lukketsvane/GK4_TRIXIG/assets/generated/gen_26_05/06_ideation_grids/trixig_260526_u157_square-loop-concept-board.png

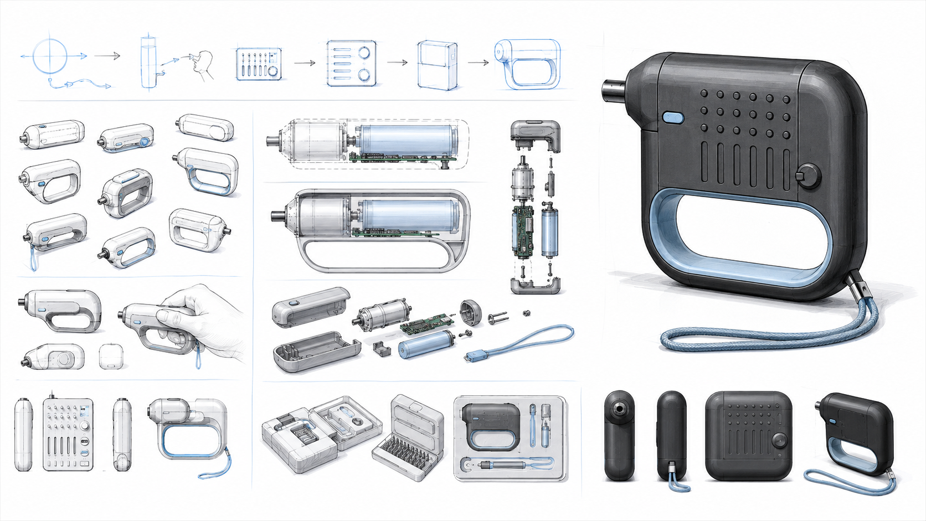
assets/generated/gen_26_05/06_ideation_grids/trixig_260526_u157_square-loop-concept-board.png
