lukketsvane/GK4_TRIXIG/docs/deliverables/08_mai_konseptgjennomgang/3b_analyse_trixig.docx

3B-analyse: TRIXIG 3,6 V

Akse | Kjernesvar
Brukar | Ung-vaksen, 20–40 år, første heim, ingen verktøyerfaring, IKEA-kunde, estetisk sensibel, prisbevisst.
Bruksituasjon | Hjemme på parkett, dårleg arbeidsljos (difor LED i nesen), kortintensiv 20–60 min, månader utan bruk mellom.
Bruksmåte | Pistolgrep, fast sekvens, retningsval er einaste reelle avgjerd, ingen koplingsbegrensing, brukaren må sjølv vurdera når skruen er ferdig.
