lukketsvane/GK4_TRIXIG/docs/project/trixig_konseptsprang.md

# TRIXIG — konseptsprang, ikkje arketypar

**Premiss:** Slutte å spørje "kva form skal ein skrutrekkar ha". Spørje i staden: *"kva er TRIXIG når han ikkje lenger er eit verktøy?"* — er han smykke, bordpynt, leppestift, klatreutstyr, fyllepenn, ikon? Kvar omramming gjev ein heilt annan brukaravtale.

Felles teknisk gulv (uansett konsept):
- 1 stk 18650-celle (ø18 × 65 mm)
- 1 stk gearmotor (ø25 × 60 mm) med utgåande aksel
- PCB (slank), trigger, USB-C-port

---

## KONSEPT 1 — KARABINIEREN
*Skrutrekkaren som lever på ryggsekken og veggkroken.*

Ikkje "verktøy i skuffa" — verktøy som heng saman med nøklane. Ein slank stav i anodisert aluminium med ein ekte klatrekarabin i enden. Når du går på fjellet, monterer ei IKEA-hylle, eller hjelper naboen — han er der. Statusobjekt for den som likar Olight, Leatherman, Lamy. Estetikk: kald metall, grå/svart/oliven, grov knurling, tydelege gjenger.

**Referanseunivers:** *EDC (every-day-carry), klatre, fyllepenn-presisjon*

| # | Referanse | Designar / år | Kva ein hentar |
|---|---|---|---|
| 1.1 | **Lamy 2000 fyllepenn** | Gerd A. Müller (Ulm-skulen), 1966 | Strikt sylinder, makrolon + børsta stål, knurla grep. Den definitive "edle staven". |
| 1.2 | **Olight i3T EOS lommelykt** | Olight | Single-cell EDC-arketype. Lommeklips. Knurling. |
| 1.3 | **Black Diamond HotForge karabin** | Black Diamond | Den tekniske karabinen, ikkje den dekorative. |
| 1.4 | **Leatherman Style PS** | Leatherman | Liten, klips, multifunksjonsspråk utan bling. |
| 1.5 | **Maglite Solitaire** | Anthony Maglica, 1988 (MoMA) | Single-cell ikon med nøkkelring-øye. |
| 1.6 | **Best Made Co. felling axe** | (kuratert) | Ulm møter Vermont. Korleis "verktøy" blir "objekt med sjel". |

---

## KONSEPT 2 — LEPPESTIFTEN (inversjonen)
*Ladaren er hovudobjektet. Skrutrekkaren er berre tuppen som skrur ut.*

Radikalt. Tenk Estée Lauder eller Diptyque parfymeflakong. På bordet ditt står ein vakker tubeform — kanskje keramikk, kanskje børsta messing, kanskje sandblåst glas — som ladar. Når du treng skru, vrir du toppen av: ut kjem den vesle motoren med chuck. Battericella sit i sokkelen og ladar induktivt. Kjøkkenkompatibel, soverom-kompatibel, gåvepakke-kompatibel.

**Referanseunivers:** *parfyme, sminke, ritualobjekt*

| # | Referanse | Designar / år | Kva ein hentar |
|---|---|---|---|
| 2.1 | **Aesop Marrakech parfymeflakong** | Aesop | Materialgravitas. Apotek-arv. |
| 2.2 | **Diptyque keramikklysstake** | Diptyque | Keramikkdock som *skjuler* funksjon. |
| 2.3 | **Tom Ford Black Orchid leppestift** | Tom Ford Beauty | Vekt, magnetlokk, klikk-følelse. |
| 2.4 | **Le Labo Santal 33 i flakong + boks** | Le Labo | Etiketten. Det handverka. |
| 2.5 | **Hermès Twilly perfume case** | Hermès | Skinn + metall = ritual. |
| 2.6 | **MUJI aroma diffuser, sylinder** | Naoto Fukasawa | Den japanske kjøkken-kompatible sylinderen. |

> Bonus: dette er det einaste konseptet som *opphøgjer ladinga til ein del av produktopplevinga* — jamfør Sonicare-glasset, men løfta til kosmetikk-nivå.

---

## KONSEPT 3 — BORDORNAMENTET
*Verktøyet som er for vakkert til å gøyme bort.*

Står på kjøkkenbenken som ei lita statue ved sida av Peugeot pepperkverna og Bialetti Moka. Vertikal totem, kanskje ovoid, kanskje konisk, i støypt aluminium eller olja eik. Bits står som ei lita krans rundt sokkelen — som krydder eller smykke. *Du eig han fordi han er fin.* Funksjonen er bonus.

**Referanseunivers:** *kjøkkenikon, bordtilbehør, italiensk handverk*

| # | Referanse | Designar / år | Kva ein hentar |
|---|---|---|---|
| 3.1 | **Bialetti Moka Express** | Alfonso Bialetti, 1933 | Det italienske kjøkkenikonet — funksjon som monument. |
| 3.2 | **Peugeot Paris u'Select pepperkvern** | Peugeot, 1874 (modell) | Tre + stål kolonne. 150 år utan å trenge fornying. |
| 3.3 | **Alessi 9090 espressokokar** | Richard Sapper, 1979 (Compasso d'Oro) | Stål-skulpturen. |
| 3.4 | **Jasper Morrison Mokka** for Alessi | Jasper Morrison, 2014 | Same arketype, supernormal-redux. |
| 3.5 | **Sori Yanagi støpejernspanne** | Sori Yanagi, 1953 | Japansk handverkstyngde. |
| 3.6 | **Eames House Bird** | Charles & Ray Eames, 1910-tal trefigur, gjort til ikon | Det reine bordobjektet utan funksjon. |
| 3.7 | **HAY Sowden kjelar** | George Sowden, 2017 | Korleis ein bryt opp ein tung form med flate fargar. |

---

## KONSEPT 4 — DET FOLDBARE OBJEKTET
*Ein kompakt blokk som klikkar opp i skruposisjon.*

Lukka: ein liten, slank ingot — passar i pennalet, jakkelomma, IKEA-skuffa. Opna: motorhuset svingar 90° eller 180° ut frå battericella og låsest med eit klikk. To stilbare posisjonar gjev anten *pistol* eller *inline*-bruk. Brukaren forhandlar grepet med produktet. Mekanisk dialog, ingen elektronikk.

**Referanseunivers:** *foldbart handverk, sveitsisk presisjon, modulærdesign*

| # | Referanse | Designar / år | Kva ein hentar |
|---|---|---|---|
| 4.1 | **Victorinox Pioneer Alox** | Victorinox, 1957 | Den ærlege foldemekanismen. Klikket. |
| 4.2 | **Olfa SVR-2 snap-blade kniv** | Olfa, Yoshio Okada, 1956 | Japansk teknisk ikon. Funksjonell glide. |
| 4.3 | **Black+Decker Gyro 4V** | (verktøy, men berre formreferanse) | Justerbart hovud — pivotmekanikken. |
| 4.4 | **BaByliss reise-hårfønar foldbar** | BaByliss | Kvardagsleg foldemekanikk i hushald. |
| 4.5 | **Joseph Joseph Elevate-skje med stative-fold** | Morph Design | Folde-leksis i kvardagskjøkken. |
| 4.6 | **Magis Chair_One stack-mekanisme** | Konstantin Grcic, 2003 | Korleis to volum låser i kvarandre. |
| 4.7 | **Vintage taske-reise-strykjern (1960-tal)** | Diverse | Den dramatiske transformasjonen lukka→open. |

---

## KONSEPT 5 — AMULETTEN
*Skrutrekkaren som heng på snor rundt halsen — eller på nøkkelringen, beltet, ryggsekken.*

Du gøymer han ikkje. Han er smykke. Liten, tung, taktil — i messing, titan eller børsta stål. Snorøye eller karabin innebygd. Hentar arven til mekaniske lommeur, militær-dogtags, og Tile/AirTag. Den eksisterande TRIXIG-snora er allereie eit hint — me dyrkar det.

**Referanseunivers:** *smykke, lommeur, militær-EDC, hi-tech wearables*

| # | Referanse | Designar / år | Kva ein hentar |
|---|---|---|---|
| 5.1 | **Apple AirTag** | Apple ID, 2021 | Liten, runda, premium polert. Snor-kompatibel. |
| 5.2 | **Tile Mate** | Tile, 2012 | Den vesle smarte-tinga som lever på nøkkelring. |
| 5.3 | **Casio F-91W på snor** | Casio, 1989 | Folkets EDC-amulett. |
| 5.4 | **Vintage Patek Philippe lommeur** | Patek Philippe | Premium "objekt-i-vest-lomma". |
| 5.5 | **Nendo dog-tag-baserte produkt** | Oki Sato / Nendo | Japansk minimalisme i wearable. |
| 5.6 | **Bauhaus dogtag-medaljongar** | Diverse Bauhaus-arv | Geometrisk reduksjon på snor. |
| 5.7 | **Carhartt WIP karabin-nøkkelring** | Carhartt | Korleis "industrielt" blir "modesmykke". |

---

## KONSEPT 6 — STEINEN
*Skulpturell pebble som ligg i handflata. Ingen synleg knapp.*

Henta frå sjøsleip stein og japansk wabi-sabi. Heile kroppen er trigger — du klemmer eller pressar mot skruen, motoren startar. Materiale: matt PA12 i jordtonar, eller terazzo-aktig støypt resin. Ingen merker, ingen logo. Ligg på vindaugskarmen som ein souvenir frå ein strand.

**Referanseunivers:** *japansk minimalisme, naturskulptur, Without Thought*

| # | Referanse | Designar / år | Kva ein hentar |
|---|---|---|---|
| 6.1 | **±0 humidifier (rund)** | Naoto Fukasawa, 2003 | Without Thought-arketypen. |
| 6.2 | **Isamu Noguchi Akari-lampe** | Isamu Noguchi, 1951+ | Organisk volum med papirsjel. |
| 6.3 | **Sori Yanagi Butterfly Stool** | Sori Yanagi, 1954 | Korleis to enkle skåler dannar ein heil ting. |
| 6.4 | **MUJI utan-logo-objekter** | MUJI / Fukasawa, Sam Hecht | Reduksjonsfilosofi. |
| 6.5 | **Lemnos Riki Clock** | Riki Watanabe, 1950-tal | Trereduksjon. |
| 6.6 | **Brâncuși "L'Oiseau dans l'espace"** | Constantin Brâncuși, 1923 | Skulpturreferansen — proporsjonar utan funksjon. |
| 6.7 | **Aesop Skin Care-flakongar (matt brun)** | Aesop | Kjelder for taktile matte overflater. |

---

## KONSEPT 7 — BUEN (bow drill-renessansen)
*Tilbake til den eldste boreteknologien menneske kjenner — bogeboret. Reframe-a som elektrisk objekt.*

Ein C-form. Pekefingeren ligg inne i C-en. Den eine enden er motor + chuck, den andre er battericella. Rom for handa i midten. Resultatet ser ut som augenbrynscurlar, fele-bue eller arkaisk handsmykke. Ergonomisk: aksial reaksjonskraft tas opp diagonalt mot underarmen, ikkje vinkelrett som med L-form. Du *omfamnar* verktøyet.

**Referanseunivers:** *arkaiske verktøy, musikkinstrument, kosmetikkverktøy*

| # | Referanse | Designar / år | Kva ein hentar |
|---|---|---|---|
| 7.1 | **Bogebor (arkeologisk)** | Mennesket, ~5000 f.Kr. | Den opphavlege boreformen. Symbolsk vekt. |
| 7.2 | **Shu Uemura augenbrynscurlar** | Shu Uemura | C-form på ergonomisk masterclass. |
| 7.3 | **Pernambuco felebue** | Tradisjon | Spenninga, balansen, det handverka. |
| 7.4 | **Marc Newson Lockheed Lounge** | Marc Newson, 1986 | Kontinuerleg flytande overflate. |
| 7.5 | **Eames LCW-stol** | Charles & Ray Eames, 1946 | Korleis to volum koplast med ein bro. |
| 7.6 | **Fritz Hansen Series 7 ryggstø** | Arne Jacobsen, 1955 | Kontinuerleg kurve som strukturelt prinsipp. |
| 7.7 | **Theragun PRO triangelhandtak** | Therabody | Moderne C/triangel-grep. |

---

## KONSEPT 8 — TVILLINGSYLINDRANE (magnetisk modulær)
*To like sylindrar som klikkar saman magnetisk. Kvar for seg er dei eigne objekt. Saman er dei skrutrekkar.*

Sylinder A: battericella, lader, USB-C, lyser i botn. Sylinder B: motor, chuck, knapp. Du tek dei med deg kvar for seg — A blir powerbank, B blir manuell skrutrekkar. Saman: eit bordlangt objekt med magnet i midten som lader pinge-følelsen til AirPods-etui og MagSafe.

**Referanseunivers:** *magnetisk premium, modulærleik, Apple ID*

| # | Referanse | Designar / år | Kva ein hentar |
|---|---|---|---|
| 8.1 | **Apple MagSafe-ladar** | Apple, 2020 | Magnet-klikket. Det elegante "snap". |
| 8.2 | **B&O Beoplay E8 etui + buds** | Jakob Wagner, 2017 | Skinn + magnet. |
| 8.3 | **Foreo Luna play + dock** | Foreo | Kompakt sylinder + sokkel. |
| 8.4 | **Nendo "Twin Drink" jingle-konsept** | Nendo / Oki Sato | To former som forhandlar. |
| 8.5 | **Hermès silkkrok-ringar** | Hermès | Ritualet å samle/skille. |
| 8.6 | **Olympus Pen-F kamera** | Olympus, 2016 | Premium tvillingelement (kropp + linse). |

---

## KONSEPT 9 — SLIK-SOM-MÅLEBANDET (Stanley FatMax-energi)
*Eit kompakt rektangulært ingot — som eit målebånd, ein USB-C lommepowerbank, eller ein vintage sigarettetui — der bittet popper ut frå ein kortside.*

Tenk Stanley FatMax målebånd møter Apple-design. Eller LaCie Rugged hard disk. Du klikkar ein knapp på toppen, motorhuset glir ut frå ein side. Battericella ligg flat under, motoren ligg horisontalt. Form blir noko aldri sett før i verktøykategorien — meir lik ein gadget enn ein drill.

**Referanseunivers:** *gadget, vintage tool, premium consumer electronics*

| # | Referanse | Designar / år | Kva ein hentar |
|---|---|---|---|
| 9.1 | **Stanley FatMax målebånd** | Stanley, 1990-tal | Industriell rektangulær arketype. |
| 9.2 | **LaCie Rugged Mini SSD** | LaCie / Neil Poulton, 2009 | Premium ingot med gummi. |
| 9.3 | **Vintage Dunhill sigarettetui** | Dunhill, 1920-tal | Smal rektangulær luksus. |
| 9.4 | **Olfa cutters i lommeformat** | Olfa | Skyte-mekanisme. |
| 9.5 | **Zippo lighter** | George Blaisdell, 1933 | Klikket. Det ergonomiske rektangelet. |
| 9.6 | **Braun ET-66 kalkulator** | Dieter Rams, 1987 | Den minimalistiske rektangulære disiplinen. |

---

## KORT SAMANDRAG — kva du tek inn i Figma

```
KONSEPT          MENTAL OMRAMMING                  KJERNE-REFERANSE
1 KARABINIER     verktøy → EDC-utstyr              Lamy 2000 + Black Diamond
2 LEPPESTIFT     verktøy → kosmetikk-ritual        Aesop + Tom Ford
3 BORDORNAMENT   verktøy → kjøkkenmonument         Bialetti + Peugeot
4 FOLDBAR        verktøy → sveitsisk transformer    Victorinox + Olfa
5 AMULETT        verktøy → smykke / wearable       AirTag + Casio F-91W
6 STEIN          verktøy → wabi-sabi-objekt        Fukasawa + Brâncuși
7 BUE            verktøy → arkaisk omfavning       Bogebor + felebue
8 TVILLING       verktøy → magnetisk modul         MagSafe + B&O E8
9 INGOT          verktøy → premium gadget          Stanley + LaCie
```

---

## Anbefaling for første runde i Figma

Velg **3 konsept** å utvikle vidare — eg foreslår spennvidde:
- **Konsept 2 (LEPPESTIFT)** — heilt utfordrande mental omramming
- **Konsept 4 (FOLDBAR)** — teknisk-mekanisk ambisjon
- **Konsept 1 (KARABINIER)** eller **5 (AMULETT)** — relasjon til den eksisterande snora

Då har du éit konsept som er romantisk, eitt som er mekanisk, eitt som er kvardagsleg-EDC. Tre forskjellige forteljingar å teste mot brukargruppa.

Når du har plassert referansane: sei frå, så hjelper eg deg med pakkings-skissar og ergonomi-resonnement for kvart konsept.

[Open konseptdokumentet](computer://C:\Users\Shadow\Documents\GitHub\GK4_TRIXIG\TRIXIG_konseptsprang.md)
