lukketsvane/GK4_TRIXIG/docs/project/note.md

La oss starte med å rydde i koden. Gå deretter inn i skisser-mappa og gi alle filene bedre navn etter en tydelig konvensjon, for eksempel skisse_01, skisse_02 osv.

Etter det skal du gå nøye gjennom hvert eneste bilde, vurdere og sammenligne dem, helt til vi står igjen med de 3–10 desidert beste. Disse kan vi så arbeide videre med.
