lukketsvane/GK4_TRIXIG/docs/brand/brandmark_trixigplus.md

# Brand-mark for TRIXIG+

*Designforslag for ordmerke til Trixig+, basert på prinsippet om at typografi kan ha innebygd produkt-semantikk. Knytt til Formføringsplansje_11mai.md (verdiord: truverdig).*

Forfattar: [Studentnamn]
Dato: 27. april 2026

---

## Premiss

Eit ordmerke for eit verktøy bør ikkje vera ein generisk wordmark plassert oppå produktet. Han bør innehalda noko av det produktet *gjer*. Den dekonstruerte IKEA-logoen som er referert som inspirasjon (sjå `referanse/`) gjer akkurat det: K-en blir ein retningspil, E-en får ein skrue-spor-slits, A-en blir ein flatpakk-trekant. Tre einkle gestar, kvar med innebygd semantikk.

Brand-marken for TRIXIG+ tek same prinsipp og oversett han til prosjektets eigen kontekst.

## Forslag

```
   ┌──────────────────────────────────────┐
   │                                      │
   │   T R I X I G +                      │
   │   ─       ─    ↑                     │
   │   |       |    fjørkontakt-          │
   │   |       |    indikator             │
   │   |       |                          │
   │   slits   slits                      │
   │   (T-bit) (Pozi)                     │
   │                                      │
   └──────────────────────────────────────┘
```

Tre tekstlege grep, ein fysisk gest:

**1. T-en har Torx-stjerne i horizontal slik.** Ein lett asymmetrisk seksstjerne-form innfelt i vertikal-stammen. Les seg som T på avstand, som Torx-bit-snitt på nært hald. Refererer direkte til dei seks Torx T10-skruvene som er sjølve identiteten til Trixig+ ('reparerbar').

**2. G-en har eit Pozidriv-tverr i opninga.** Den karakteristiske Pozidriv-stjerna (kryss + diagonal) er innfelt der G-en sluttar inn mot midten. Sub-tilt nok til å lesast som G på avstand; tydeleg på nært hald.

**3. Plus-symbolet er ein status-indikator.** "+" etter TRIXIG har dei fire armane med liten rund prikk i kvar — som dei fire status-LED-prikkane på skrutrekkaren sin bakvy. Plusset er både ord-element og funksjonsmotiv.

## Typografi-grunnlag

Skrifttype: ein modifisert Verdana Bold (IKEAs eigen referanse-grotesk) eller Akzidenz Grotesk Bold som svensk-historisk parallell. Om Verdana brukast, skal ho strammast horizontal med 5 % for ikkje å bli IKEA-original-identifisk.

Kerning: jamn, ikkje optisk. TRIXIG+ skal lesast som éin block, ikkje som spaced lettering.

Vekt: 700 (Bold). Ikkje Black — det blir for industrielt. Ikkje Regular — det forsvinn på lite skala.

Storleik på produkt: minimum 8 mm høgd for å vera lesbar etter debossing i ABS.

## Fargesystem

To variant:

**Variant A — full IKEA-logikk:** IKEA-blå (Pantone 280 C, omtrent #003F94) som dominant flate, IKEA-gul (Pantone 116 C, omtrent #FFD600) som typografi-farge. Kun til marknadsføring og digitalt bruk.

**Variant B — produkt-debossing:** Berre debossa direkte i ABS, ingen paint fill. Reint material, ingen farge. Dette er den primære varianten på sjølve verktøyet — i tråd med "truverdig"-verdiordet (material som det det er).

Variant B vinn for produktet sjølv. Variant A finst kun i digital og trykt kommunikasjon.

## Plassering på produktet

På Trixig+ sin venstre side, debossa direkte i ABS, plassert på den glatte flata mellom partingline og stroppfeste-løkka. Storleik: 12 mm høgd. Synleg, men ikkje dominerande — han kommuniserer brand utan å skrika.

På batteripakken (om reservebatteri produserast separat): same merke debossa, men 8 mm høgd, plassert sentrert.

## Gjenkjenning på avstand

Test: prøv merket på 30 cm, 1 m, 3 m. Kva les seg?

- 30 cm: TRIXIG+, alle detaljar synlege (Torx-T, Pozi-G, prikkar i +)
- 1 m: TRIXIG+, glatt typografi, prikkar i + framleis synlege
- 3 m: TRIXIG, plus-symbolet glir saman til éin prikk

Den glidande oppløysinga er meininga. På avstand er merket ein kjend brand. På nært hald er han ein tale om produktet sin reparérbarheit. Brukaren oppdagar koplinga først når han faktisk har verktøyet i handa.

## Forhold til IKEA-master-merket

TRIXIG+ er sub-brand under IKEA. Brand-merket må difor co-eksistera med IKEA-logoen. To plasseringar:

**Lock-up (vertikal):** IKEA-logo over, TRIXIG+ under, separert av ein 2 mm tynn horisontal regel. Brukast på pakning og trykt materiale.

**Sub-merking (horisontal):** TRIXIG+ åleine, IKEA-logo i ein hjørne av pakninga separat. Brukast på sjølve produktet (ingen IKEA-logo direkte på verktøyet, kun TRIXIG+).

## Kva det ikkje er

Eit forsøk på å erstatta IKEA-merket. Den dekonstruerte IKEA-logoen i `referanse/` er inspirasjon for *prinsippet* (typografi med innebygd produkt-semantikk), ikkje for *biletet*. Brand-marken for TRIXIG+ skal ikkje sjå ut som ein modifisert IKEA-logo — det er forvirring og potensiell varemerke-konflikt.

## Vidare arbeid

Tre konkrete neste steg om brand-marken vert valt for vidareutvikling:

1. **Skissa T-en og G-en frihand.** Sjå om Torx-stjerna i T-stammen og Pozi-tverret i G-opninga faktisk fungerer typografisk, eller om dei vert for støyande.
2. **Test på reell ABS-modell.** Debossing-djupna avgjer leselegheit — skiltvanleg er 0,3–0,5 mm under overflate. Test på blåskum-modell først.
3. **Konsulter Anna Martine Nilsen** (kursveileder for brandmarkører) i veke 19 for kritisk gjennomgang før formføringsplansje-leveransen 11. mai.

---

*v1.0 — 27. april 2026. Inspirert av referansebilete i `referanse/` (dekonstruert IKEA-logo). Forslaget er konseptuelt og krev typografisk utvikling før produksjon.*
