lukketsvane/GK4_TRIXIG/docs/project/formfringsplansje_11mai.md

# Formføringsplansje — Trixig+

*GK4 V26 Modul 2. Innlevering Moodle innan måndag 11. mai 2026 kl. 09:00. Gjennomgang i gruppeseanse onsdag 13. mai med Nina Bjørnstad.*

Forfattar: [Studentnamn]
Dato: 11. mai 2026

---

## Tre verdiord

**Synleg. Stille. Truverdig.**

Verdiorda er valde for å samtidig (i) artikulera Trixig+ sin formdriver — radikal reparérbarheit gjort eksplisitt — og (ii) halda seg innanfor IKEA-DNAet, slik at produktet ikkje fell utanfor TRIXIG-serien sitt eksisterande visuelle vokabular. Dei tre orda dannar eit triangel: kvar av dei korrigerer ein moglig overdriving av dei to andre.

---

## Synleg

Synleg tyder at det funksjonelle prinsippet — at verktøyet er reparerbart — skal vera lesbart utan tekst. Dei seks Torx T10-skruvene står på utsida av kapslinga, ikkje under merkelapp. Status-LED-stripa er innfelt men ikkje gøymd. ISO-merkinga er innstøypt direkte i polymeren der ho synast under demontering. Ingenting er skjult under lim, klistreikon eller "design"-deksel.

Dette er ein invitasjon til å demontera, ikkje ein varsel om å la det vera. Synleg er den motgangen til "skapt mangel"-mekanismen — du kan ikkje skjula det du har bygd, og du kan ikkje by­byggja det du har vist fram.

**Referanseobjekt:** Festool ETS-rondellsliper (synleg modulær skruegjennomgang i grepet), Vola FS1 vasskran (mekanikken er synleg, ikkje skjult under design­chrom), Olivetti Lettera 22 (alle skruver kjente, alle deler nemlege).

**Visuelt vokabular:** flate, ærlege flater. Ingen falske partingslines. Ingen påklistra "feature"-dekk. Skruehovuda er fysisk reelle objekt på overflata. Synleg betyr ikkje teknisk nakent — det betyr at det funksjonelle vert oppløst som visuelt motiv.

---

## Stille

Stille tyder at produktet ikkje skrik. Det er ei reaksjon mot den dominerande retninga i forbrukar­elektroverktøy, der visuell aggresjon (skarpe vinklar, fluorescent grøn på Ryobi, signal-raud på Milwaukee, fettkokt mat-grafikk på DeWalt) er kommersielt korrelert med opplevd performanse. Trixig+ fullfører ikkje den tradisjonen.

Stille er òg eit IKEA-ord. TRIXIG-serien har allereie ein lågmælt tone — myk pistolform, dempa svart-grå-fargesetjing, ein einsleg orange aksent. Trixig+ tek dette tonefallet eit hakk lenger inn: oransje vert reservert til eit einaste relieff (pil-relieffet på den konvekse retningsbrytarsida) og éin enkelt lyspunkt (den aktive status-LEDen). Resten av produktet er monokromatisk svart-grå.

Stille er motgangen til opplevd-pris-inflasjon. Det er ein deklarasjon om at verktøyet ikkje treng å overtyda om kvaliteten sin gjennom signal — kvaliteten er den utskiftbare cella, dei opnande skallene, den asymmetriske brytaren. Forma sjølv held seg ut av vegen for funksjonen.

**Referanseobjekt:** Braun T1000 transistor­radio (Dieter Rams, lågmælt formspråk), Muji CD-spelar av Naoto Fukasawa (fråvær av visuell støy), Olivetti Valentine i den ikkje-røde versjonen.

**Visuelt vokabular:** myke radiar (R3 til R8), inga skarpe industri­vinklar, ein einsleg signaturfarge brukt med disiplin, typografi i einsleg vekt og storleik, ingen "extreme grip"-mønster i overstøp.

---

## Truverdig

Truverdig tyder at materialet ser ut som det det er. ABS-en er matt, ikkje gloss; han er svart, ikkje "soft-touch"-imitasjon av gummi. Stålet i bitsfestet er børsta, ikkje krom. Magneten er synleg som eit metallisk grått ringen; han er ikkje innebygd bak ei plastskilje. Aluminiumet i innvendige strukturelement (om det blir brukt) er anodisert i naturleg metallisk grå.

Dette er motgangen til "premium feel"-strategien som dominerer forbrukar­elektronikk: glansa overflater, krom-aksent, soft-touch-rubber, mat-svart-pulverlakk over termisk-mediokkar plast. Trixig+ avstår fordi avstand mellom material og uttrykk er sjølve kjelda til mistillit. Eit produkt som lyg om materialet sitt vil lyga om levetida si.

Truverdig er òg den tonefallet som produsent-bedrifta IKEA strever for å levera i sin breiare kommunikasjon, men ikkje alltid lukkast med. Trixig+ trekkjer dette ein millimeter lenger.

**Referanseobjekt:** Braun ET 88 kalkulator (knappar er knappar, plast er plast), Vitsoe 606 hyllesystem (aluminium i si rette form), Festool batteripakke (synleg mekanikk, ærleg material).

**Visuelt vokabular:** matt finish som standard, glans berre på funksjonelle overflater (børsta stål der friksjon krevjast), ingen fargelegging av material som ikkje treng det (ABS er svartpigmentert i støyping, ikkje sprøytemåla), pregnante tekstur skilnader mellom material­fraksjonar.

---

## Tilpassing til IKEA-brand og TRIXIG-serien

Trixig+ må kjennast som TRIXIG. Det betyr disiplin på tre dimensjonar:

**Form-DNA.** Den softe pistolforma med 110° grepvinkel er behaldt utan endring. Hovudradiar (R5 i grepets kontur, R8 i nesen) er behaldt. Den karakteristiske TRIXIG-stroppfeste-løkka i bakkant er behaldt. Endringane er konsentrert om dei *flatene* der dei opererer, ikkje om silhuetten.

**Farge-DNA.** Svart matt ABS pluss éin oransje aksent. Det er IKEAs eksisterande TRIXIG-palett. Forskjellen er at oransje vert *meir* disiplinert i Trixig+ — i originalen finst det nokre oransje detaljar fleire stader, i Trixig+ er han reservert til retningsbrytarens pil-relieff og éin status-LED. Mindre oransje, men oransje meir betydningsbærande.

**Detalj-DNA.** Skrifttype er IKEAs eigen Verdana-derivative for produkt­merking. Logo-plassering på underdelen av grepet, ved siden av stroppfestet, debossa utan paint fill. Modellbetegning "TRIXIG+" debossa, ikkje malt. Inga nye fargar, ingen nye fontar, ingen nye geometriske element.

**Brand-mark som ber semantikk.** Sjå `Brandmark_TrixigPlus.md` for forslag der TRIXIG+-ordmerket har Torx-stjerne innfelt i T-stammen, Pozidriv-kryss i G-opninga, og fire prikkar i plus-symbolet (refererer til status-LED-stripa). Inspirert av referansebilete i `referanse/` (dekonstruert IKEA-logo) der typografi har innebygd produkt-semantikk. Forslaget skal under verdiordet *truverdig* — typografi som *gjer* det produktet er, ikkje berre nemner det.

Dette er konservativ tilpassing, og det er meininga. Trixig+ er ikkje eit nytt produkt; han er ein revisjon. Brand-arbeidet er å la han kjennast som ein revisjon, ikkje som ein avgreining.

---

## Hovudform → elementform → detaljering → material­eigenskapar

**Hovudform.** Behaldt frå original TRIXIG: myk pistol, ~170 mm total lengd, ~110° grepvinkel, ~350 g vekt med 18650-celle. Silhuett er identifisk frå ein meter avstand.

**Elementform.** Tre nye hovudelement vert sette inn i hovudforma: (i) den asymmetriske retningsbrytaren erstattar den symmetriske vippepinnen, plassert i same posisjon på øvre bakvy; (ii) status-LED-stripa kjem inn som ein ny horisontal ribbe på øvre bakvy under retningsbrytaren, ein ribbe som ikkje fanst i originalen; (iii) seks synlege Torx T10-skruver vert lagt langs partingslinja på sidekapslinga, tre per side, jamt fordelt frå nesen til grepets bakkant.

**Detaljering.** Pil-relieffet på retningsbrytaren har ein klar S-kurve mellom konveks og konkav side. Status-LED-stripa har fire 2 mm-runde vindauge i ABS-en, kvar med ein klar polykarbonat-innsats. Torx-skruvene har lett konkurrent senking slik at hovudet ligg ein halv millimeter under overflate, ikkje proud. ISO-merkinga er innstøypt på innsida av begge skall, lesbar berre etter demontering.

**Materialeigenskapar.** ABS PA-757 (eller ekvivalent) i 30 % rPCR-andel, matt mineral-finish (no glossing). POM grå (POM-C natural med svart pigment) for trekkar — same materiale som original. Stål A2 for skruver. Brushed steel 304 for bitsfeste-collaren. Neodym N42-magnet for bitshold (synleg).

---

## Ein setning som ber heile plansja

> *Trixig+ skal sjå ut som ein TRIXIG som ikkje har noko å skjula — same forma, same fargen, men med skruver, brytar og lys lagt ope nok til at brukaren forstår han kan opnast og fiksast.*

---

## Innleveringspakke 11. mai kl. 09:00

| Fil | Innhald |
|---|---|
| `Formføringsplansje_Trixig+.pdf` | Denne fila eksportert til ein A3 plansje med visuelle referansar |
| `Verdiord_referanseobjekt.jpg` | Tre visuelle referanseobjekt per verdiord (9 totalt), kompilert i éin plansje |
| `Formspråk_strekteikning.pdf` | Sideview av Trixig+ med dei tre nye elementa markerte |

**Konvertering:** Opne markdown i Word, formater som A3-plansje (sett opp som tabular layout med tre kolonner — éin per verdiord), eksportert til PDF.

**Visuelle referansar:** finn høgoppløyselege bilete av referanseobjekta (Festool ETS, Vola FS1, Olivetti Lettera 22, Braun T1000, Muji-CD-spelar, Olivetti Valentine, Braun ET 88, Vitsoe 606, Festool batteripakke) frå produsentenes pressebilete eller MoMA-kollokjonsdatabasen, lim inn med kjelde­henvising.

---

*v1.0 — generert 27. april 2026. Innlevering 11. mai 2026.*
