lukketsvane/GK4_TRIXIG/docs/reports/drill_ord_for_ord.docx

ESSAY

Drill, ord for ord

Eit forsøk på å lese éin IKEA-skjerm som om han er det han er

Det står to skrutrekkjarar på IKEA si norske nettside. Den eine kostar 179 kroner og heiter Drill. Den andre kostar 599 kroner og heiter Skrutrekker/drill.

Den billige er ingen drill. Ho har inga chuck for vanlege borebits, knapt moment, og er funksjonelt identisk med Bosch IXO frå 2003: ein liten elektrisk skrutrekkar med litiumcelle[^1]. Den dyre fungerer som ein ordinær hushaldsdrill. Den enkle einheita får det meir lovande namnet. Den meir kapable einheita får begge.

Dette er ikkje språkleg slurv. Det er forretningsmodellen kondensert til to bokstavar.

Lærepengen på 179 kroner

Den klassiske kritikken av forbrukarsamfunnet, formulert skarpast av John Kenneth Galbraith i The Affluent Society (1958)[^2], går slik: industrialisert produksjon må produsere sin eigen etterspurnad, fordi reelle behov er metta. Galbraith kalla dette den avhengige effekten. Produsenten fabrikkerer behovet han sjølv skal dekkje.

TRIXIG 3.6V er ein lærebokpresis implementasjon. Verktøyet er prisa lågt nok til impulskjøp og funksjonelt avgrensa nok til å garantere returbesøk. Det første produktet er ikkje konstruert for å lukkast med oppgåva namnet lovar. Det er konstruert for å definere oppgåva slik at neste produkt får meining.

Pris-stige (ladder pricing): Produktstruktur der kvart steg avslører avgrensinga ved det førre.

Differansen frå 179 til 599 kroner er ikkje ein produksjonsdifferanse. Det er prisen på erkjenninga om at det første kjøpet var ei bløff.

Den verkelege synda er sekstini år gammal

Spørsmålet er ikkje kva er TRIXIG. Det interessante er kvifor marknaden TRIXIG ekspanderer inn i, finst i det heile teke.

I 1956 fjerna IKEA-designaren Gillis Lundgren beina på Lövet-bordet for å få det inn i bilen. Britannica oppsummerer konsekvensen utan omsvøp: flatpakken kutta frakte- og lønnskostnader dramatisk[^3]. Andre ord, andre bokstav: lønnskostnader.

Flatpakken er ikkje primært ein logistikkinnovasjon. Han er ei lønnseksternalisering av ein storleik verda aldri hadde sett. Hundrevis av millionar nye monteringstimar i året, utført av folk utan handverkskompetanse, utan ordentleg verktøy, og utan kompensasjon. Rebranda som «sjølvmontering», «medskaping», «opplevinga ved å byggje sin eigen heim».

Eksternalisert arbeid: Når lønna fabrikkarbeid blir flytt over på ulønna forbrukarkraft, omdøypt til «valfridom».

Den reinaste forma for det Galbraith kalla den avhengige effekten.

Det var inn i denne marknaden Bosch lanserte IXO i 2003: ein liten litium-skrutrekkar designa for ein konsumentklasse som flatpakken sjølv hadde skapt. IXO er no i sjuande generasjon, med over tjue millionar einingar selde globalt. TRIXIG er IKEA si innfasing av denne arketypen, men plassert tilbake i økosystemet som genererte etterspurnaden.

Bosch og DeWalt og Makita sel verktøy til problem nokon andre skapte. IKEA er det einaste selskapet som har lukka heile sirkelen.

Sealed-by-design

Begge TRIXIG-modellane har forsegla litiumceller. Brukaren kan ikkje byte batteri. Når cella døyr etter tre til fem års bruk, må heile verktøyet kasserast.

EU sin batteriforordning 2023/1542 trer i kraft 18. februar 2027 og krev at batteri i portable produkt skal kunne fjernast og bytast med vanleg, kommersielt tilgjengeleg verktøy[^4]. Reguleringa identifiserer eksplisitt forsegla design som planlagd avhending. IKEA sender altså ut produkt som blir lovstridige innan to år.

Dette er ikkje teknisk konservatisme eller uvitenheit. Det er valet om å hauste medan vindauget framleis er ope. Levetida til verktøyet er kalibrert mot levetida til ein typisk IKEA-bokhylle. Ny bustad, nye møblar, ny montering, ny drill.

Den kompletteringsangsten ingen ber deg om å føle

IKEA si verkelege geni er ikkje produkta. Det er at heile kjeda av frustrasjon ligg innanfor éin selskapsstruktur:

1. Selskapet skapar problemet: flatpakken krev montering med skru.
2. Selskapet tilbyr eit pinleg utilstrekkeleg gratisverktøy: sekskantnøkkelen.
3. Selskapet sel det første betalte verktøyet som ikkje fungerer: 179 kroner.
4. Selskapet sel erstatninga du innser at du treng: 599 kroner.
5. Selskapet forseglar batteria slik at sløyfa repeterer seg.

Dette er ikkje produksjonseffektivitet. Det er konsumpsjons-ingeniørkunst: den disiplinerte konstruksjonen av forbrukarsubjektet sjølv, frå monteringsanvisning til avhending, til neste innflytting.

Og her ligg den breiare diagnosen. TRIXIG er ikkje ein anomali i kapitalismen. Han er kapitalismen i si reinaste artikulerte form, der eit selskap har klart det Marx skreiv om i tredje bind av Kapitalen[^5]: å kontrollere ikkje berre produksjonsmidlane, men reproduksjonen av behovet sjølv. Det selskapet sel, er ikkje først og fremst eit verktøy. Det er din eigen frustrasjon, returnert til deg, prisa i to nivå.

Tankeeksperimentet

Sett at IKEA fjerna 12V-modellen i morgon. Ville salet av 3.6V gå opp eller ned?

Hadde verktøyet vore ei sjølvstendig løysing på eit reelt problem, ville salet auke, sidan det no var einaste alternativ. Det ville sannsynlegvis falle. Fordi 3.6V ikkje er ei løysing. Han er eit steg. Utan stigen ovanfor, mistar steget si tyngdekraft.

Det er den enklaste empiriske testen av tesen: når du fjernar den dyre versjonen, mistar den billige meining. Når du fjernar IKEA-flatpakken, mistar begge meining. Verktøya finst fordi problemet finst, og problemet finst fordi selskapet ein gong i 1956 oppdaga at eksternalisert arbeid kunne seljast tilbake som forbrukargode.

Det vi eigentleg betalar for

Når du betaler 179 kroner for TRIXIG, betalar du ikkje for eit verktøy. Du betalar for retten til å oppdage at du treng eit ekte eit. Når du betalar 599 kroner for det neste, betaler du for retten til å gløyme at det første nokon gong skjedde.

Sekskantnøkkelen som lever i botnen av kvar IKEA-skuff i landet, er ikkje eit gratis tilbehør. Han er den materielle påminninga om kva du eigentleg har samtykt til. At nokon i 1956 oppdaga at handa di kunne settast i arbeid utan løn, og at nokon sidan har vore travelt opptekne med å selje deg verktøy som lindrar smerten den jobben påfører.

Drill, ord for ord, er den lyden eit selskap lagar når det har klart å selje deg ditt eige slit tilbake.

KJELDER

Britannica Money. Oppslag «Ingvar Kamprad». Britannica.com, sist oppdatert 2024.

Galbraith, John Kenneth. The Affluent Society. Boston: Houghton Mifflin, 1958.

Marx, Karl. Das Kapital, bind III. Hamburg: Meissner, 1894.

Europaparlamentet og Rådet. Forordning (EU) 2023/1542 om batteri og brukte batteri. Brussel, 12. juli 2023.

Right to Repair Europe. «Making Batteries Removable and Replaceable: a closer look at the new EU Guidelines.» repair.eu, februar 2025.

Bosch Home & Garden. Tekniske spesifikasjonar IXO 7. bosch-home-and-garden.com, 2024.

IKEA Norge. Produktsider TRIXIG 3.6 V og TRIXIG 12 V. ikea.com/no, henta april 2026.

[^1] Bosch IXO blei lansert i 2003 og er no i sjuande generasjon (IXO 7), med over tjue millionar einingar selde globalt. Spesifikasjonar: 3,6 V Li-ion, opp til 5,5 Nm moment.
[^2] Galbraith, John Kenneth: The Affluent Society (1958). Kapittel 11, «The Dependence Effect»: argumentet om at moderne produksjon skapar dei behova ho mettar.
[^3] Britannica Money, oppslag «Ingvar Kamprad»: «Kamprad introduced to IKEA's inventory flat-boxed furniture that was designed to be assembled at home. […] The new items decreased shipping and labour costs dramatically.» Britannica.com, oppdatert 2024.
[^4] EU-forordning 2023/1542 om batteri og brukte batteri, artikkel 11. Krev frå 18. februar 2027 at portable batteri skal kunne fjernast og bytast med kommersielt tilgjengeleg verktøy. Sjå òg Right to Repair Europe, februar 2025.
[^5] Marx, Karl: Das Kapital, bind III (1894), særleg avsnitt om reproduksjonen av kapitalforholdet og produksjonen av forbrukaren som økonomisk subjekt.

Drill, ord for ord
