lukketsvane/GK4_TRIXIG/assets/finished_graphics/figurar/figur_01.png

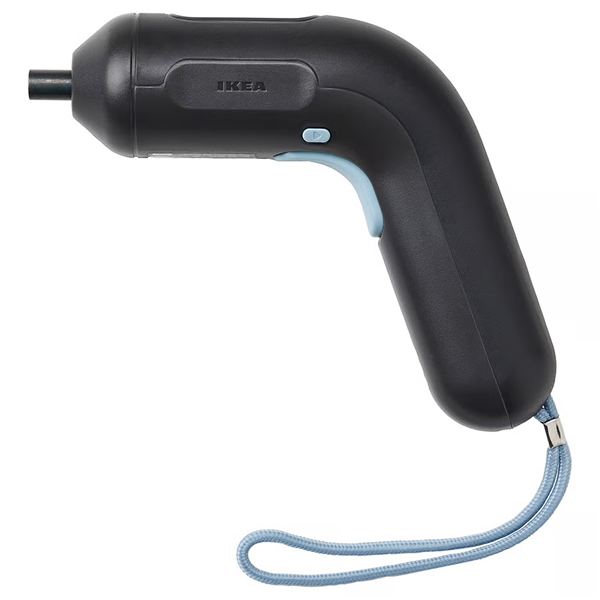
assets/finished_graphics/figurar/figur_01.png
