lukketsvane/GK4_TRIXIG/assets/finished_graphics/figurar/figur_03.png

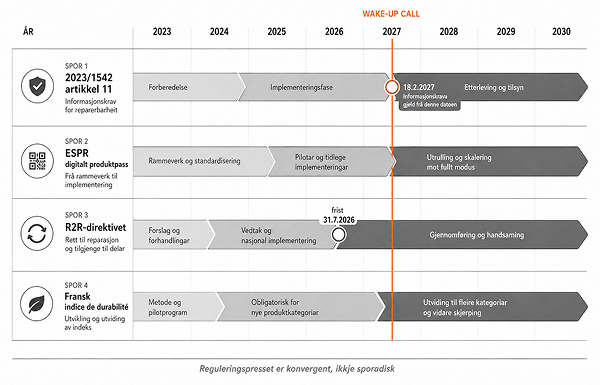
assets/finished_graphics/figurar/figur_03.png
