lukketsvane/GK4_TRIXIG/assets/finished_graphics/figurar/figur_05.png

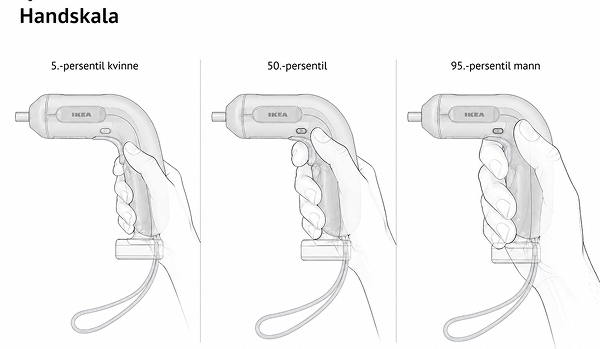
assets/finished_graphics/figurar/figur_05.png
