lukketsvane/GK4_TRIXIG/assets/finished_graphics/figurar/figur_09.png

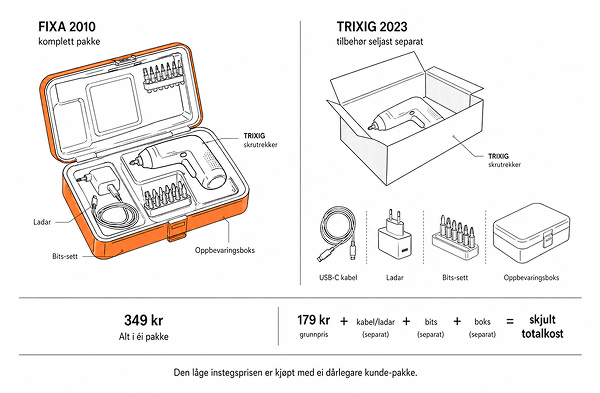
assets/finished_graphics/figurar/figur_09.png
