lukketsvane/GK4_TRIXIG/assets/finished_graphics/figurar/figur_12.png

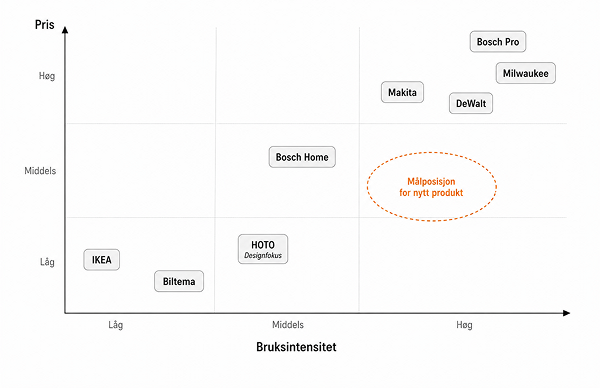
assets/finished_graphics/figurar/figur_12.png
