lukketsvane/GK4_TRIXIG/assets/finished_graphics/figurar/figur_13.png

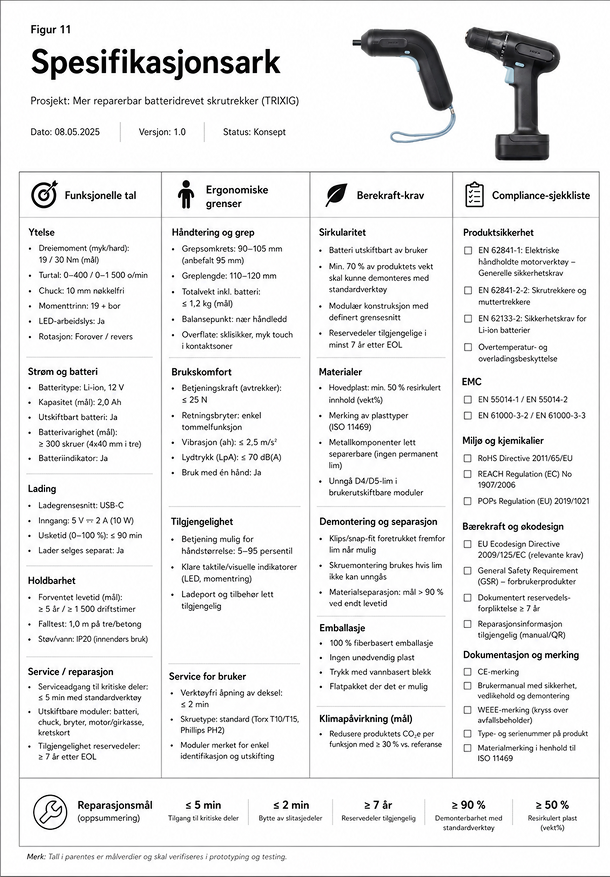
assets/finished_graphics/figurar/figur_13.png
