lukketsvane/GK4_TRIXIG/assets/finished_graphics/grafikk_02.png

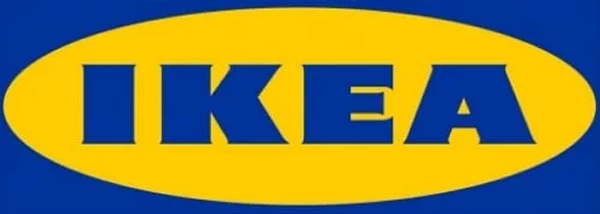
assets/finished_graphics/grafikk_02.png
