lukketsvane/GK4_TRIXIG/assets/finished_graphics/produksjonsliste_bilete_modell/modell_02.png

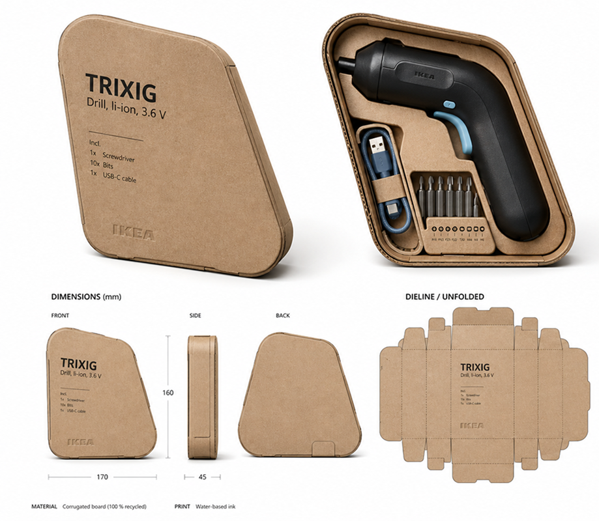
assets/finished_graphics/produksjonsliste_bilete_modell/modell_02.png
