lukketsvane/GK4_TRIXIG/assets/finished_graphics/produksjonsliste_bilete_modell/modell_05.png

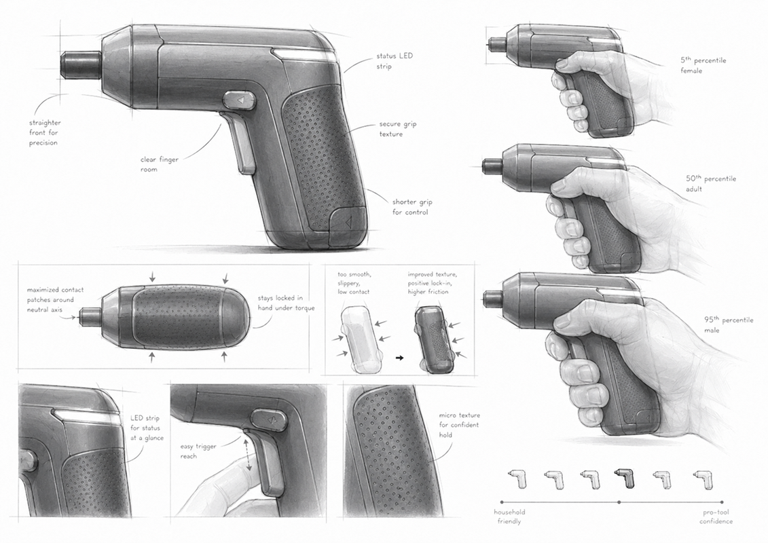
assets/finished_graphics/produksjonsliste_bilete_modell/modell_05.png
