lukketsvane/GK4_TRIXIG/assets/finished_graphics/produksjonsliste_bilete_modell/modell_12.png

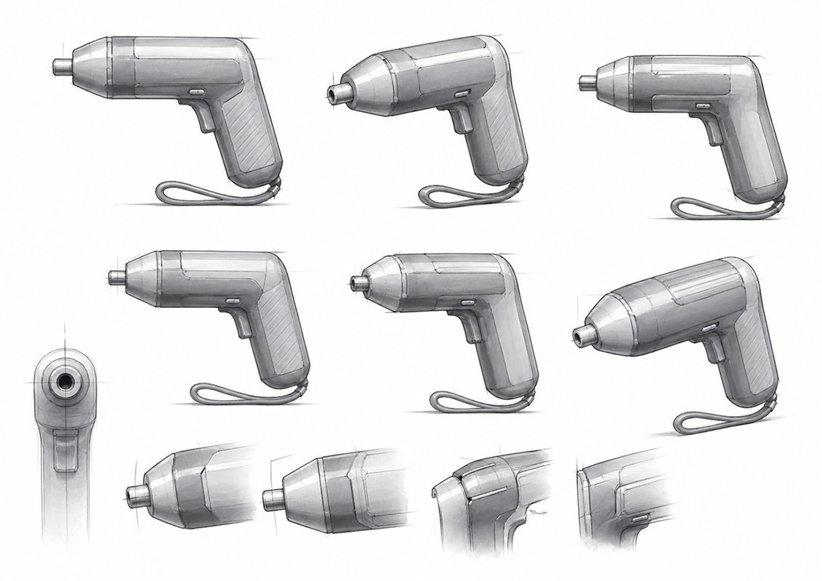
assets/finished_graphics/produksjonsliste_bilete_modell/modell_12.png
