lukketsvane/GK4_TRIXIG/assets/finished_graphics/skisser/frame_3.png

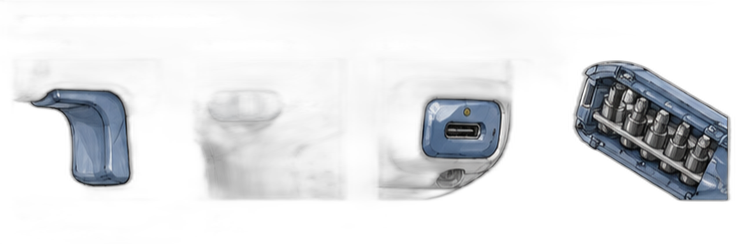
assets/finished_graphics/skisser/frame_3.png
