lukketsvane/GK4_TRIXIG/assets/finished_graphics/skisser/image_2.png

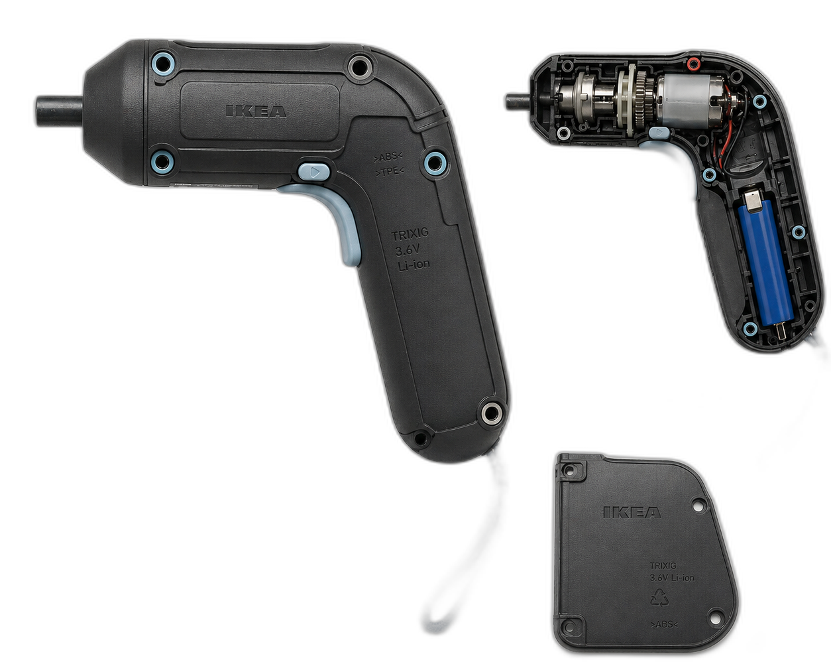
assets/finished_graphics/skisser/image_2.png
