lukketsvane/GK4_TRIXIG/assets/finished_graphics/skisser/image_3.png

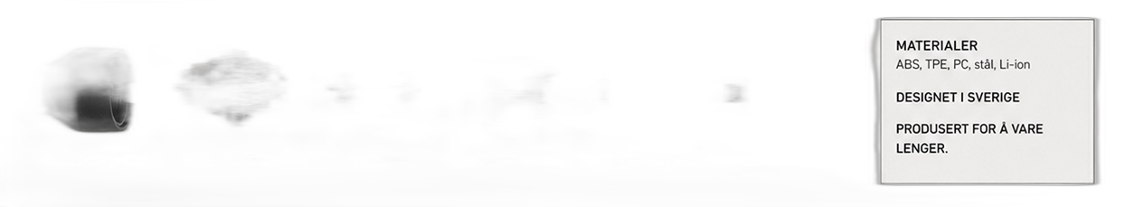
assets/finished_graphics/skisser/image_3.png
