lukketsvane/GK4_TRIXIG/assets/finished_graphics/skisser/utvalgt_04_skisse_094_serviceport_innmat_1.png

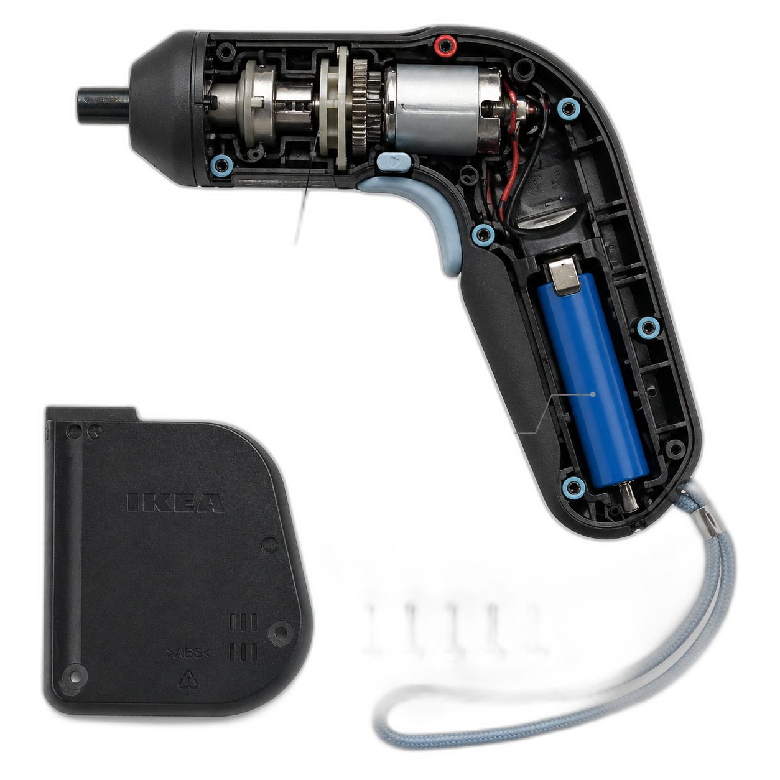
assets/finished_graphics/skisser/utvalgt_04_skisse_094_serviceport_innmat_1.png
