lukketsvane/GK4_TRIXIG/assets/finished_graphics/skisser/utvalgt_05_skisse_096_eksplodert_teardown_1.png

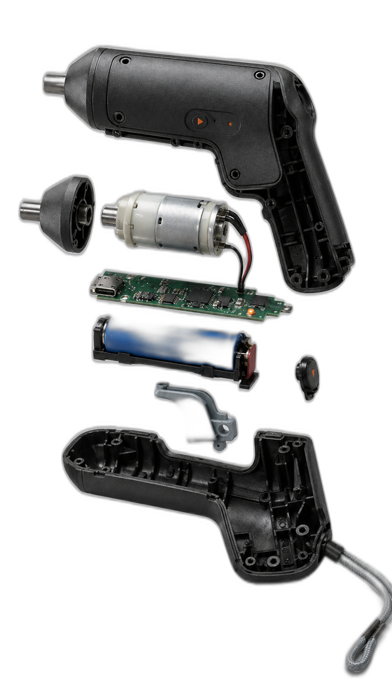
assets/finished_graphics/skisser/utvalgt_05_skisse_096_eksplodert_teardown_1.png
