lukketsvane/GK4_TRIXIG/assets/finished_graphics/teardown/trixig_demontert.jpeg

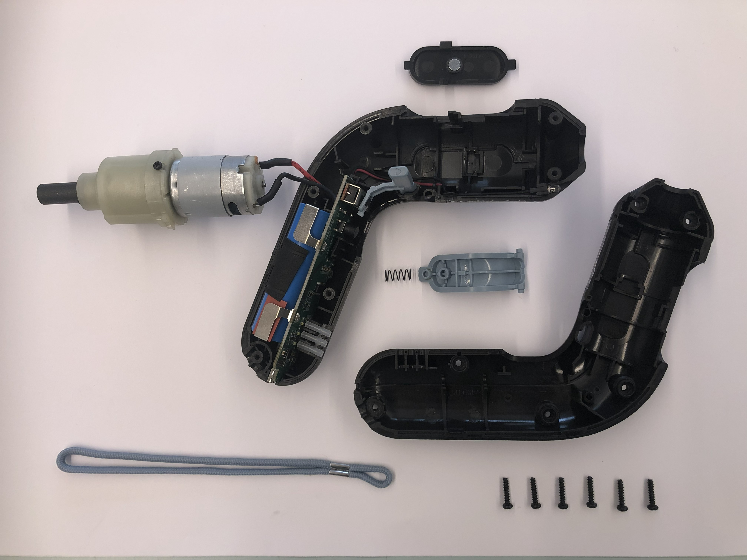
assets/finished_graphics/teardown/trixig_demontert.jpeg
