lukketsvane/GK4_TRIXIG/assets/finished_graphics/teardown/trixig_demontert_perspektiv.jpeg

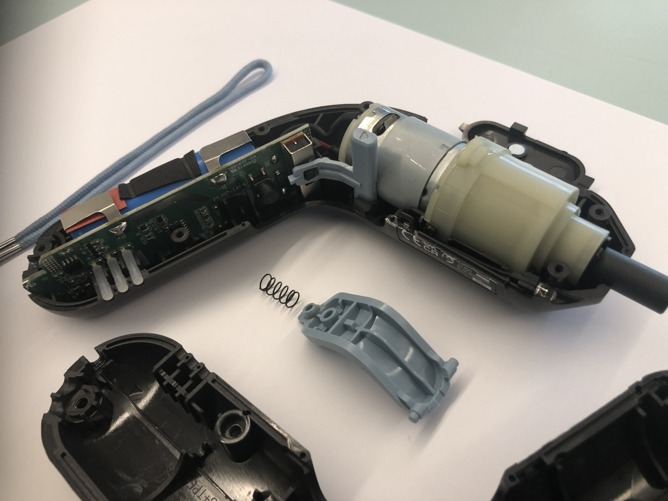
assets/finished_graphics/teardown/trixig_demontert_perspektiv.jpeg
