lukketsvane/GK4_TRIXIG/assets/generated/gen_26_05/01_reference_renders/trixig_260526_u005_black-top-button.png

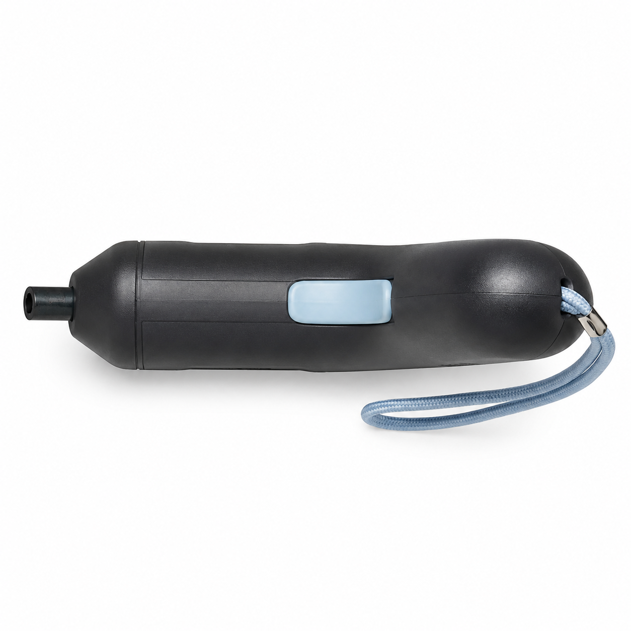
assets/generated/gen_26_05/01_reference_renders/trixig_260526_u005_black-top-button.png
