lukketsvane/GK4_TRIXIG/assets/generated/gen_26_05/01_reference_renders/trixig_260526_u013_black-front-control.png

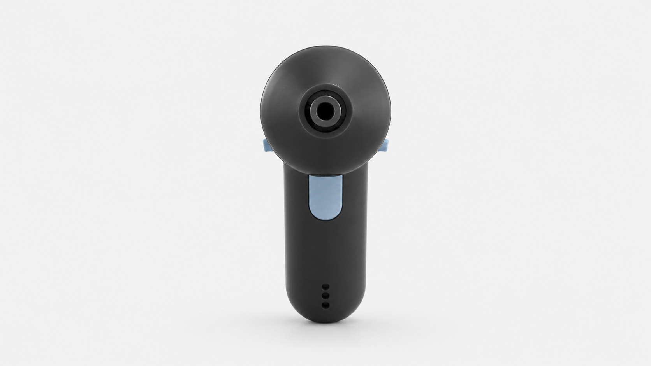
assets/generated/gen_26_05/01_reference_renders/trixig_260526_u013_black-front-control.png
