lukketsvane/GK4_TRIXIG/assets/generated/gen_26_05/02_mechanics_cutaways/trixig_260526_u008_black-cutaway-side.png

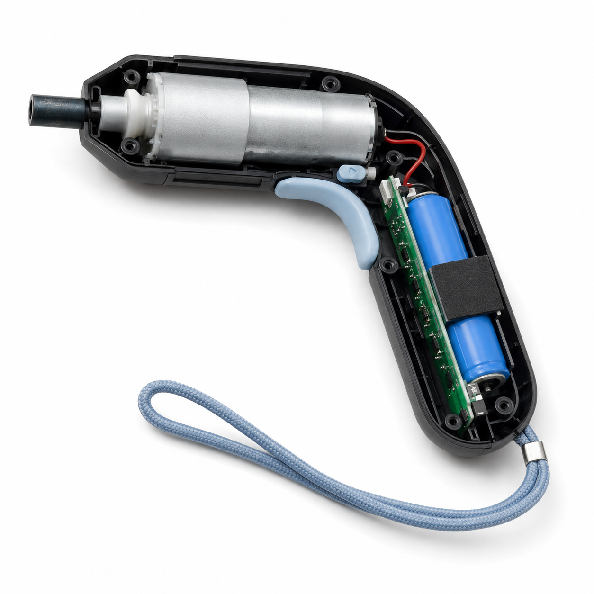
assets/generated/gen_26_05/02_mechanics_cutaways/trixig_260526_u008_black-cutaway-side.png
