lukketsvane/GK4_TRIXIG/assets/generated/gen_26_05/02_mechanics_cutaways/trixig_260526_u016_black-cutaway-battery.png

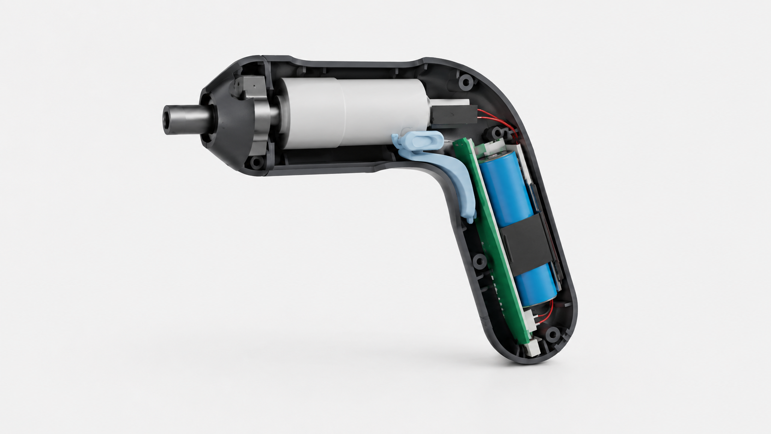
assets/generated/gen_26_05/02_mechanics_cutaways/trixig_260526_u016_black-cutaway-battery.png
