lukketsvane/GK4_TRIXIG/assets/generated/gen_26_05/02_mechanics_cutaways/trixig_260526_u018_motor-battery-module.png

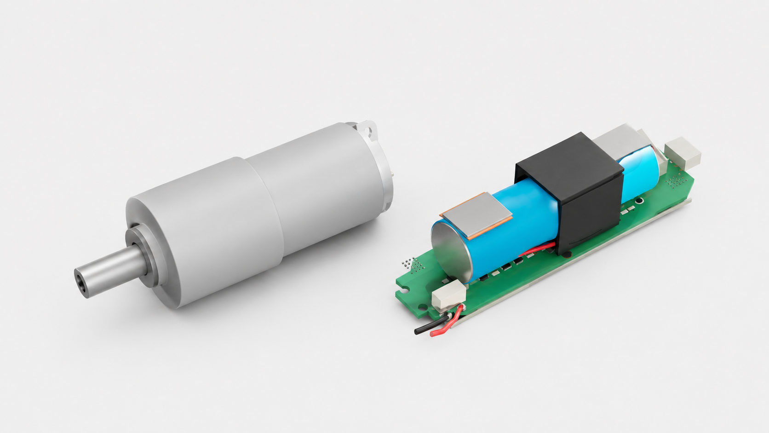
assets/generated/gen_26_05/02_mechanics_cutaways/trixig_260526_u018_motor-battery-module.png
