lukketsvane/GK4_TRIXIG/assets/generated/gen_26_05/02_mechanics_cutaways/trixig_260526_u023_white-side-pack-a.png

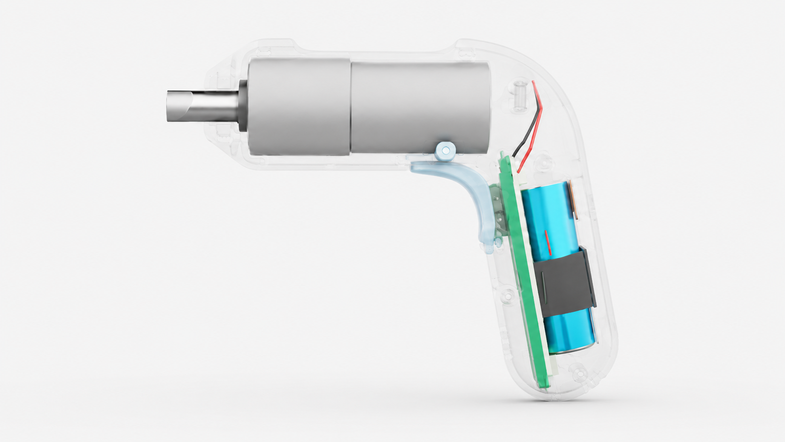
assets/generated/gen_26_05/02_mechanics_cutaways/trixig_260526_u023_white-side-pack-a.png
