lukketsvane/GK4_TRIXIG/assets/generated/gen_26_05/02_mechanics_cutaways/trixig_260526_u029_white-side-flat.png

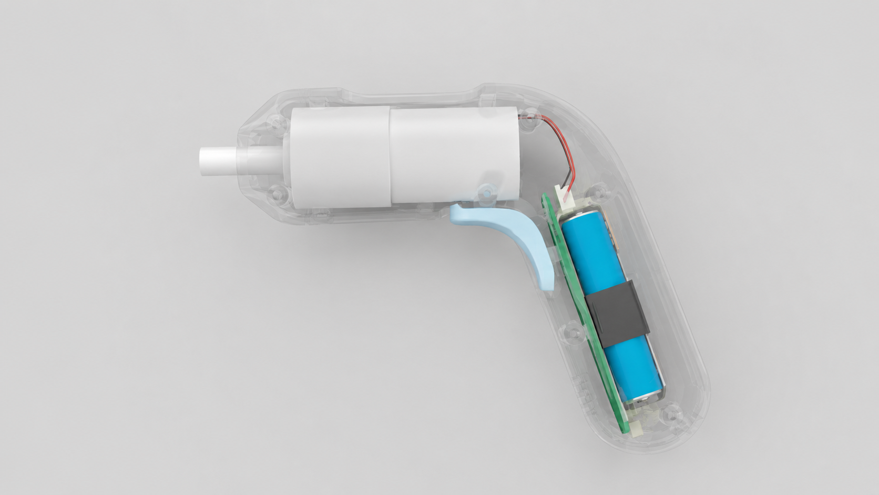
assets/generated/gen_26_05/02_mechanics_cutaways/trixig_260526_u029_white-side-flat.png
