lukketsvane/GK4_TRIXIG/assets/generated/gen_26_05/03_process_boards/trixig_260526_u043_tjalve-form-grid.png

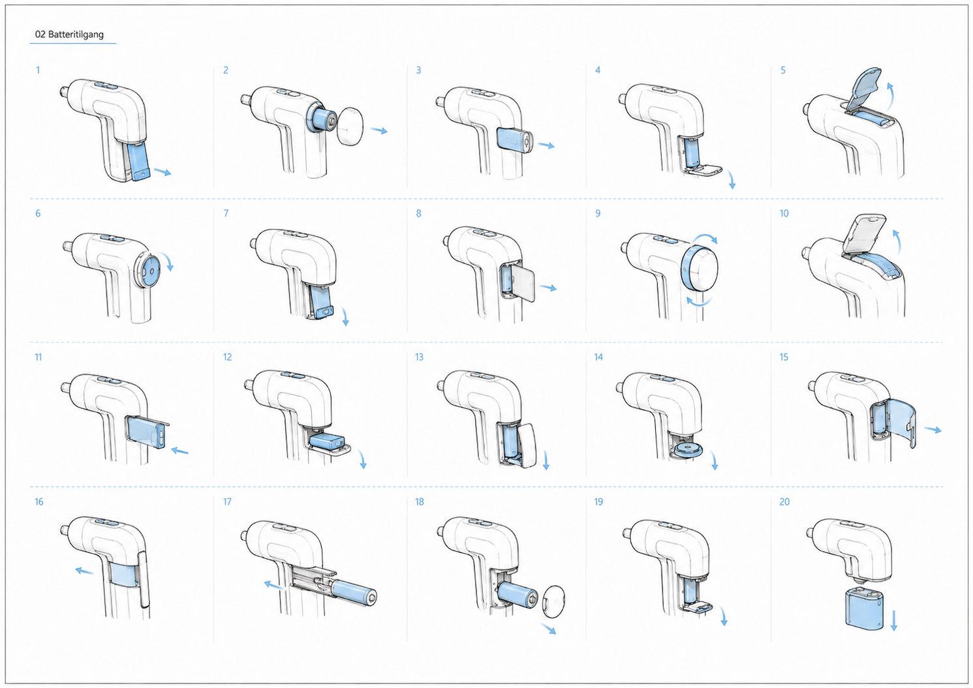
assets/generated/gen_26_05/03_process_boards/trixig_260526_u043_tjalve-form-grid.png
