lukketsvane/GK4_TRIXIG/assets/generated/gen_26_05/03_process_boards/trixig_260526_u063_search-criteria-panels.png

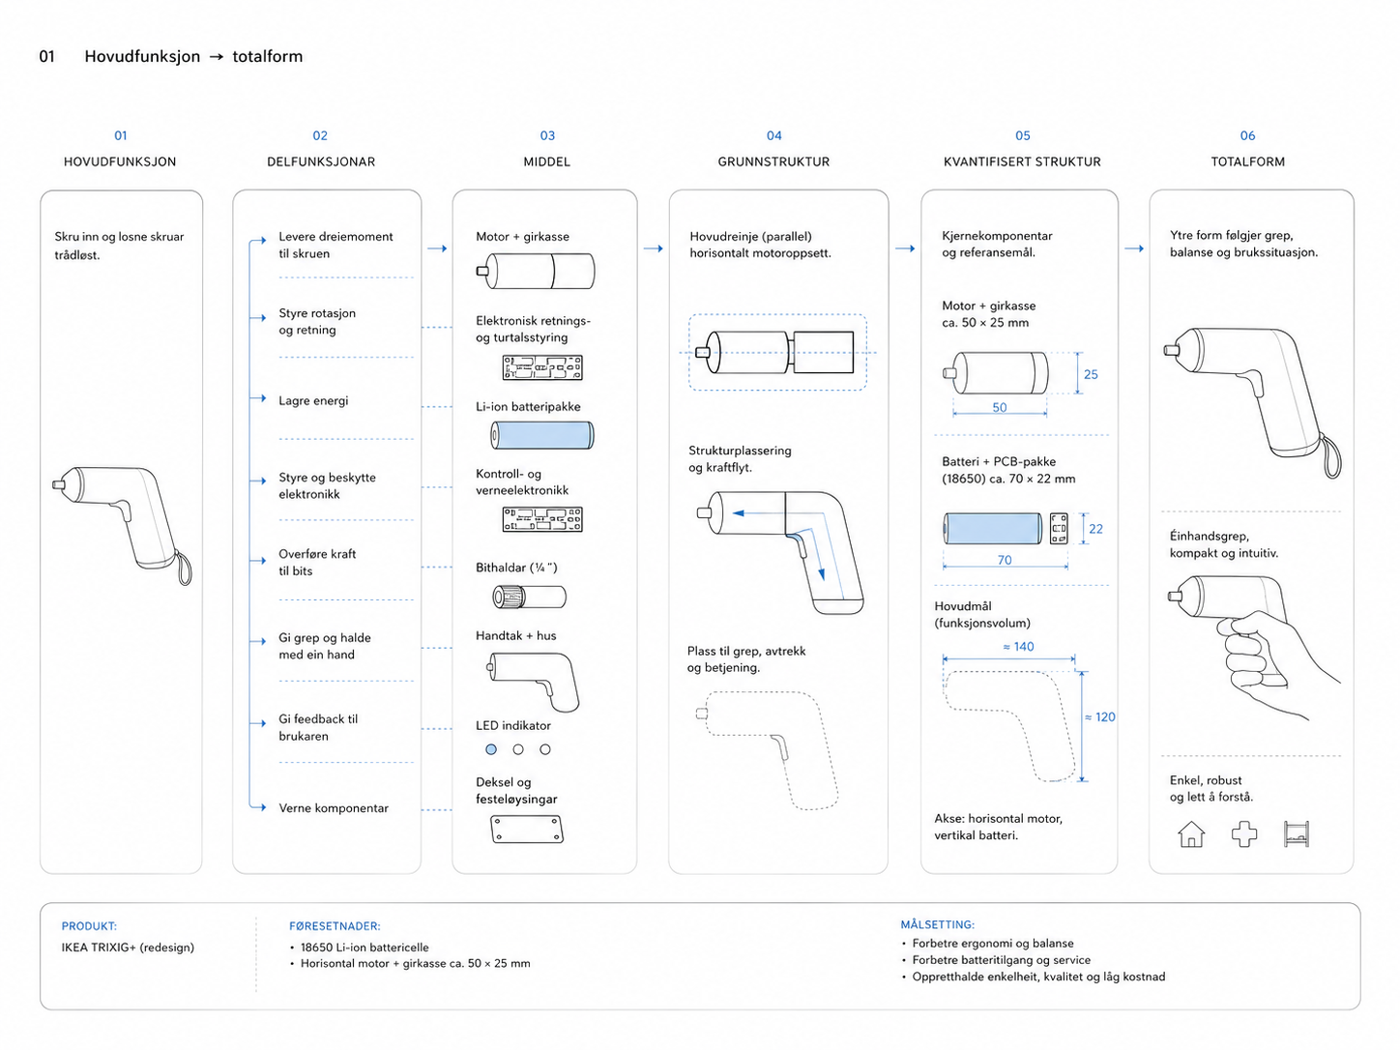
assets/generated/gen_26_05/03_process_boards/trixig_260526_u063_search-criteria-panels.png
