lukketsvane/GK4_TRIXIG/assets/generated/gen_26_05/03_process_boards/trixig_260526_u076_tre-hovudelement-detail.png

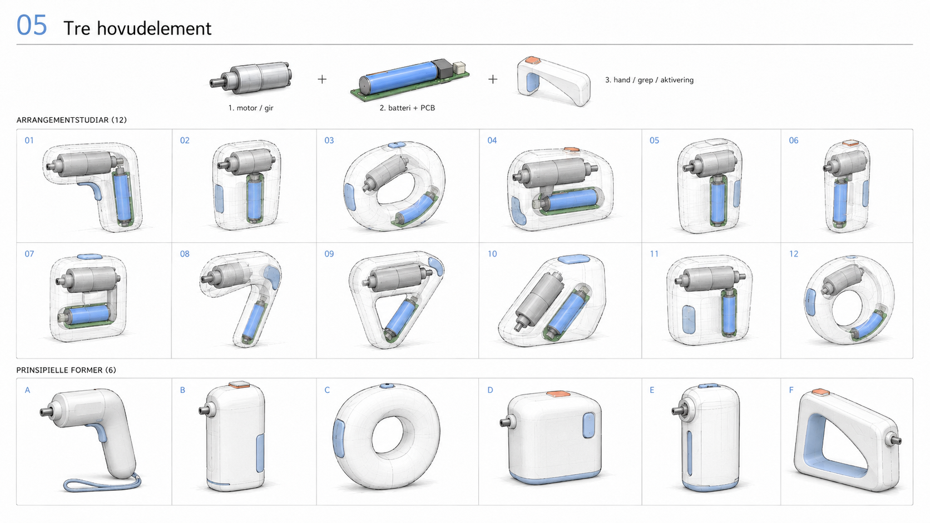
assets/generated/gen_26_05/03_process_boards/trixig_260526_u076_tre-hovudelement-detail.png
