lukketsvane/GK4_TRIXIG/assets/generated/gen_26_05/04_decision_boards/trixig_260526_u060_tre-hovudelement.png

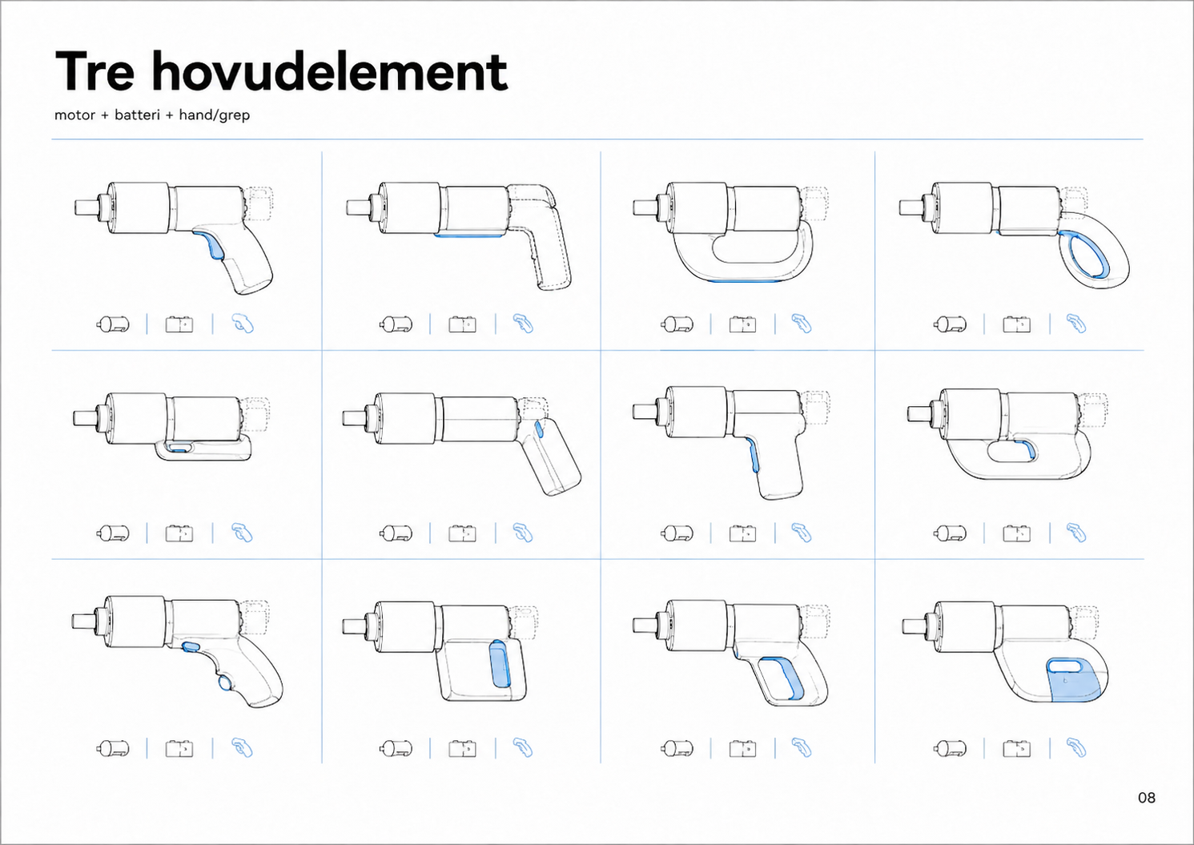
assets/generated/gen_26_05/04_decision_boards/trixig_260526_u060_tre-hovudelement.png
