lukketsvane/GK4_TRIXIG/assets/generated/gen_26_05/04_decision_boards/trixig_260526_u088_section-comparison.png

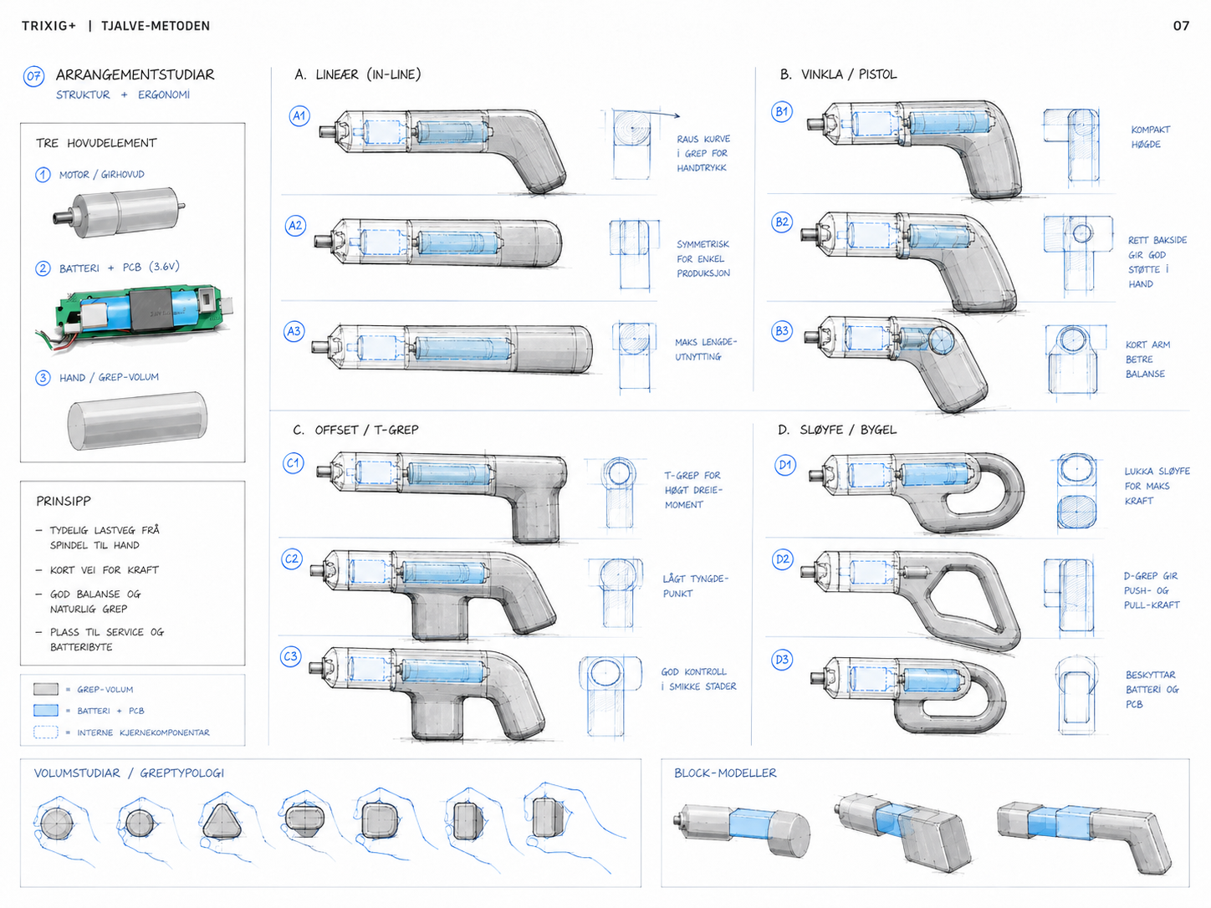
assets/generated/gen_26_05/04_decision_boards/trixig_260526_u088_section-comparison.png
