lukketsvane/GK4_TRIXIG/assets/generated/gen_26_05/04_decision_boards/trixig_260526_u095_grunnstruktur-options.png

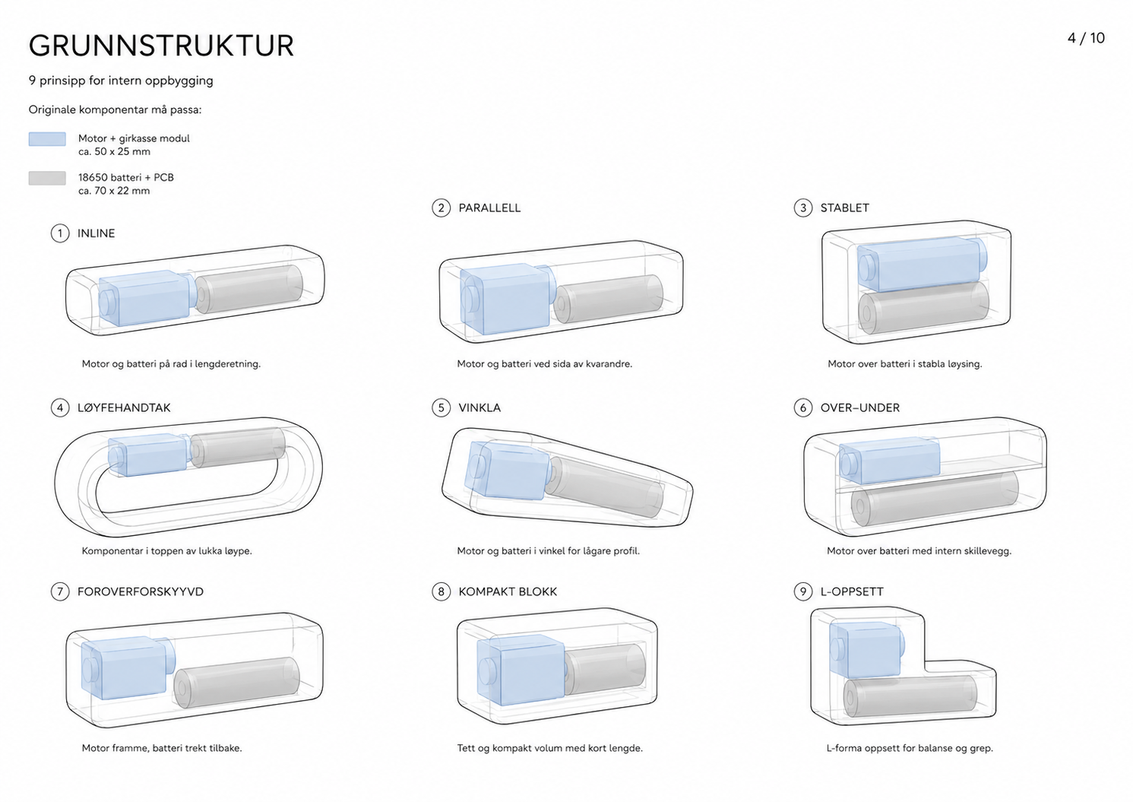
assets/generated/gen_26_05/04_decision_boards/trixig_260526_u095_grunnstruktur-options.png
