lukketsvane/GK4_TRIXIG/assets/generated/gen_26_05/05_concept_presentations/trixig_260526_u102_concept-01-slim-hook.png

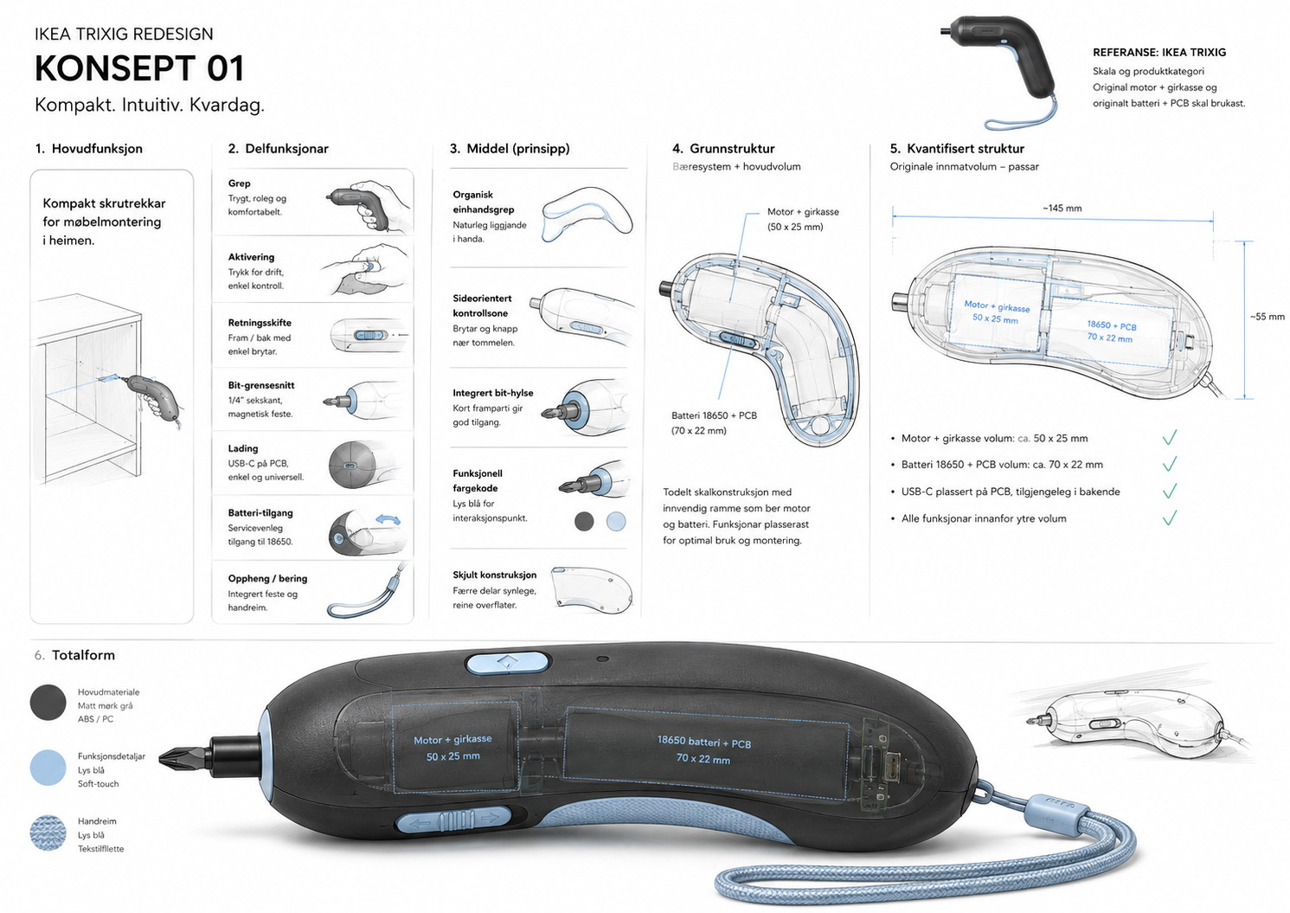
assets/generated/gen_26_05/05_concept_presentations/trixig_260526_u102_concept-01-slim-hook.png
