lukketsvane/GK4_TRIXIG/assets/generated/gen_26_05/05_concept_presentations/trixig_260526_u103_concept-02-soft-pistol.png

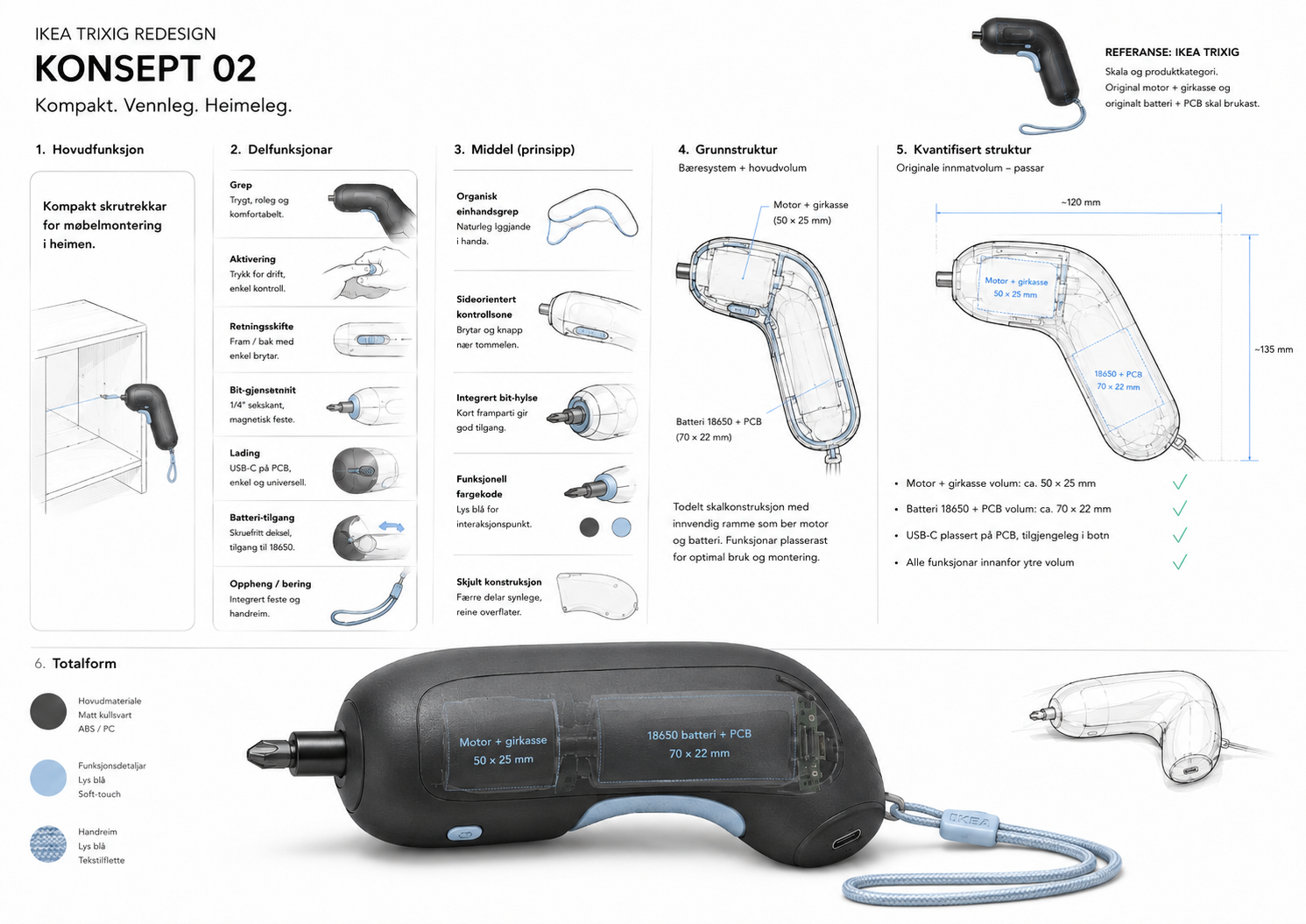
assets/generated/gen_26_05/05_concept_presentations/trixig_260526_u103_concept-02-soft-pistol.png
