lukketsvane/GK4_TRIXIG/assets/generated/gen_26_05/05_concept_presentations/trixig_260526_u104_concept-03-capsule-bar.png

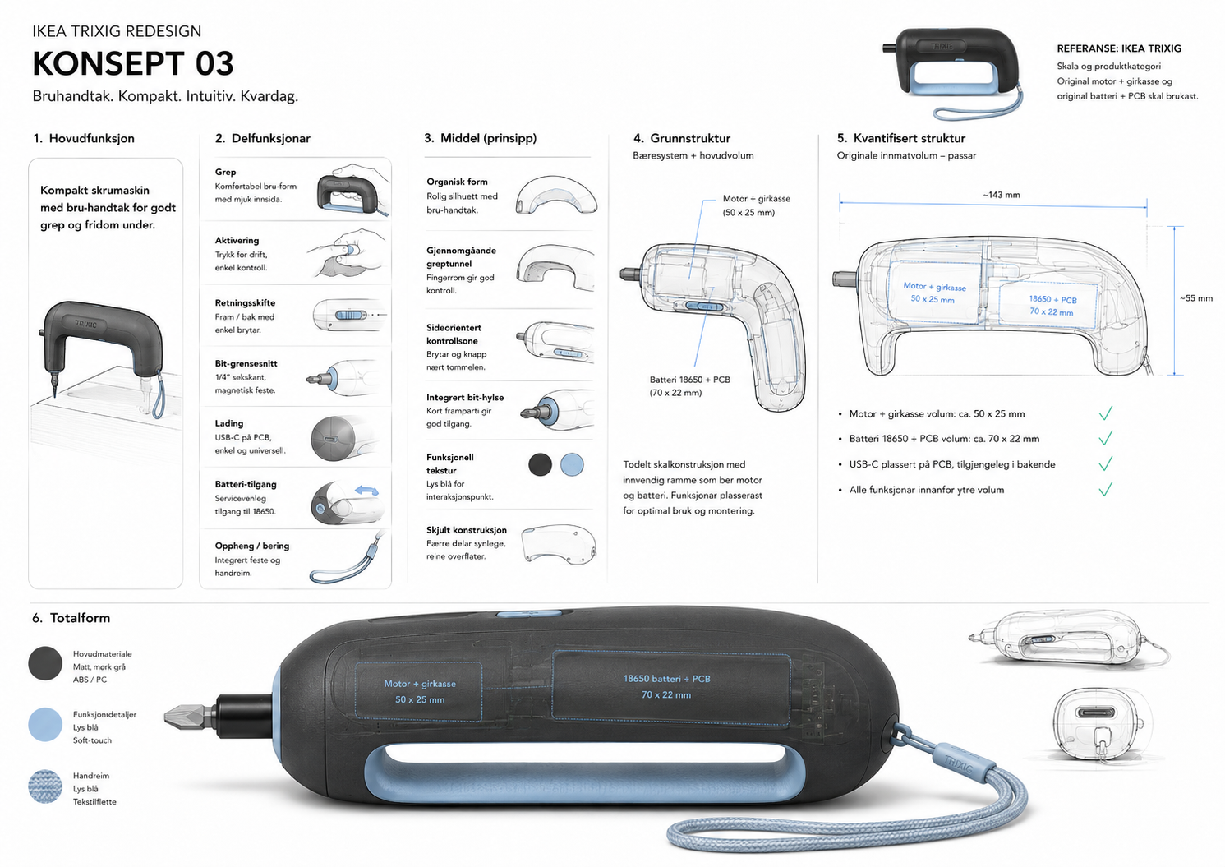
assets/generated/gen_26_05/05_concept_presentations/trixig_260526_u104_concept-03-capsule-bar.png
