lukketsvane/GK4_TRIXIG/assets/generated/gen_26_05/05_concept_presentations/trixig_260526_u106_concept-05-arc-grip.png

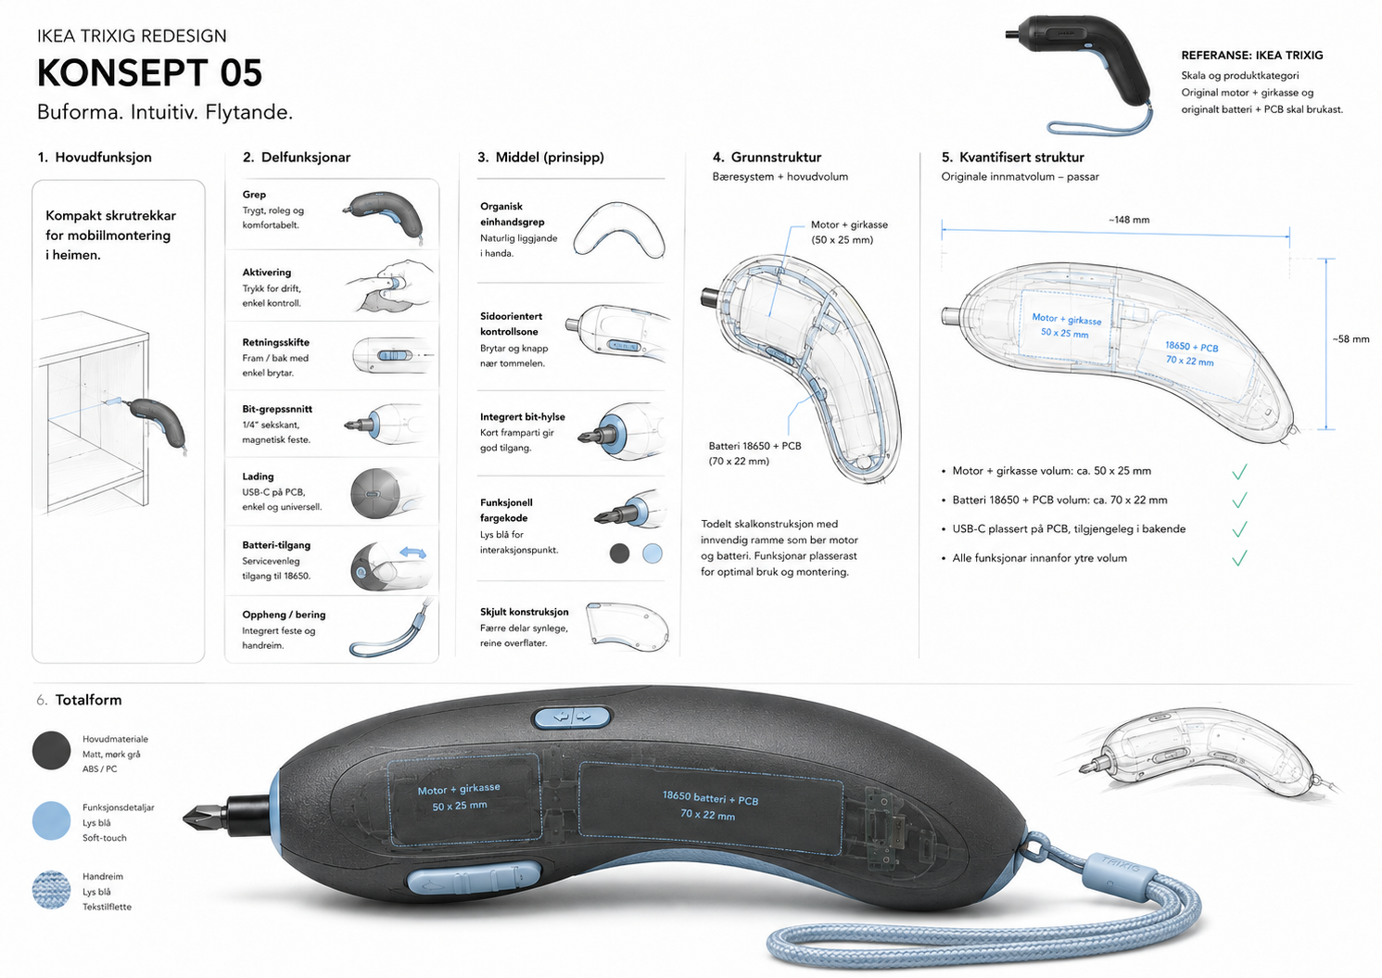
assets/generated/gen_26_05/05_concept_presentations/trixig_260526_u106_concept-05-arc-grip.png
