lukketsvane/GK4_TRIXIG/assets/generated/gen_26_05/05_concept_presentations/trixig_260526_u107_concept-06-ring-tail.png

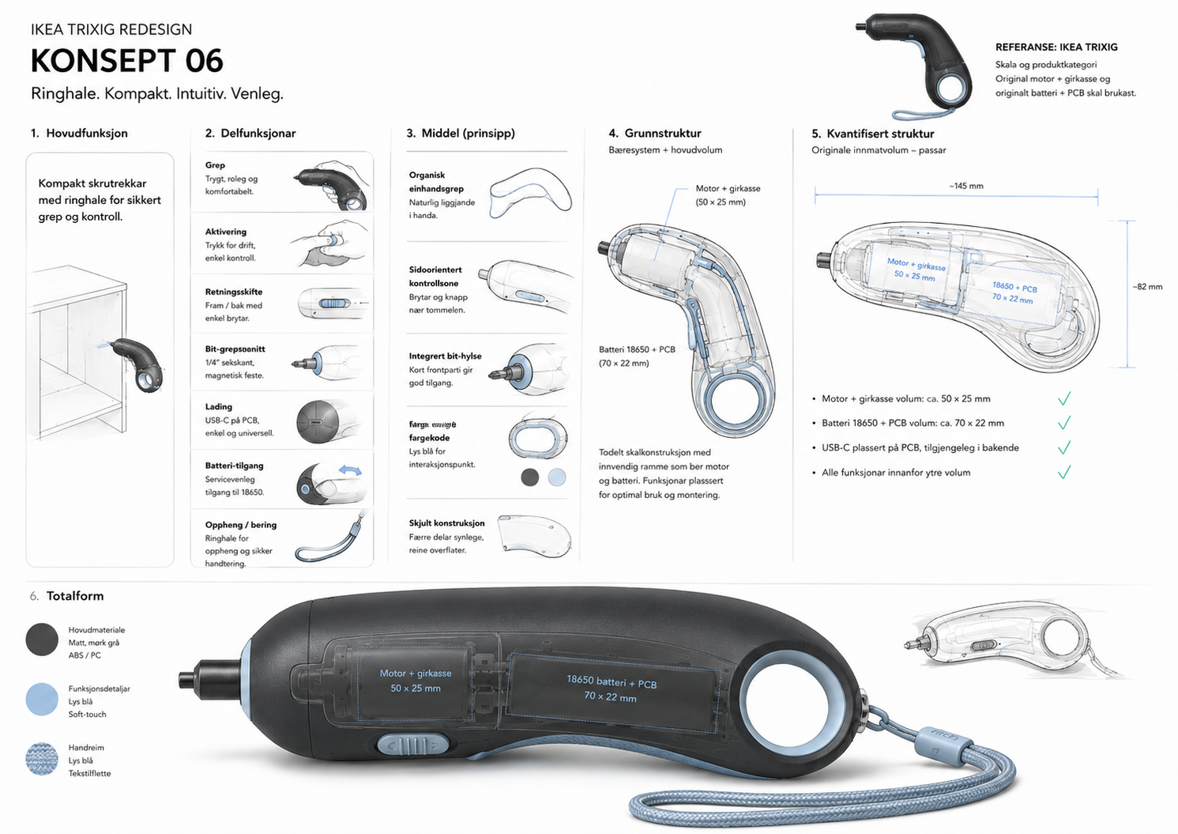
assets/generated/gen_26_05/05_concept_presentations/trixig_260526_u107_concept-06-ring-tail.png
