lukketsvane/GK4_TRIXIG/assets/generated/gen_26_05/05_concept_presentations/trixig_260526_u108_concept-07-flat-rail.png

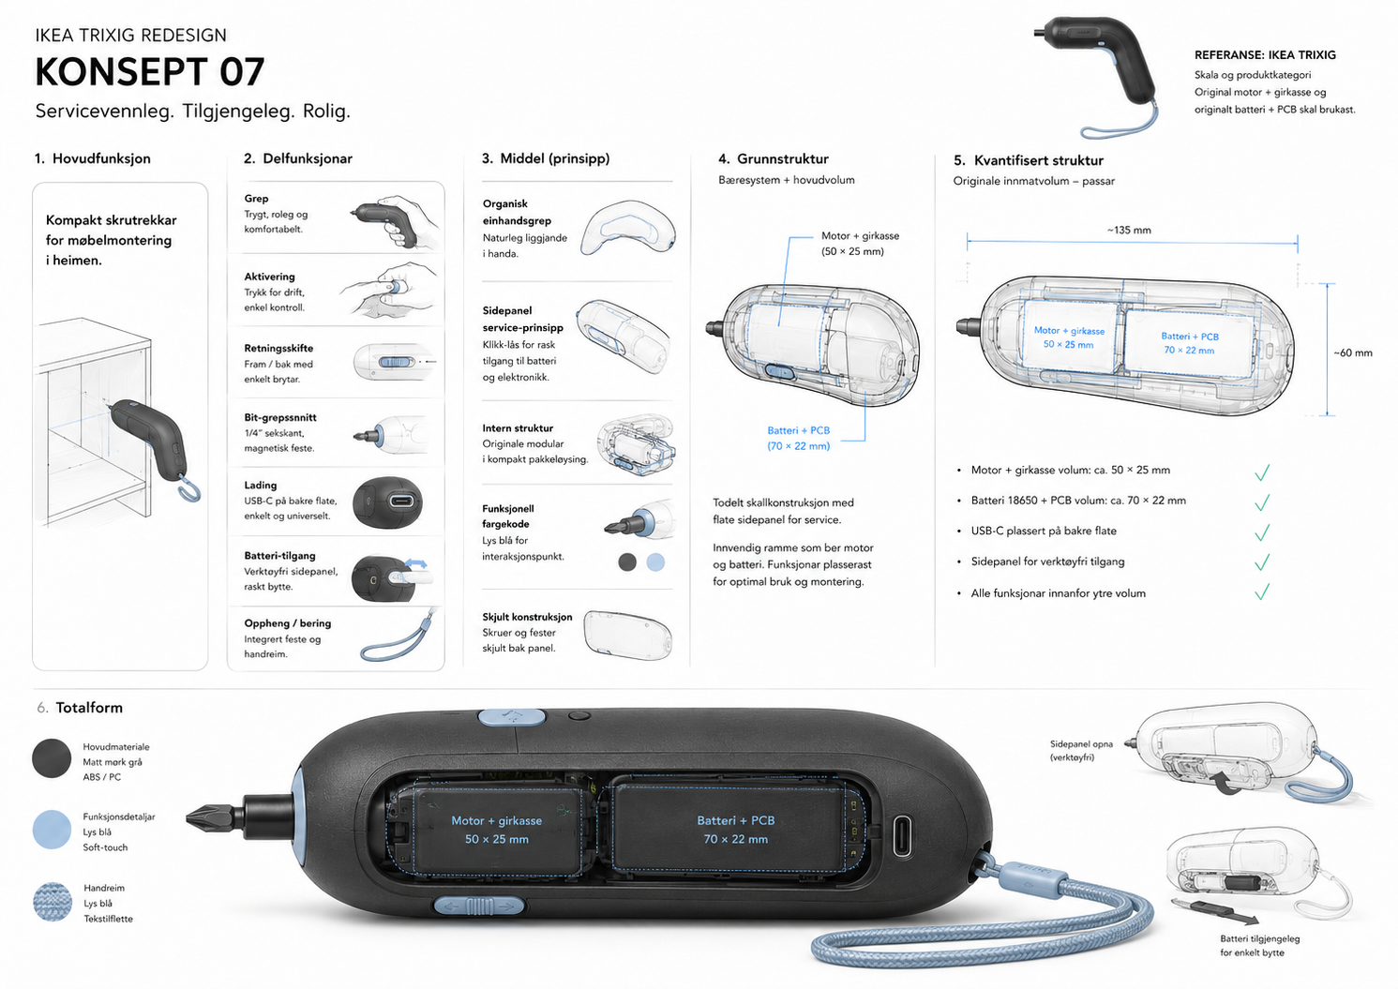
assets/generated/gen_26_05/05_concept_presentations/trixig_260526_u108_concept-07-flat-rail.png
