lukketsvane/GK4_TRIXIG/assets/generated/gen_26_05/05_concept_presentations/trixig_260526_u109_concept-08-loop-handle.png

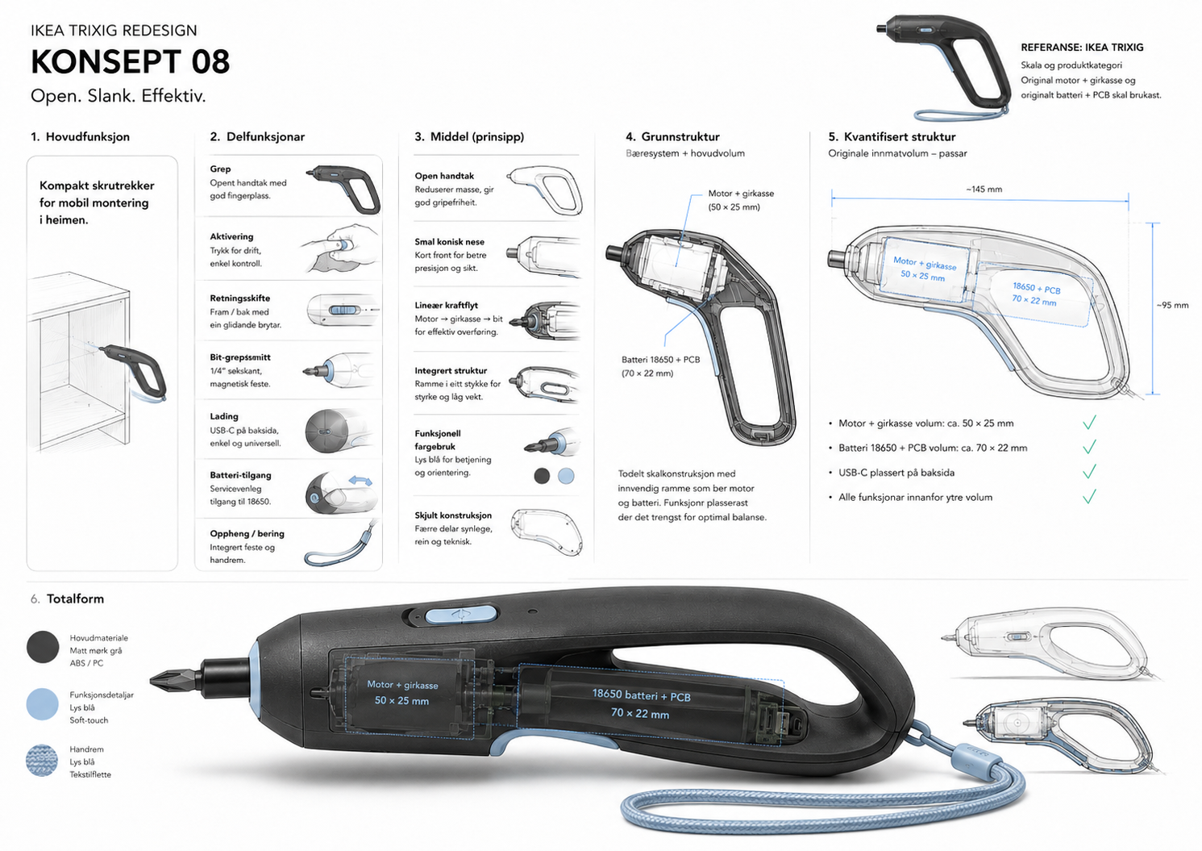
assets/generated/gen_26_05/05_concept_presentations/trixig_260526_u109_concept-08-loop-handle.png
