lukketsvane/GK4_TRIXIG/assets/generated/gen_26_05/05_concept_presentations/trixig_260526_u110_concept-09-soft-arc.png

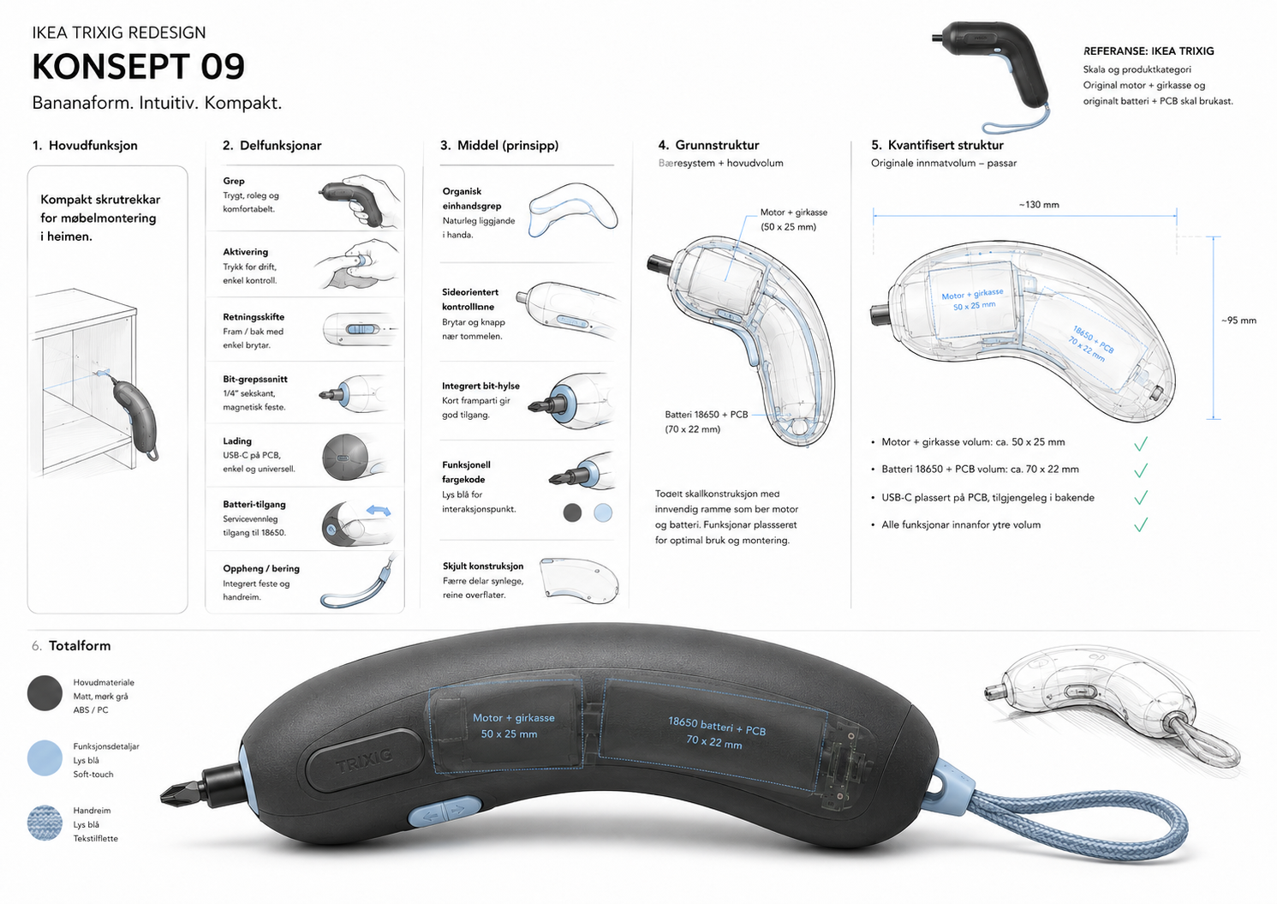
assets/generated/gen_26_05/05_concept_presentations/trixig_260526_u110_concept-09-soft-arc.png
