lukketsvane/GK4_TRIXIG/assets/generated/gen_26_05/05_concept_presentations/trixig_260526_u111_concept-10-compact-oval.png

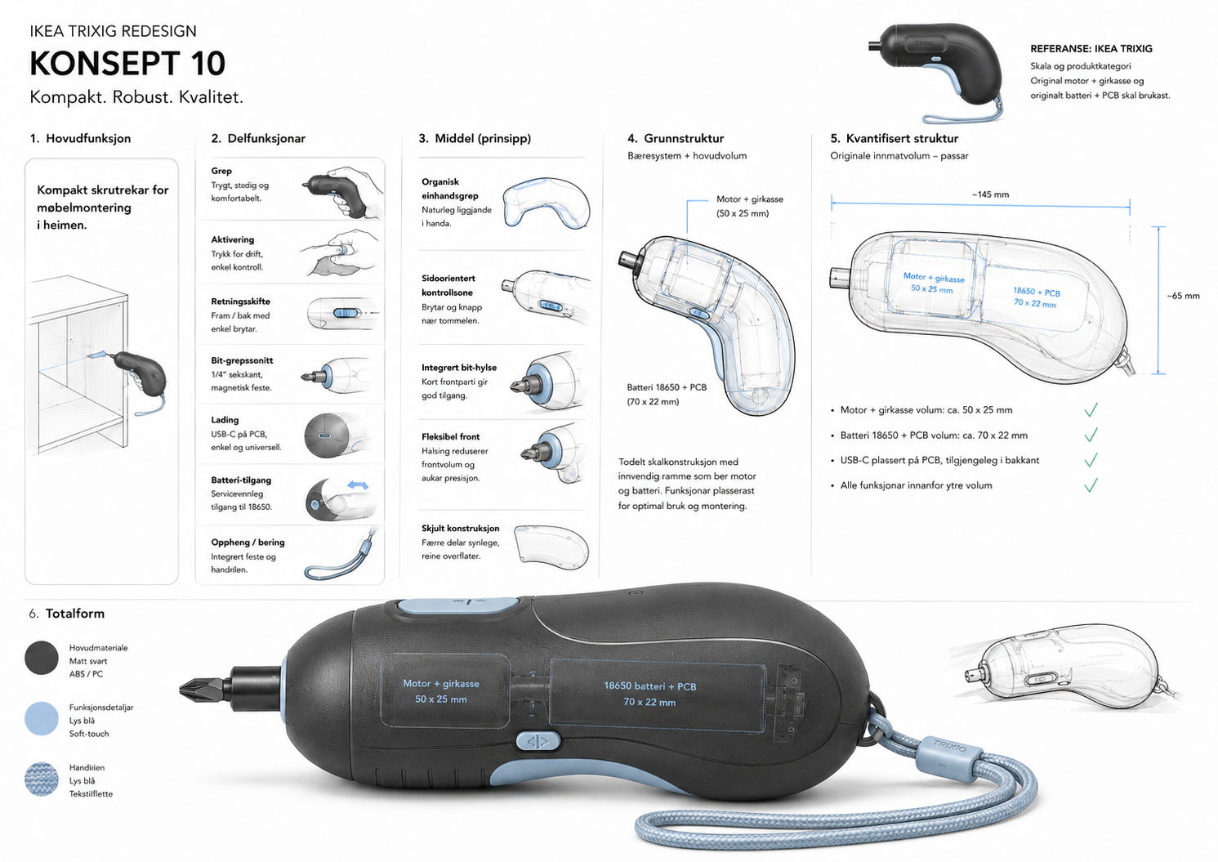
assets/generated/gen_26_05/05_concept_presentations/trixig_260526_u111_concept-10-compact-oval.png
