lukketsvane/GK4_TRIXIG/assets/generated/gen_26_05/05_concept_presentations/trixig_260526_u238_loop-body-pair-board.png

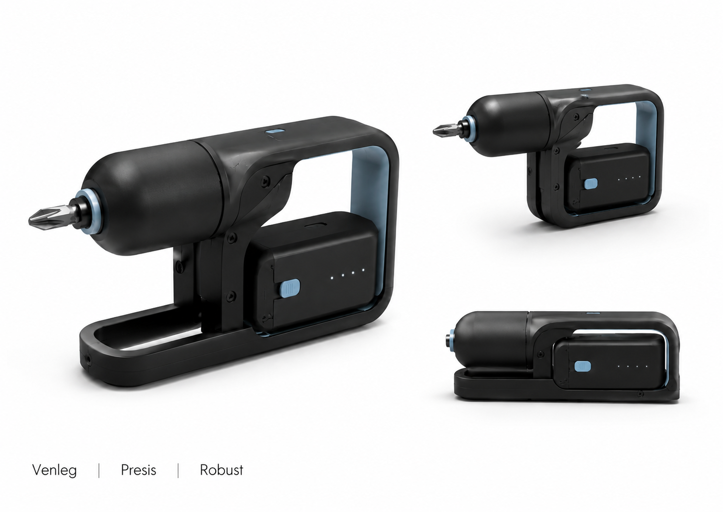
assets/generated/gen_26_05/05_concept_presentations/trixig_260526_u238_loop-body-pair-board.png
