lukketsvane/GK4_TRIXIG/assets/generated/gen_26_05/06_ideation_grids/trixig_260526_u115_pistol-capsule-grid.png

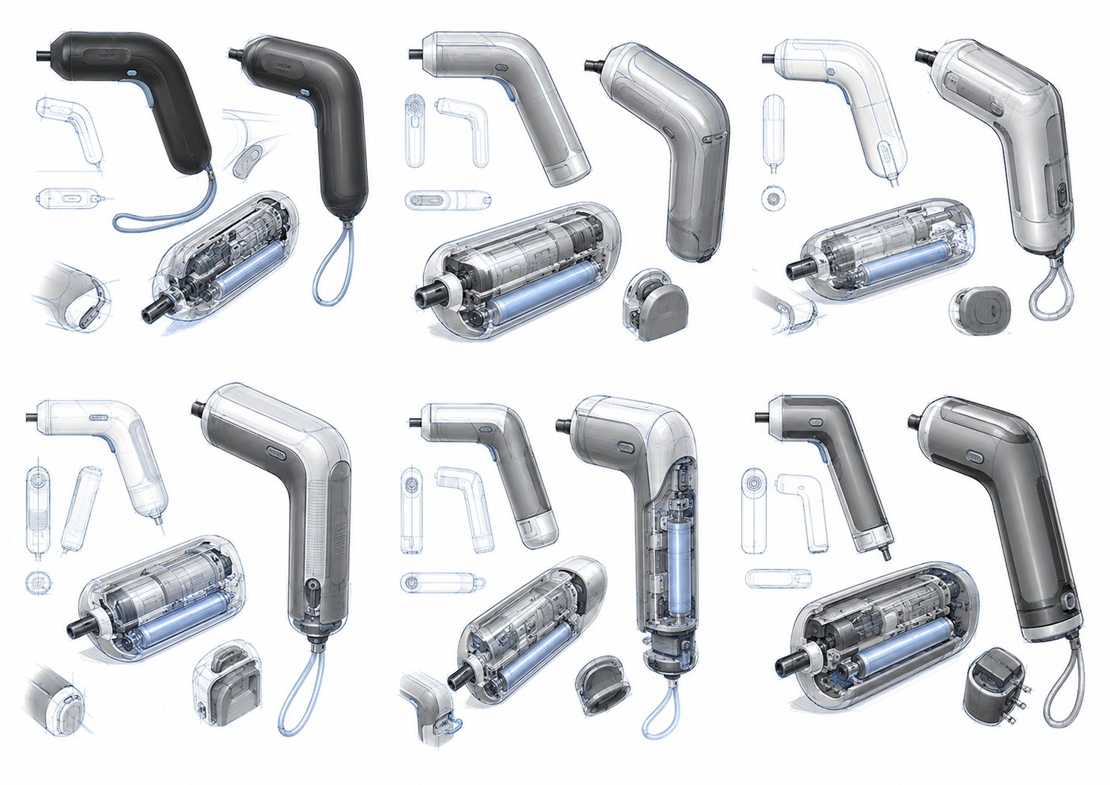
assets/generated/gen_26_05/06_ideation_grids/trixig_260526_u115_pistol-capsule-grid.png
