lukketsvane/GK4_TRIXIG/assets/generated/gen_26_05/06_ideation_grids/trixig_260526_u117_inline-exploded-overview.png

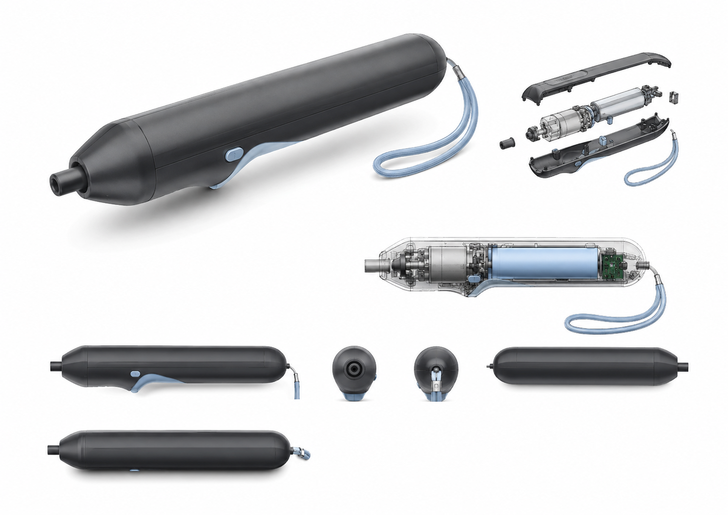
assets/generated/gen_26_05/06_ideation_grids/trixig_260526_u117_inline-exploded-overview.png
