lukketsvane/GK4_TRIXIG/assets/generated/gen_26_05/06_ideation_grids/trixig_260526_u152_faceted-capsule-set.png

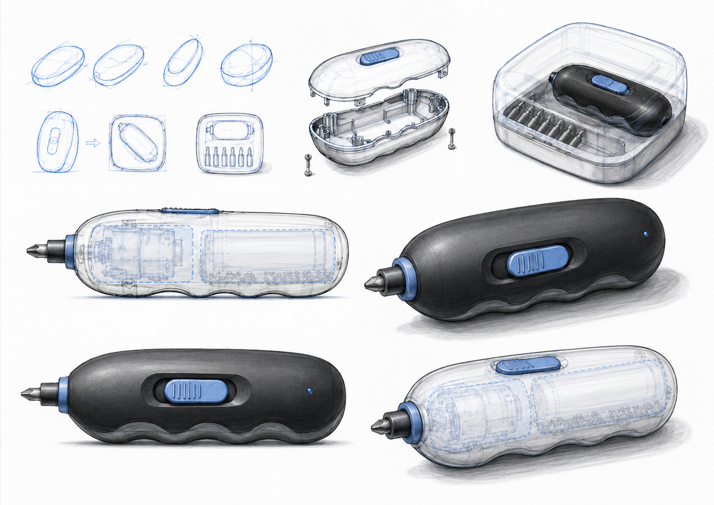
assets/generated/gen_26_05/06_ideation_grids/trixig_260526_u152_faceted-capsule-set.png
