lukketsvane/GK4_TRIXIG/assets/generated/gen_26_05/06_ideation_grids/trixig_260526_u159_capsule-ideation-board.png

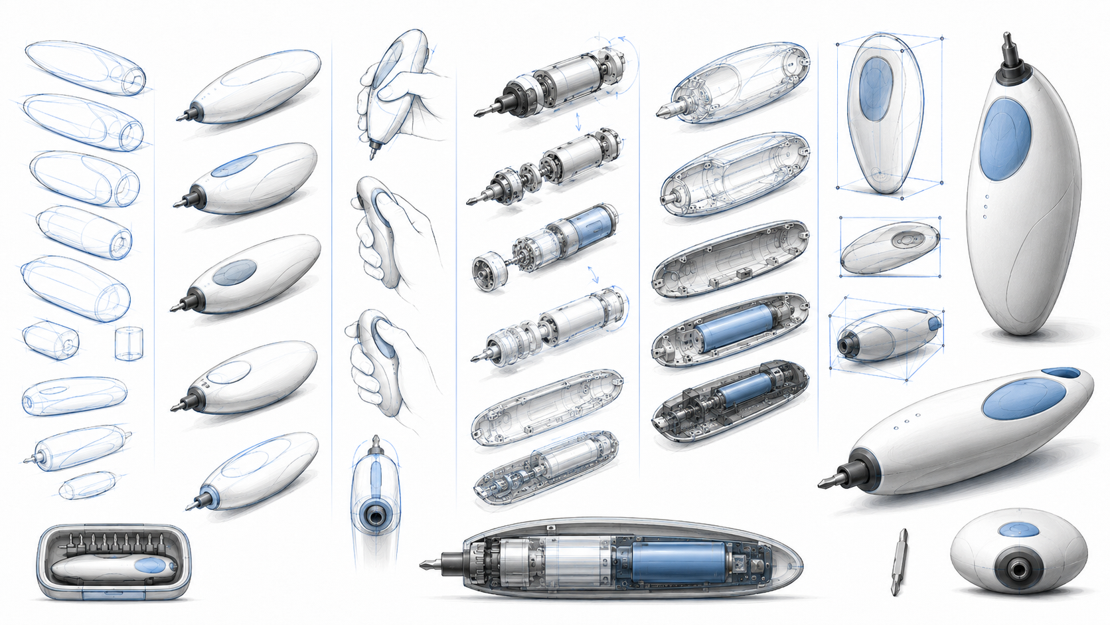
assets/generated/gen_26_05/06_ideation_grids/trixig_260526_u159_capsule-ideation-board.png
