lukketsvane/GK4_TRIXIG/assets/generated/gen_26_05/07_variant_renders_light/trixig_260526_u177_folding-hinge-two-render.png

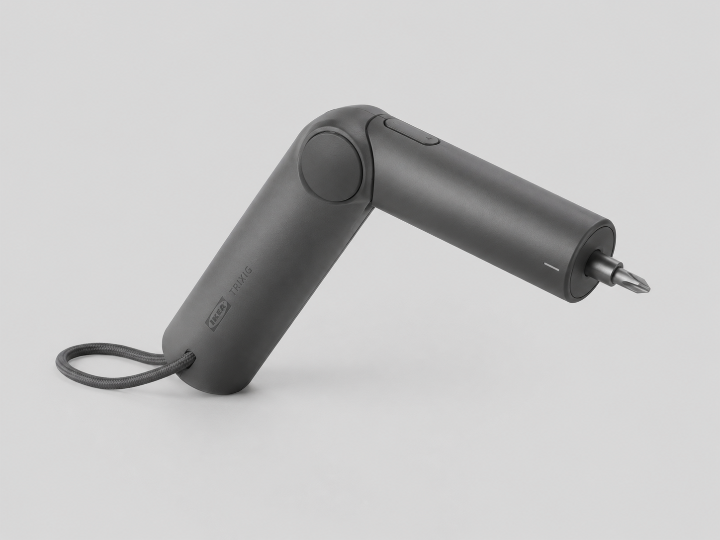
assets/generated/gen_26_05/07_variant_renders_light/trixig_260526_u177_folding-hinge-two-render.png
