lukketsvane/GK4_TRIXIG/assets/generated/gen_26_05/07_variant_renders_light/trixig_260526_u180_vertical-loop-grip.png

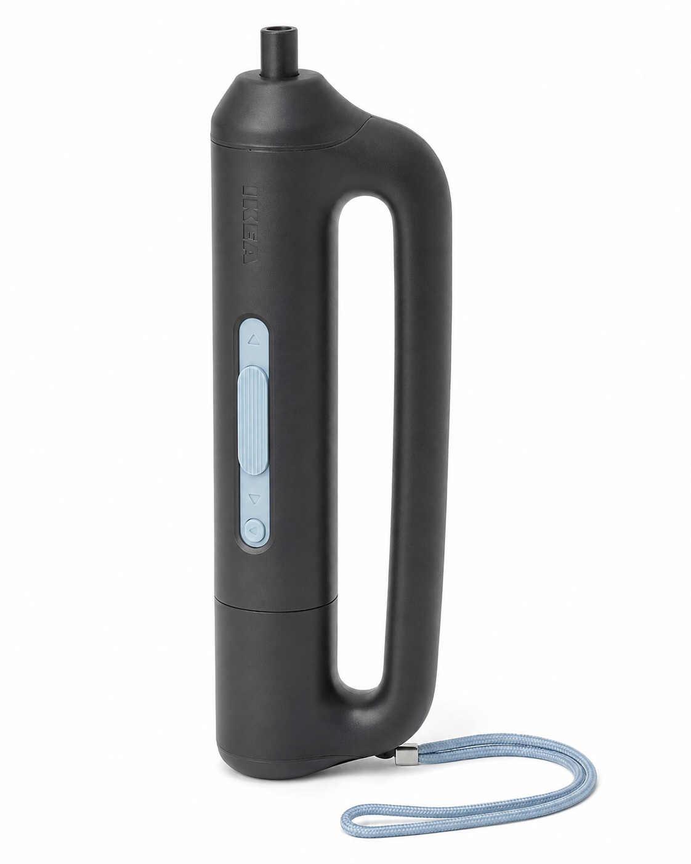
assets/generated/gen_26_05/07_variant_renders_light/trixig_260526_u180_vertical-loop-grip.png
