lukketsvane/GK4_TRIXIG/assets/generated/gen_26_05/07_variant_renders_light/trixig_260526_u205_angled-inline-hinge.png

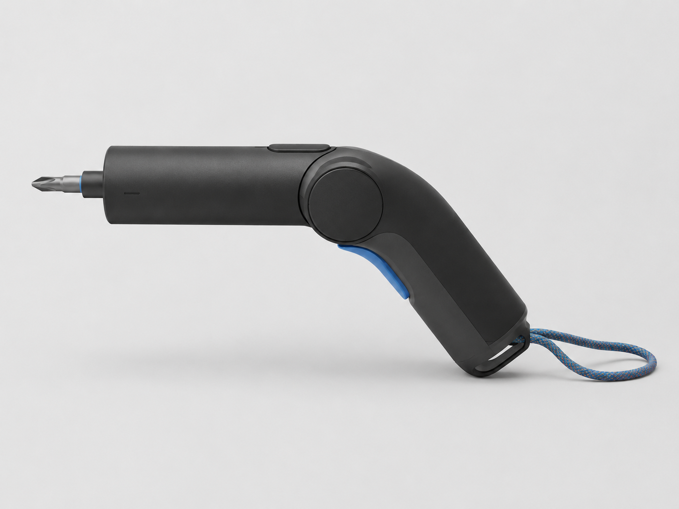
assets/generated/gen_26_05/07_variant_renders_light/trixig_260526_u205_angled-inline-hinge.png
