lukketsvane/GK4_TRIXIG/assets/generated/gen_26_05/07_variant_renders_light/trixig_260526_u211_blue-battery-stick.png

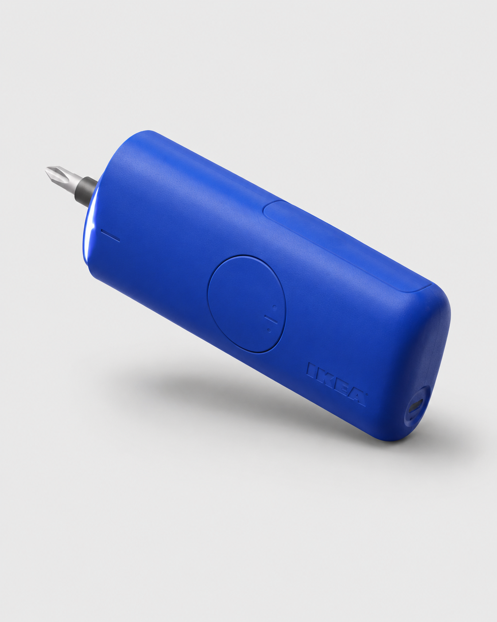
assets/generated/gen_26_05/07_variant_renders_light/trixig_260526_u211_blue-battery-stick.png
