lukketsvane/GK4_TRIXIG/assets/generated/gen_26_05/07_variant_renders_light/trixig_260526_u213_folded-baton-side.png

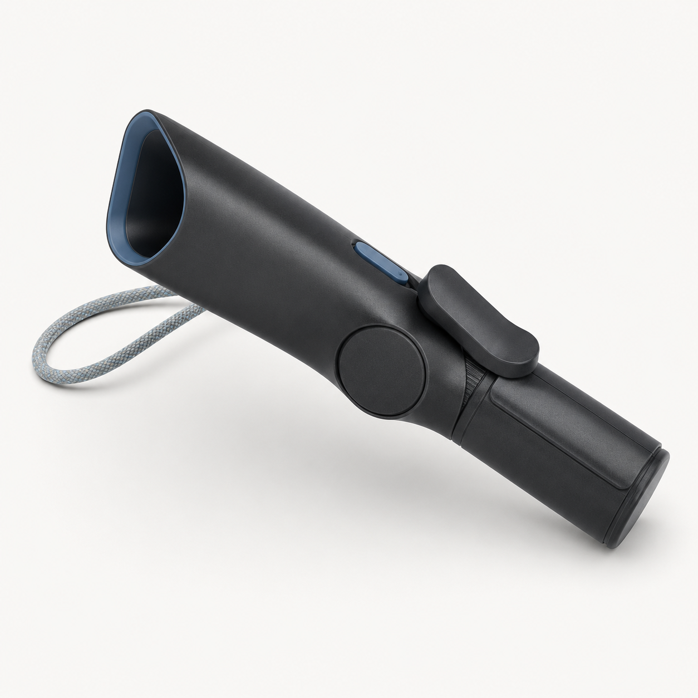
assets/generated/gen_26_05/07_variant_renders_light/trixig_260526_u213_folded-baton-side.png
