lukketsvane/GK4_TRIXIG/assets/generated/gen_26_05/08_variant_renders_dark/trixig_260526_u220_dark-boxy-side.png

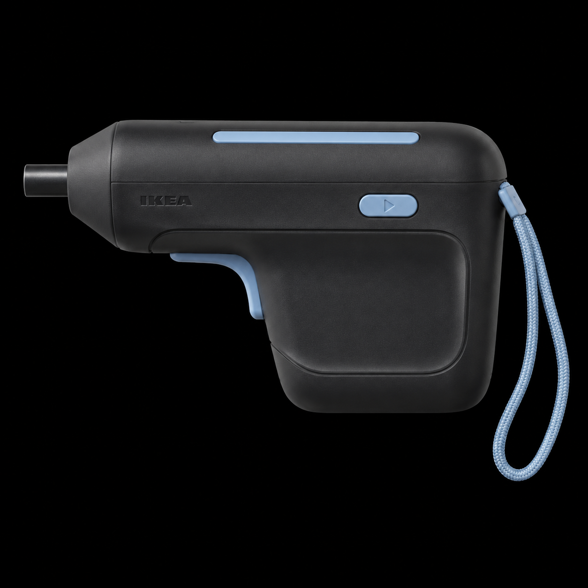
assets/generated/gen_26_05/08_variant_renders_dark/trixig_260526_u220_dark-boxy-side.png
