lukketsvane/GK4_TRIXIG/assets/generated/gen_26_05/08_variant_renders_dark/trixig_260526_u221_dark-boxy-pistol-a.png

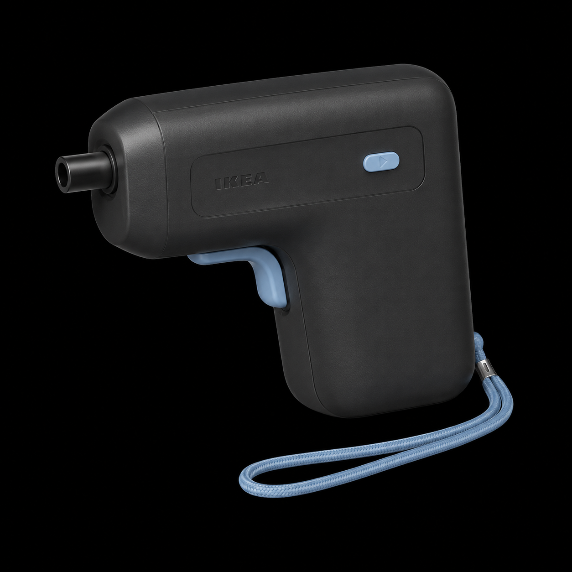
assets/generated/gen_26_05/08_variant_renders_dark/trixig_260526_u221_dark-boxy-pistol-a.png
