lukketsvane/GK4_TRIXIG/assets/generated/gen_26_05/08_variant_renders_dark/trixig_260526_u224_dark-tall-body.png

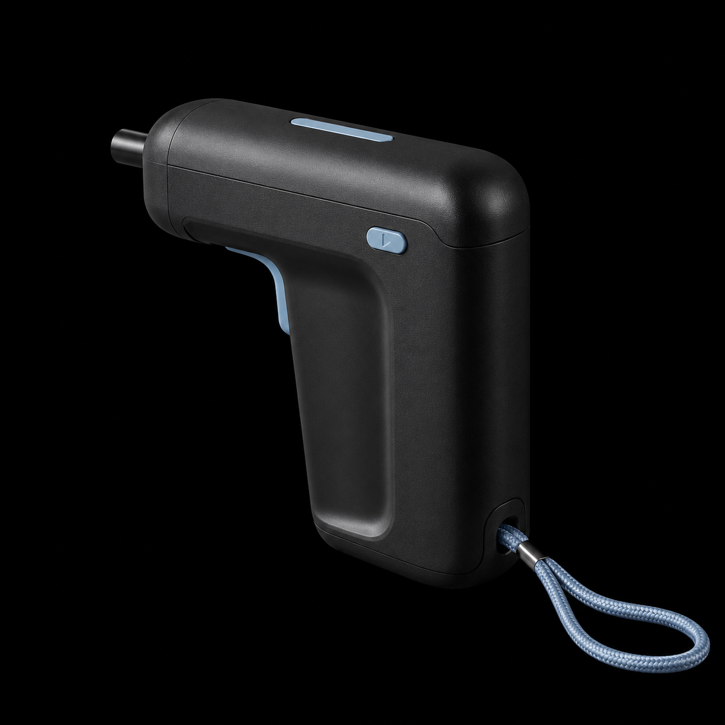
assets/generated/gen_26_05/08_variant_renders_dark/trixig_260526_u224_dark-tall-body.png
