lukketsvane/GK4_TRIXIG/assets/generated/gen_26_05/08_variant_renders_dark/trixig_260526_u227_dark-rectangular-grip.png

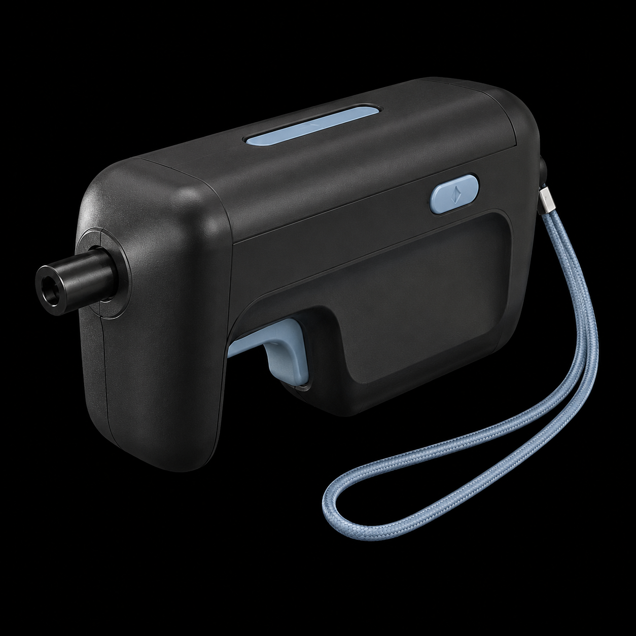
assets/generated/gen_26_05/08_variant_renders_dark/trixig_260526_u227_dark-rectangular-grip.png
