lukketsvane/GK4_TRIXIG/assets/generated/gen_26_05/08_variant_renders_dark/trixig_260526_u228_dark-polished-trapezoid.png

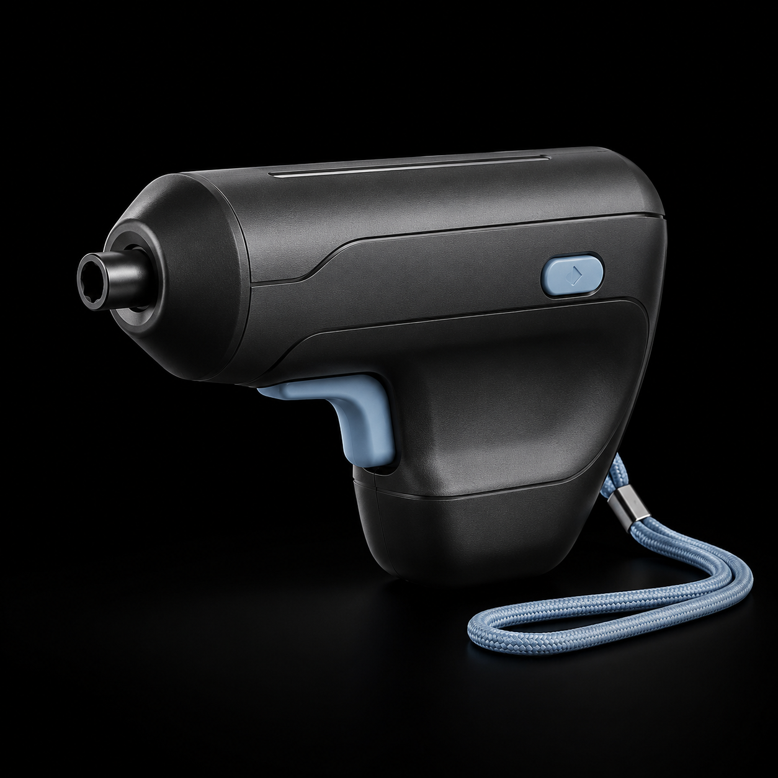
assets/generated/gen_26_05/08_variant_renders_dark/trixig_260526_u228_dark-polished-trapezoid.png
