lukketsvane/GK4_TRIXIG/assets/generated/skisser/sketches/trixig_280426_sketch_023.png

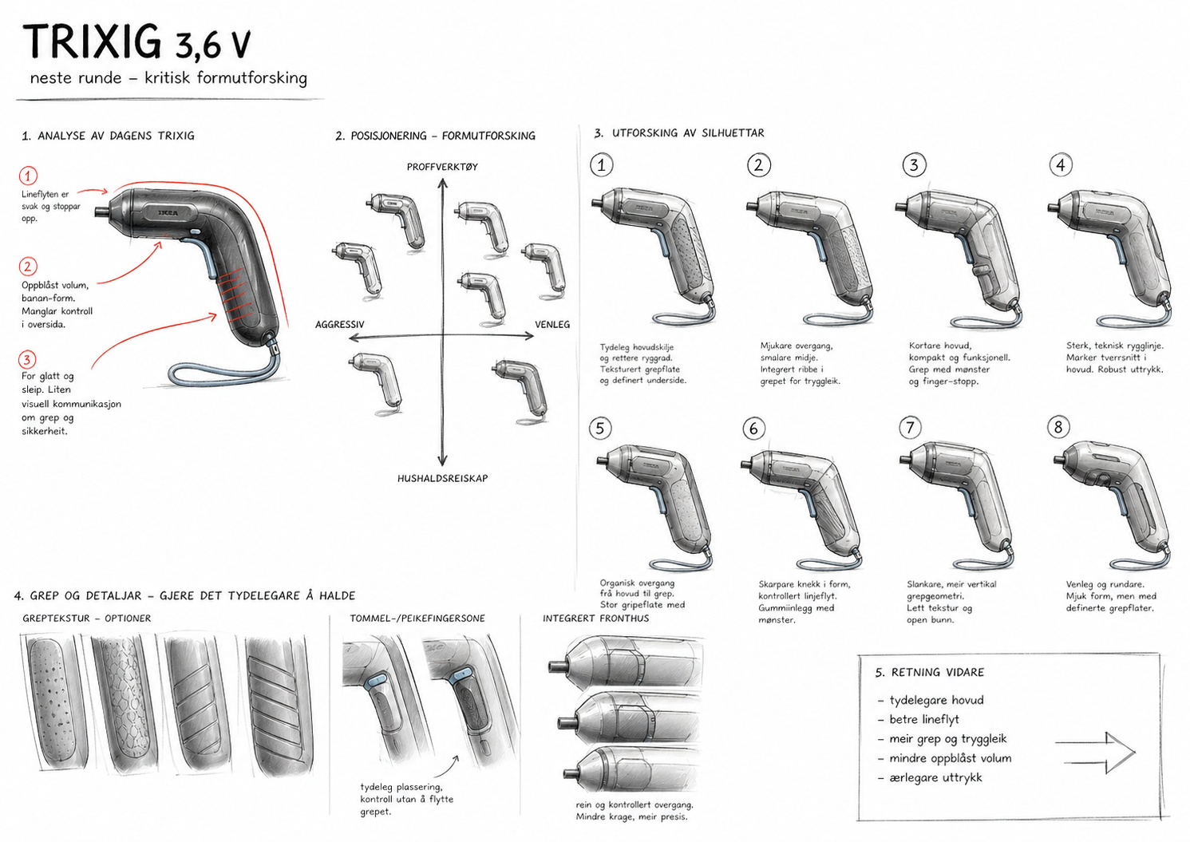
assets/generated/skisser/sketches/trixig_280426_sketch_023.png
