lukketsvane/GK4_TRIXIG/assets/generated/skisser/sketches/trixig_280426_sketch_051.png

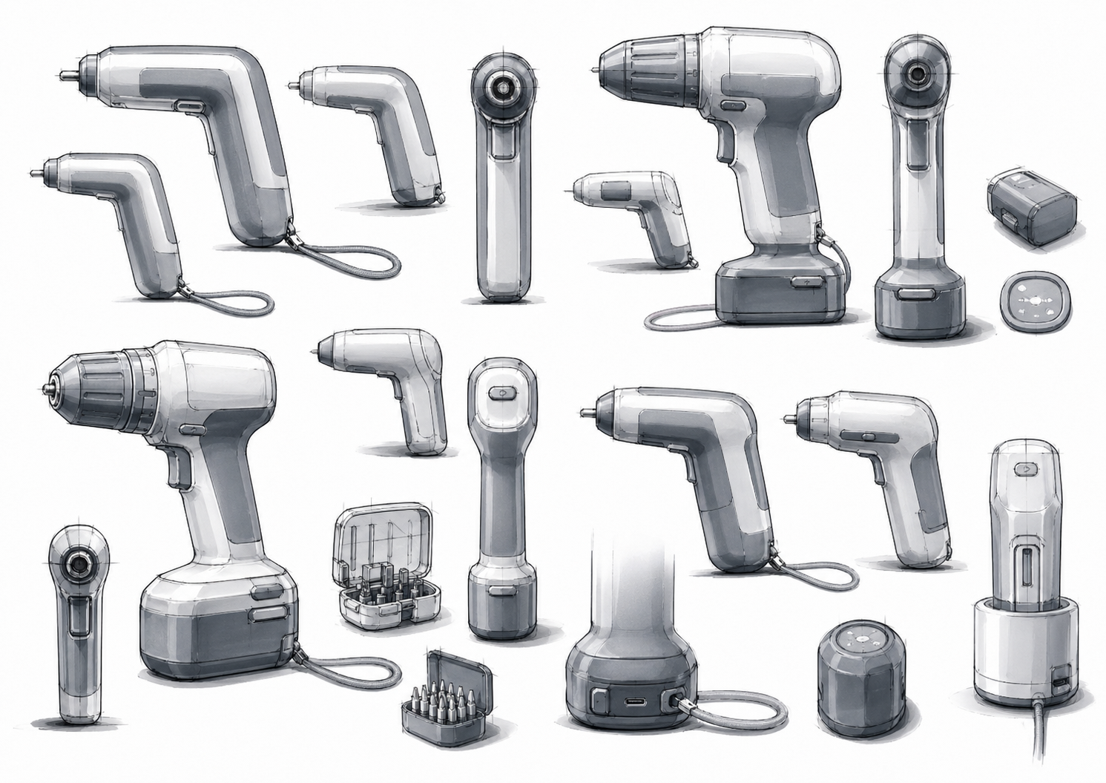
assets/generated/skisser/sketches/trixig_280426_sketch_051.png
