lukketsvane/GK4_TRIXIG/assets/generated/skisser/supplements/trixig_280426_supplement_011.png

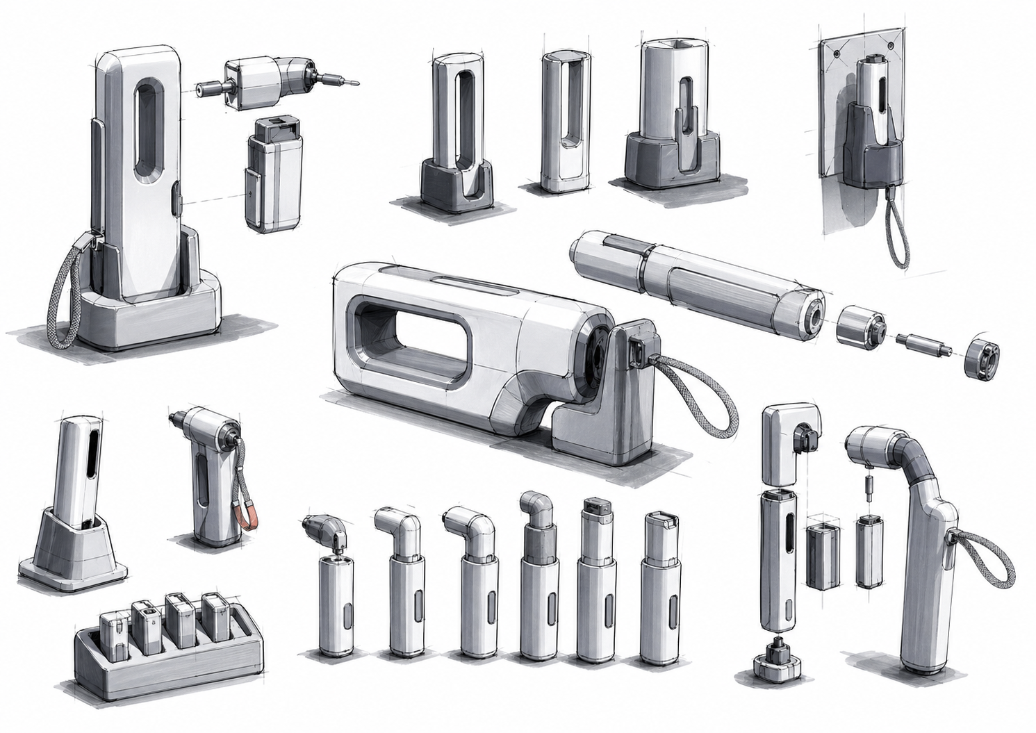
assets/generated/skisser/supplements/trixig_280426_supplement_011.png
