lukketsvane/GK4_TRIXIG/assets/generated/trixig_redesign/trixig_redesign_006.png

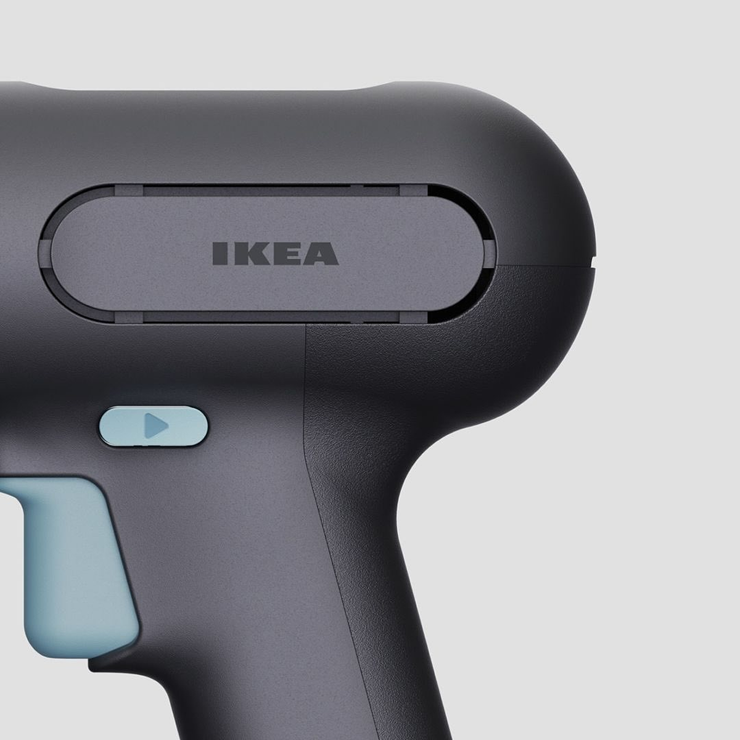
assets/generated/trixig_redesign/trixig_redesign_006.png
