lukketsvane/GK4_TRIXIG/assets/generated/trixig_redesign/trixig_redesign_016.png

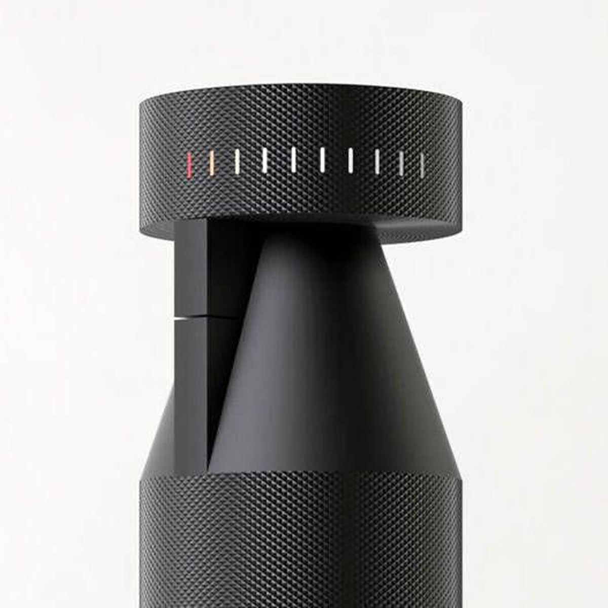
assets/generated/trixig_redesign/trixig_redesign_016.png
