lukketsvane/GK4_TRIXIG/assets/generated/trixig_redesign/trixig_redesign_021.png

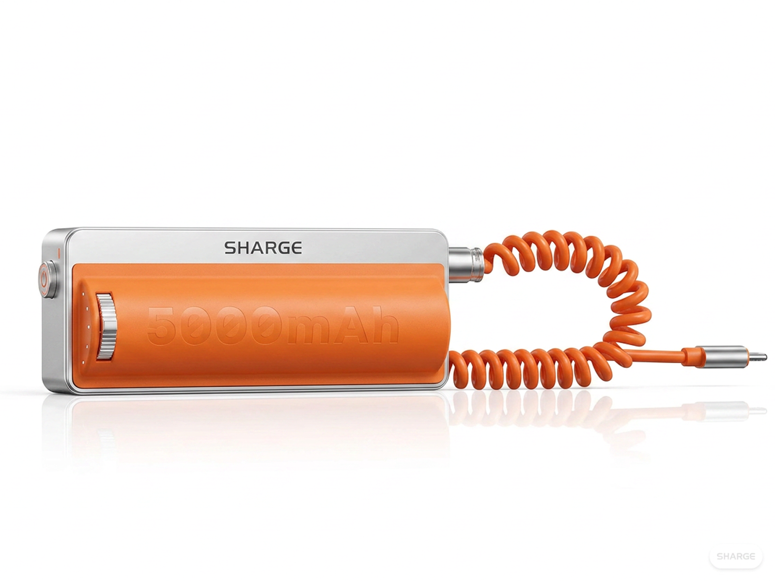
assets/generated/trixig_redesign/trixig_redesign_021.png
