lukketsvane/GK4_TRIXIG/assets/generated/trixig_redesign/trixig_redesign_024.png

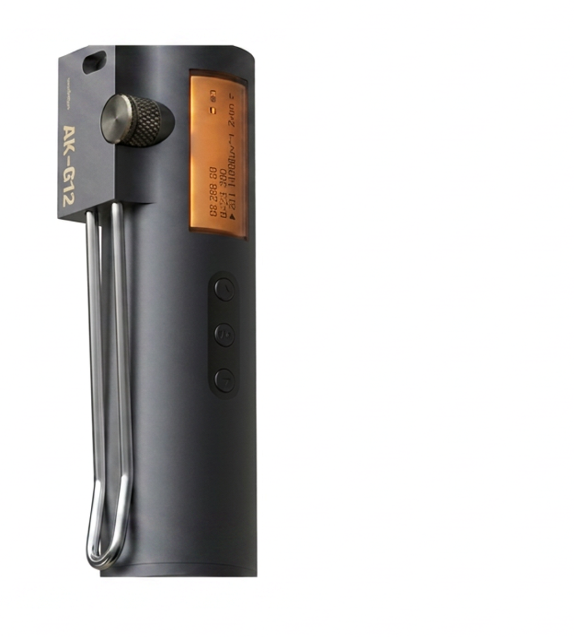
assets/generated/trixig_redesign/trixig_redesign_024.png
