lukketsvane/GK4_TRIXIG/assets/generated/trixig_redesign/trixig_redesign_032.jpg

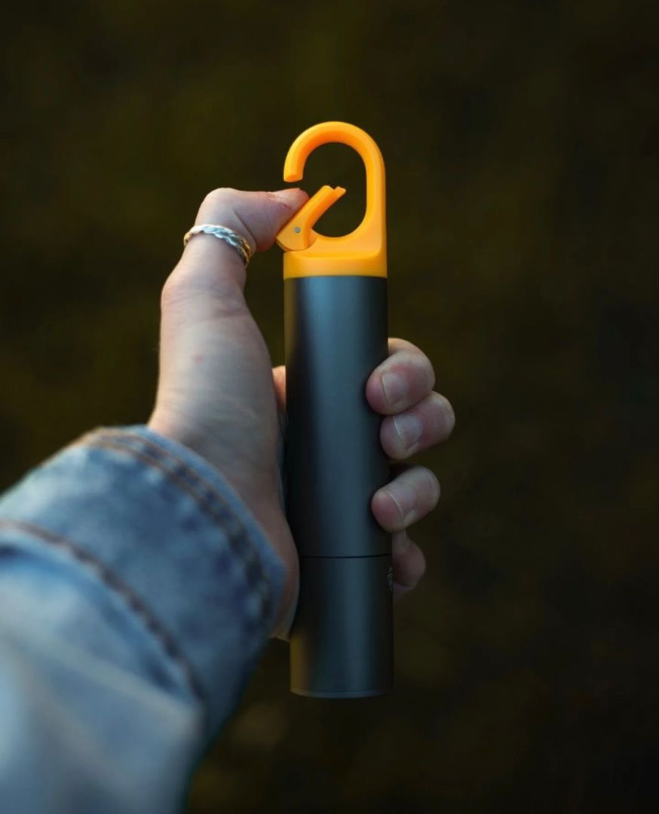
assets/generated/trixig_redesign/trixig_redesign_032.jpg
