lukketsvane/GK4_TRIXIG/assets/reference/inspiration/notat_image_asset.webp

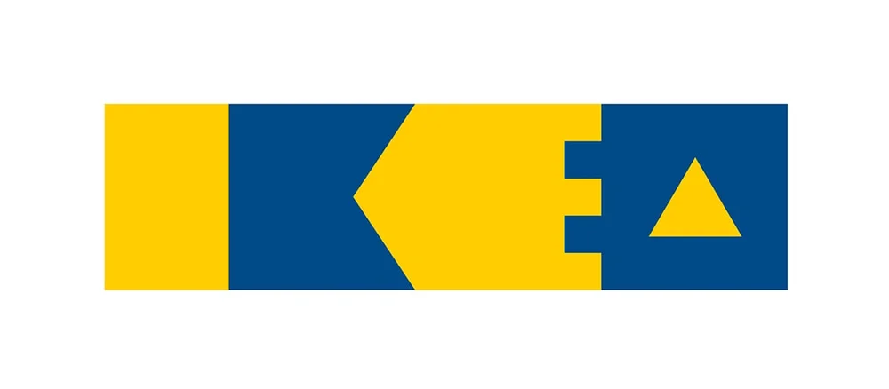
assets/reference/inspiration/notat_image_asset.webp
