lukketsvane/GK4_TRIXIG/assets/reference/inspiration/reference_002.jpg

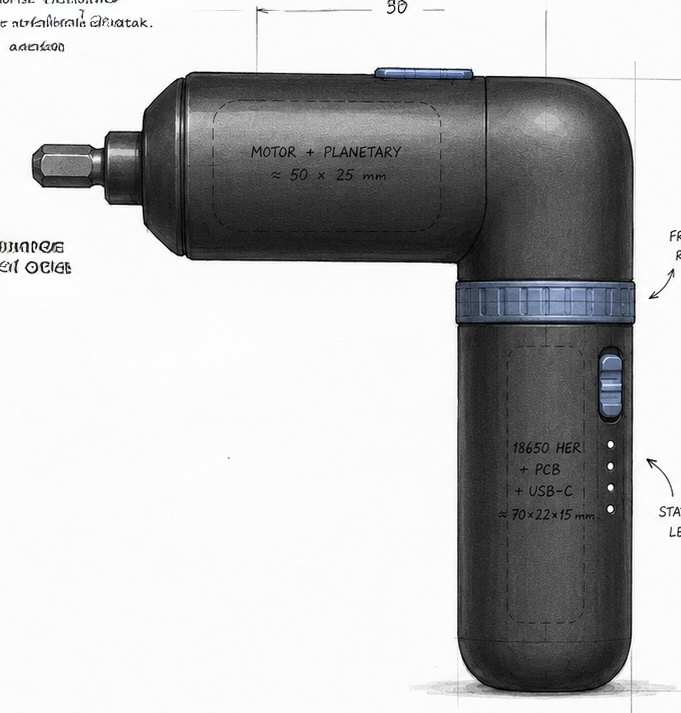
assets/reference/inspiration/reference_002.jpg
