lukketsvane/GK4_TRIXIG/assets/reference/inspiration/reference_002_2.jpg

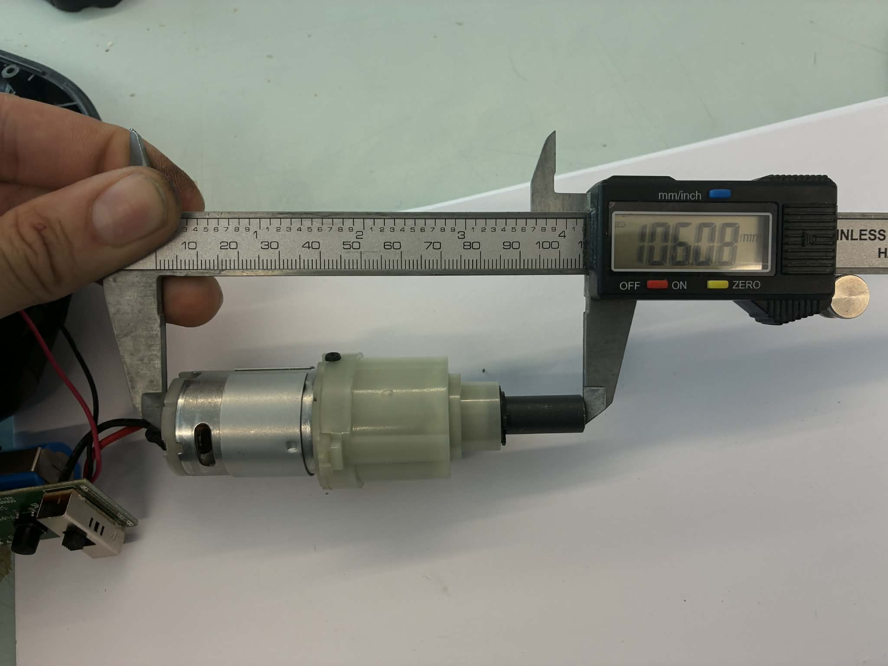
assets/reference/inspiration/reference_002_2.jpg
