lukketsvane/GK4_TRIXIG/assets/reference/inspiration/reference_003.png

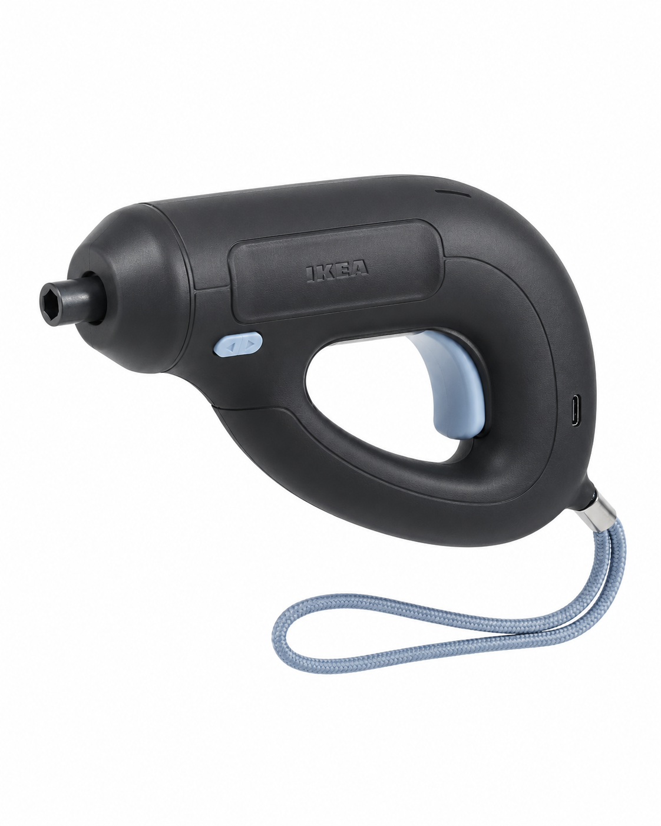
assets/reference/inspiration/reference_003.png
