lukketsvane/GK4_TRIXIG/assets/reference/inspiration/reference_004.jpeg

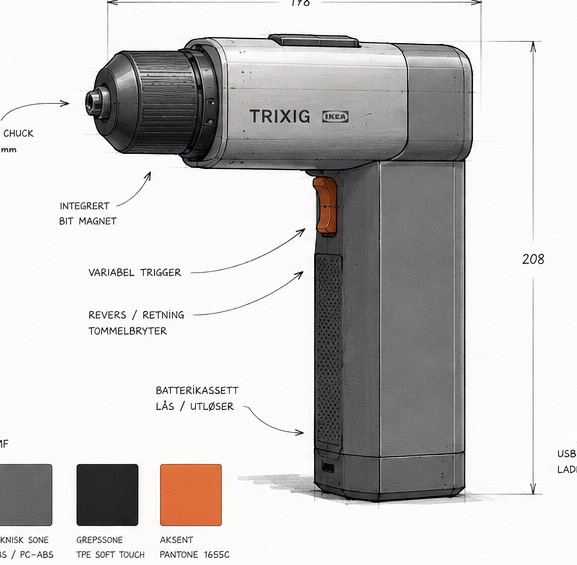
assets/reference/inspiration/reference_004.jpeg
