lukketsvane/GK4_TRIXIG/assets/reference/inspiration/reference_005.jpg

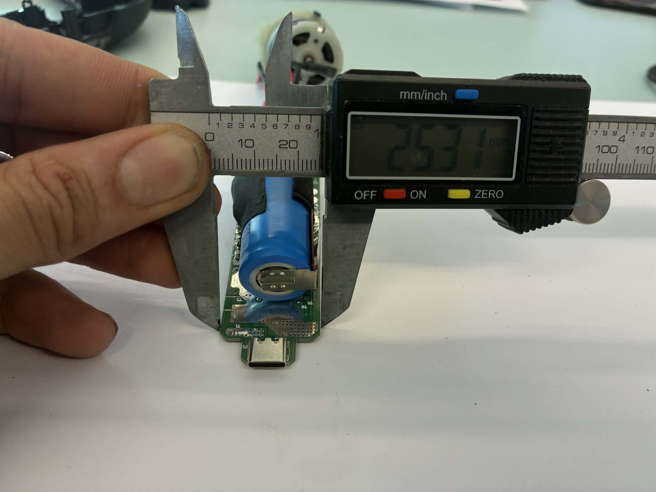
assets/reference/inspiration/reference_005.jpg
