lukketsvane/GK4_TRIXIG/assets/reference/inspiration/reference_007.jpg

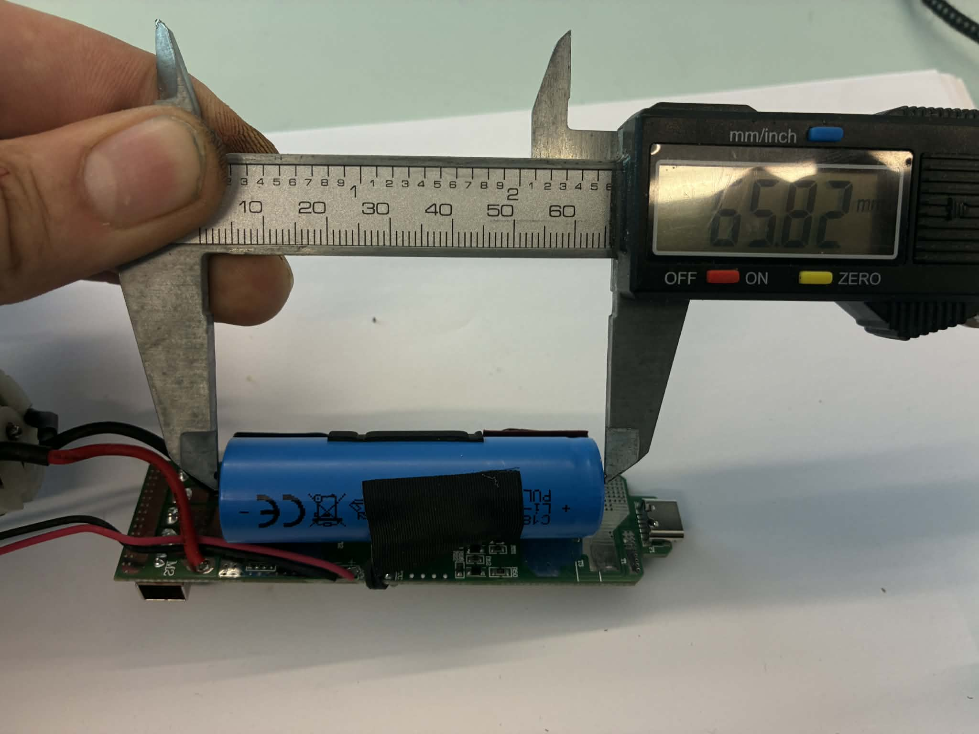
assets/reference/inspiration/reference_007.jpg
