lukketsvane/GK4_TRIXIG/assets/reference/inspiration/reference_008.jpg

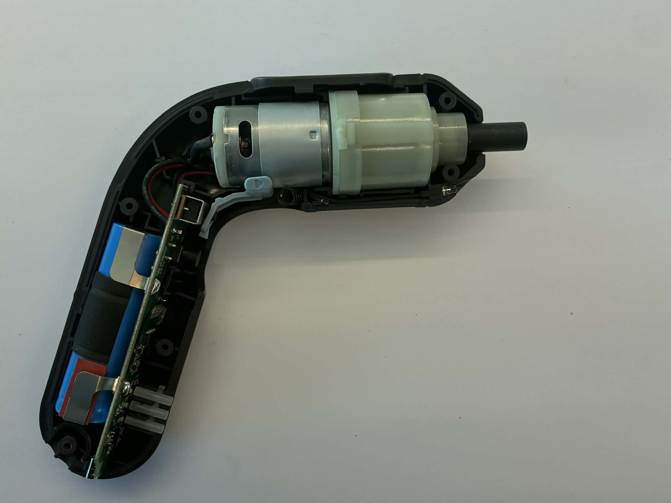
assets/reference/inspiration/reference_008.jpg
