lukketsvane/GK4_TRIXIG/assets/reference/inspiration/reference_013.jpg

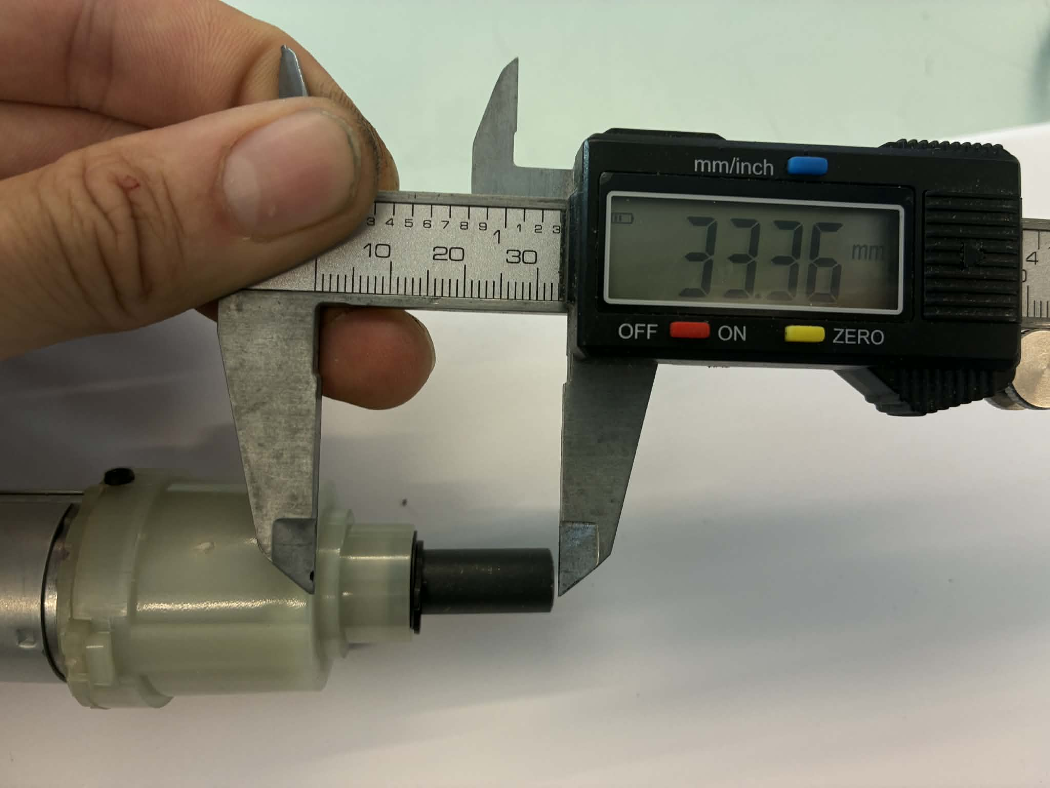
assets/reference/inspiration/reference_013.jpg
