lukketsvane/GK4_TRIXIG/assets/reference/inspiration/reference_014.jpg

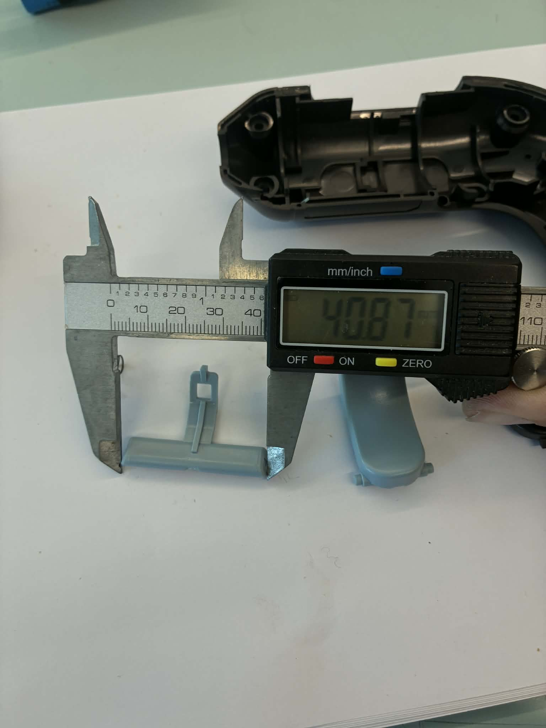
assets/reference/inspiration/reference_014.jpg
