lukketsvane/GK4_TRIXIG/assets/reference/inspiration/reference_016.jpg

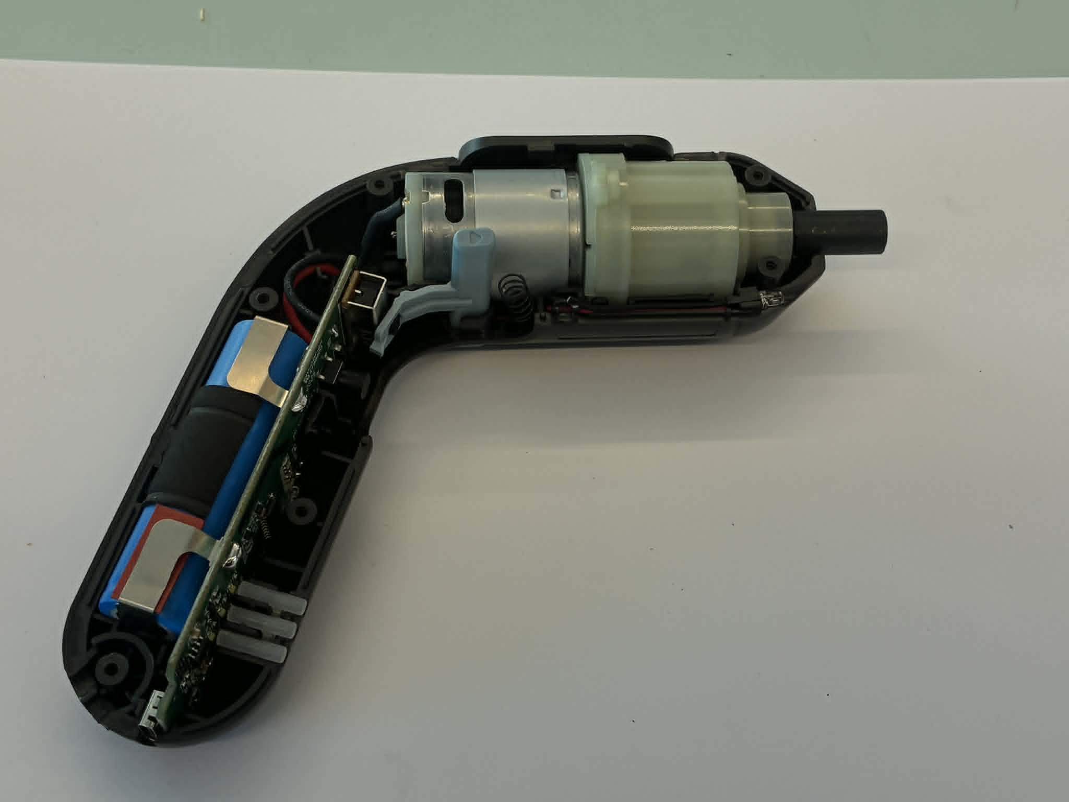
assets/reference/inspiration/reference_016.jpg
