lukketsvane/GK4_TRIXIG/assets/reference/inspiration/reference_020.jpg

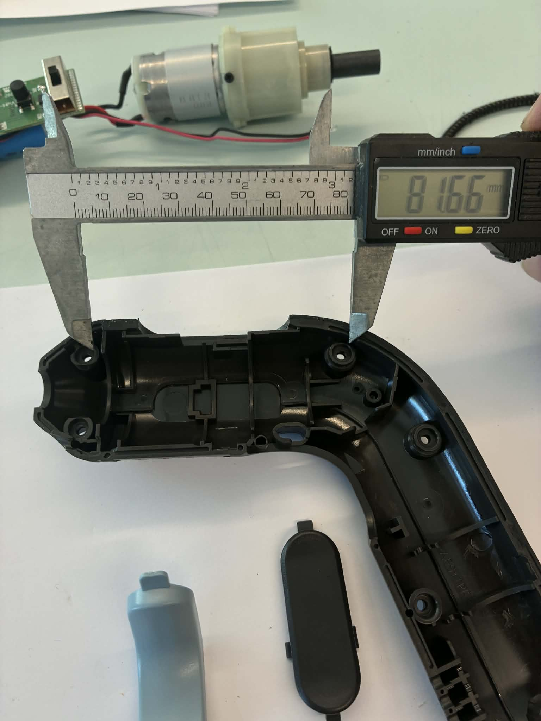
assets/reference/inspiration/reference_020.jpg
