lukketsvane/GK4_TRIXIG/assets/reference/inspiration/reference_022.jpg

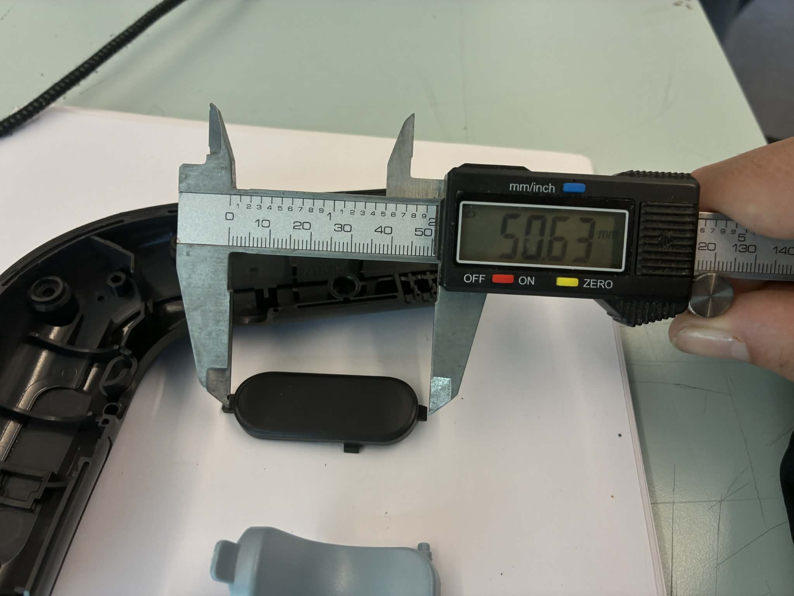
assets/reference/inspiration/reference_022.jpg
