lukketsvane/GK4_TRIXIG/assets/reference/inspiration/reference_023.jpg

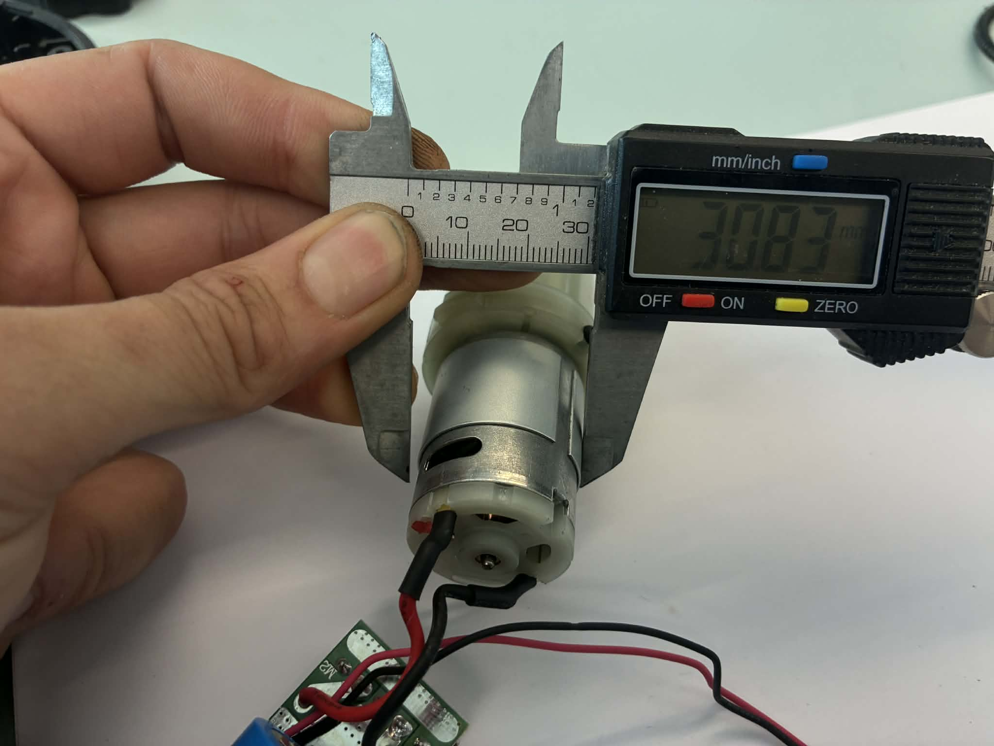
assets/reference/inspiration/reference_023.jpg
