lukketsvane/GK4_TRIXIG/assets/reference/inspiration/reference_025.jpg

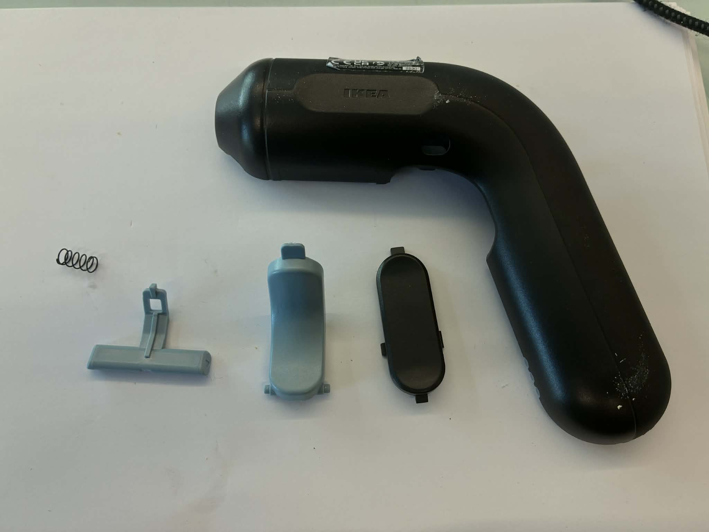
assets/reference/inspiration/reference_025.jpg
