lukketsvane/GK4_TRIXIG/assets/reference/inspiration/reference_026.jpg

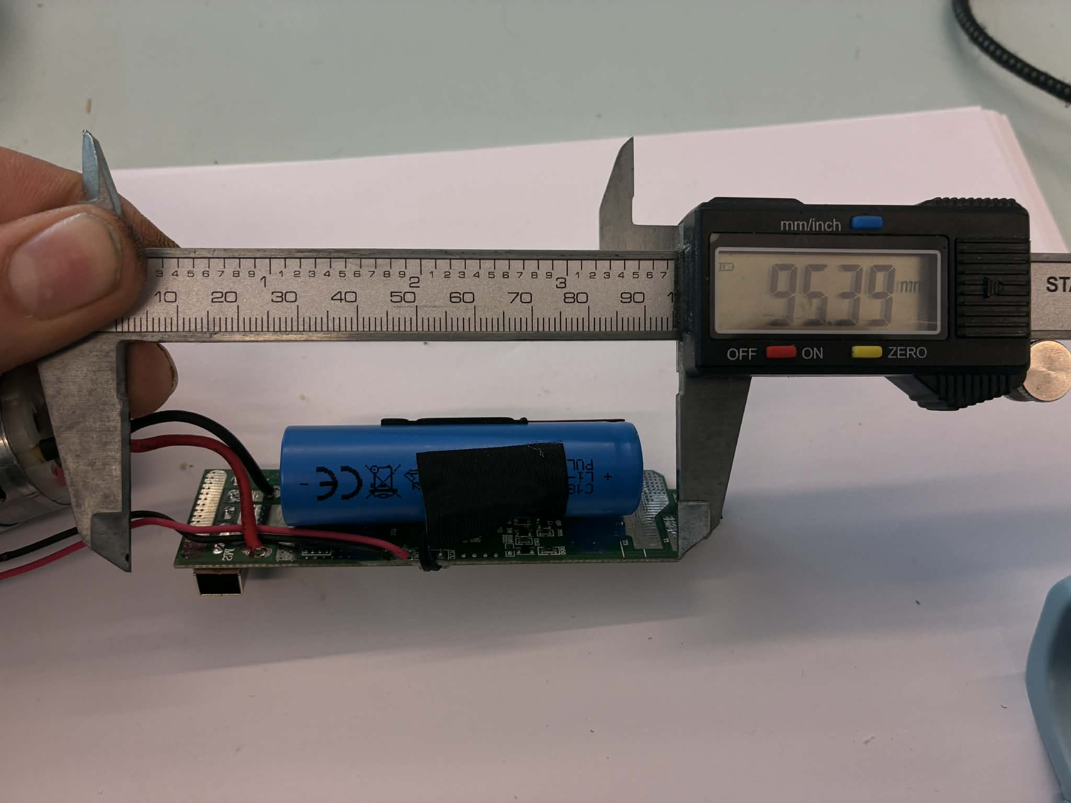
assets/reference/inspiration/reference_026.jpg
