lukketsvane/GK4_TRIXIG/assets/reference/inspiration/reference_029.png

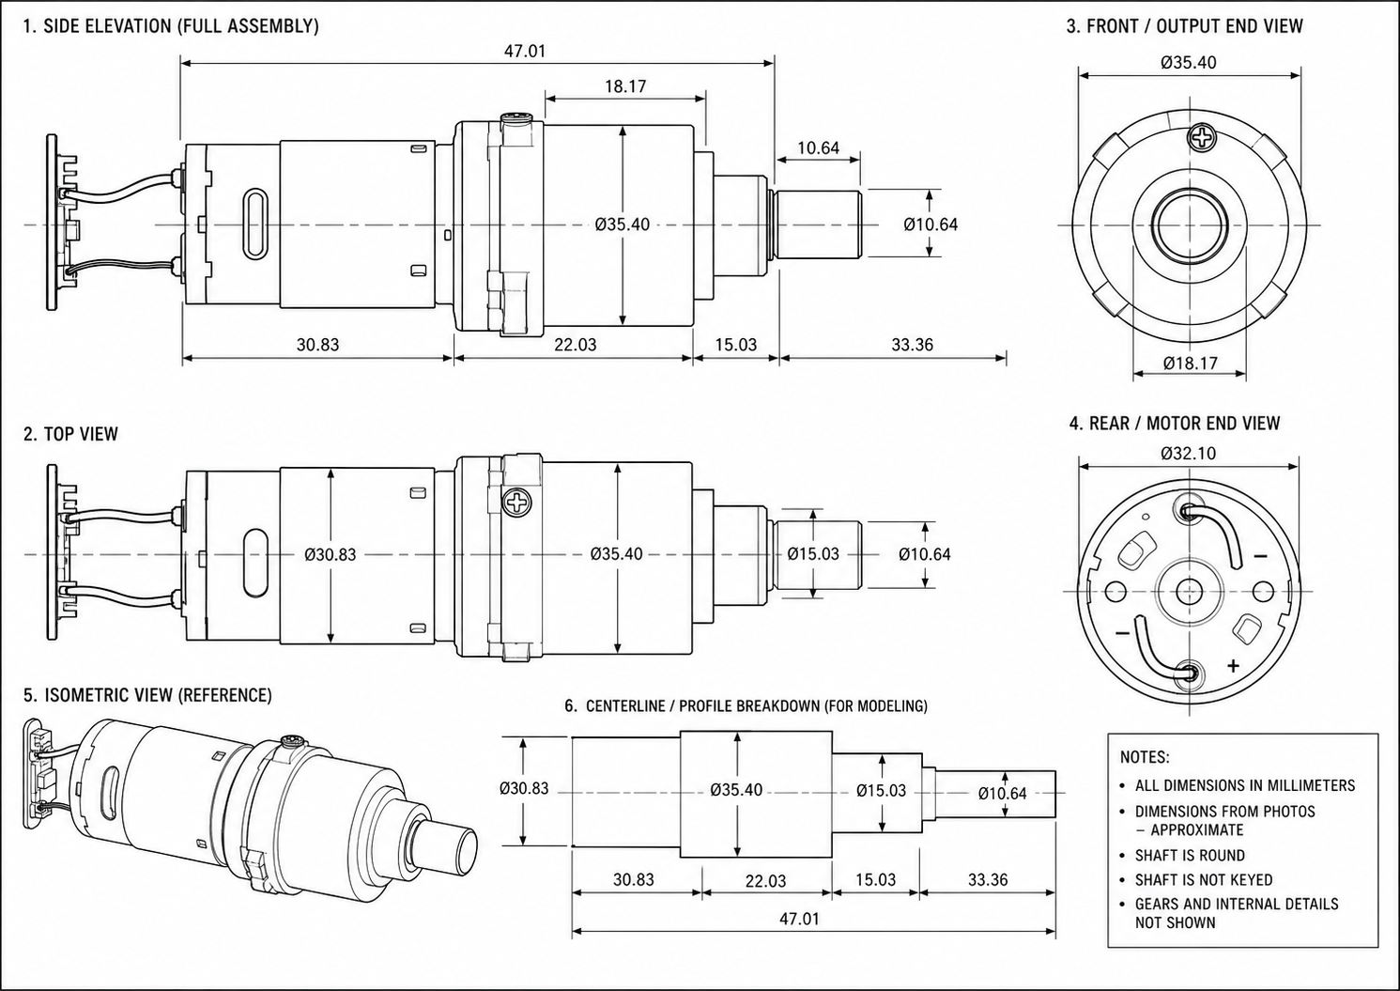
assets/reference/inspiration/reference_029.png
