lukketsvane/GK4_TRIXIG/assets/reference/inspiration/reference_031.png

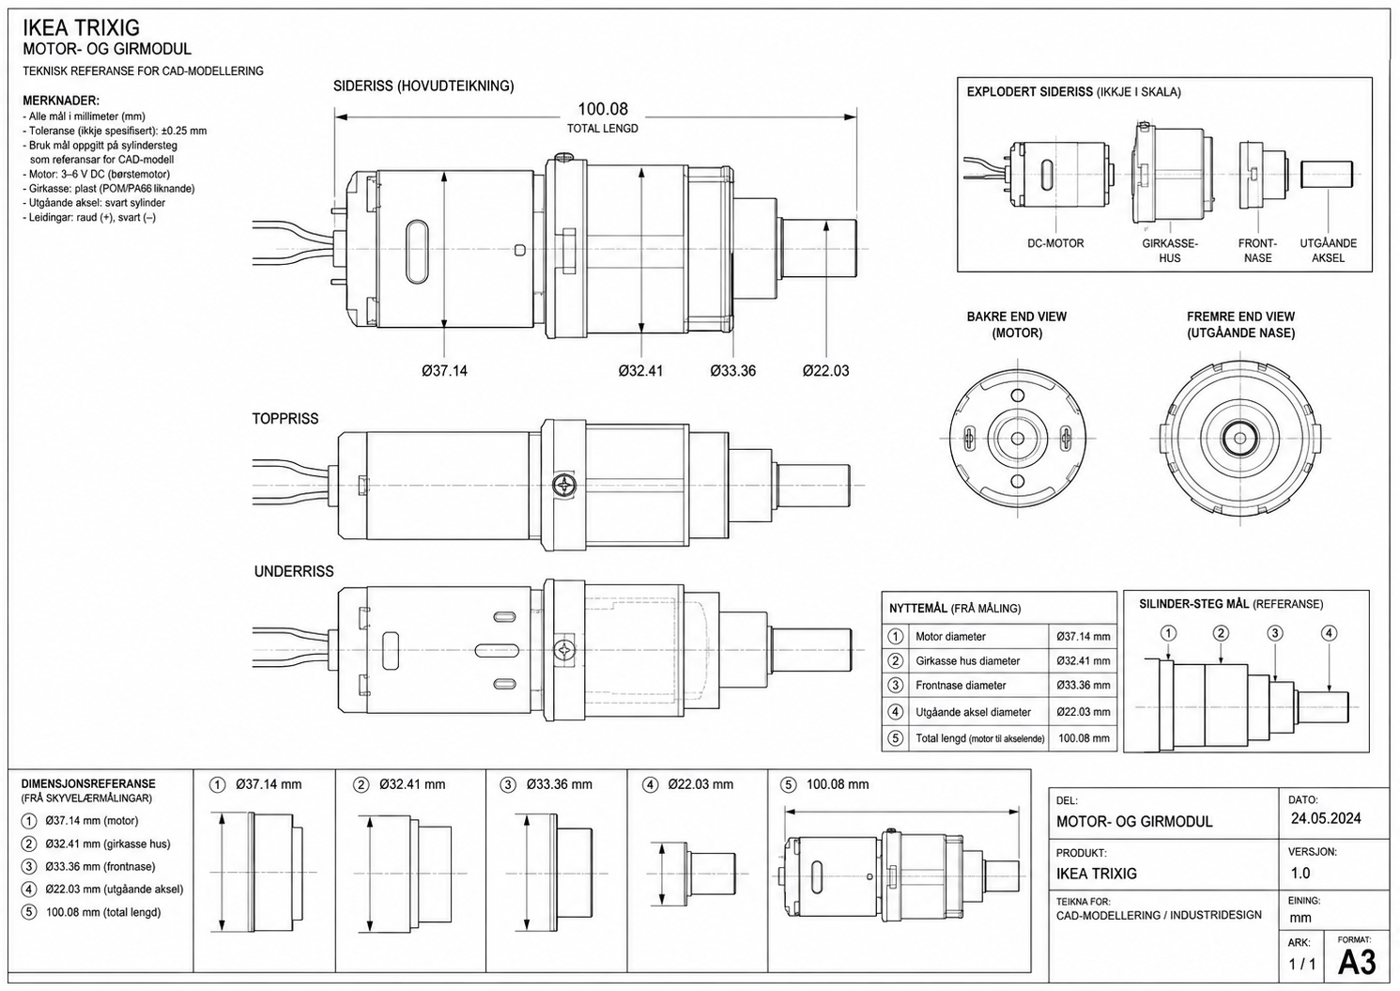
assets/reference/inspiration/reference_031.png
