lukketsvane/GK4_TRIXIG/assets/reference/inspiration/reference_032.png

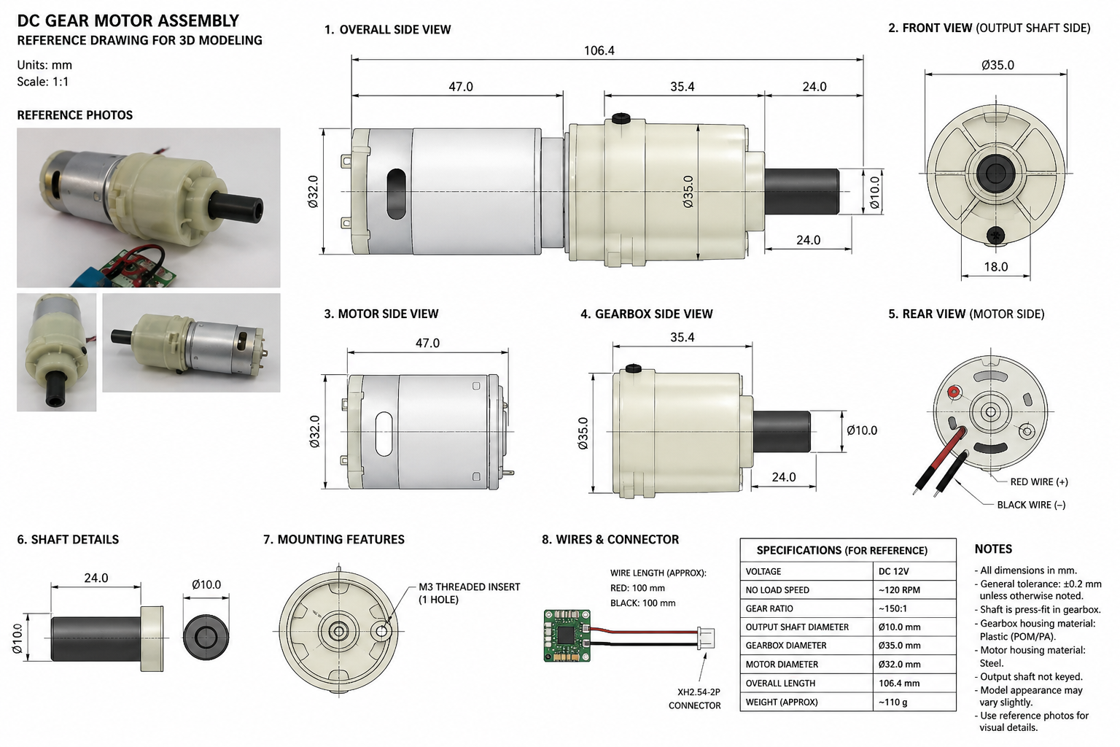
assets/reference/inspiration/reference_032.png
