lukketsvane/GK4_TRIXIG/assets/reference/inspiration/reference_037.jpg

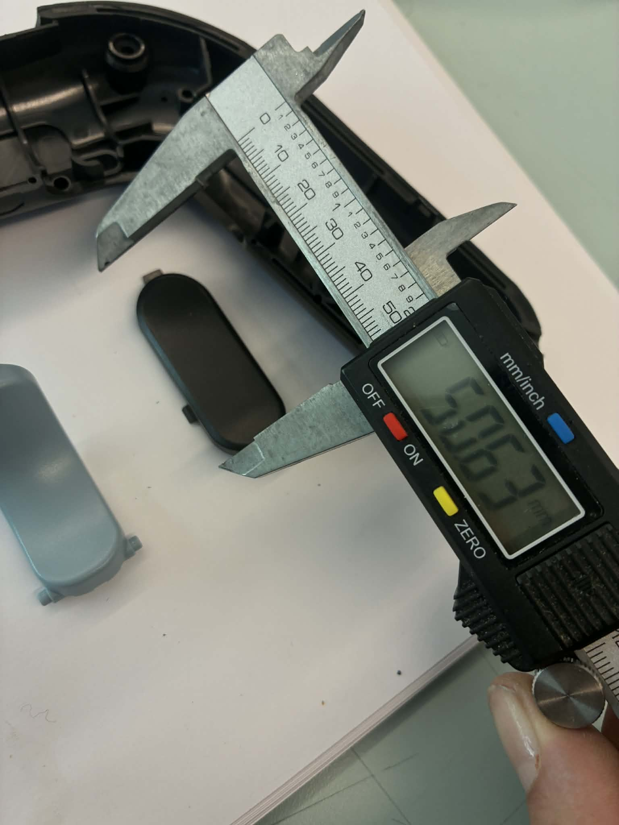
assets/reference/inspiration/reference_037.jpg
