lukketsvane/GK4_TRIXIG/assets/reference/teardown/motor_02.png

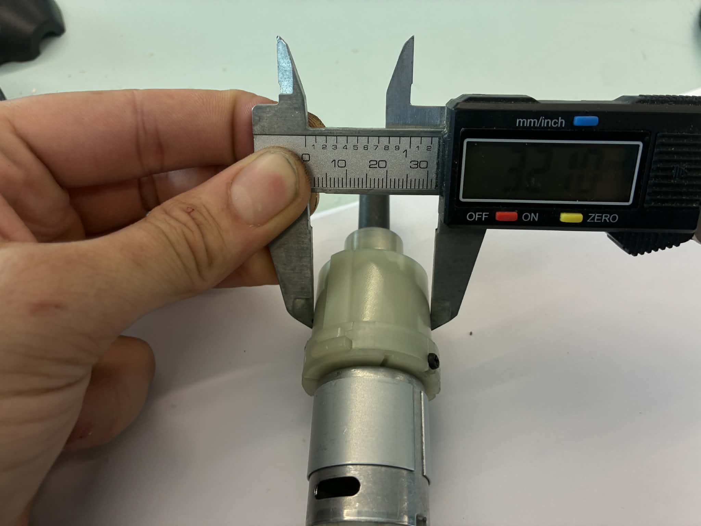
assets/reference/teardown/motor_02.png
