lukketsvane/GK4_TRIXIG/assets/reference/teardown/motor_08.png

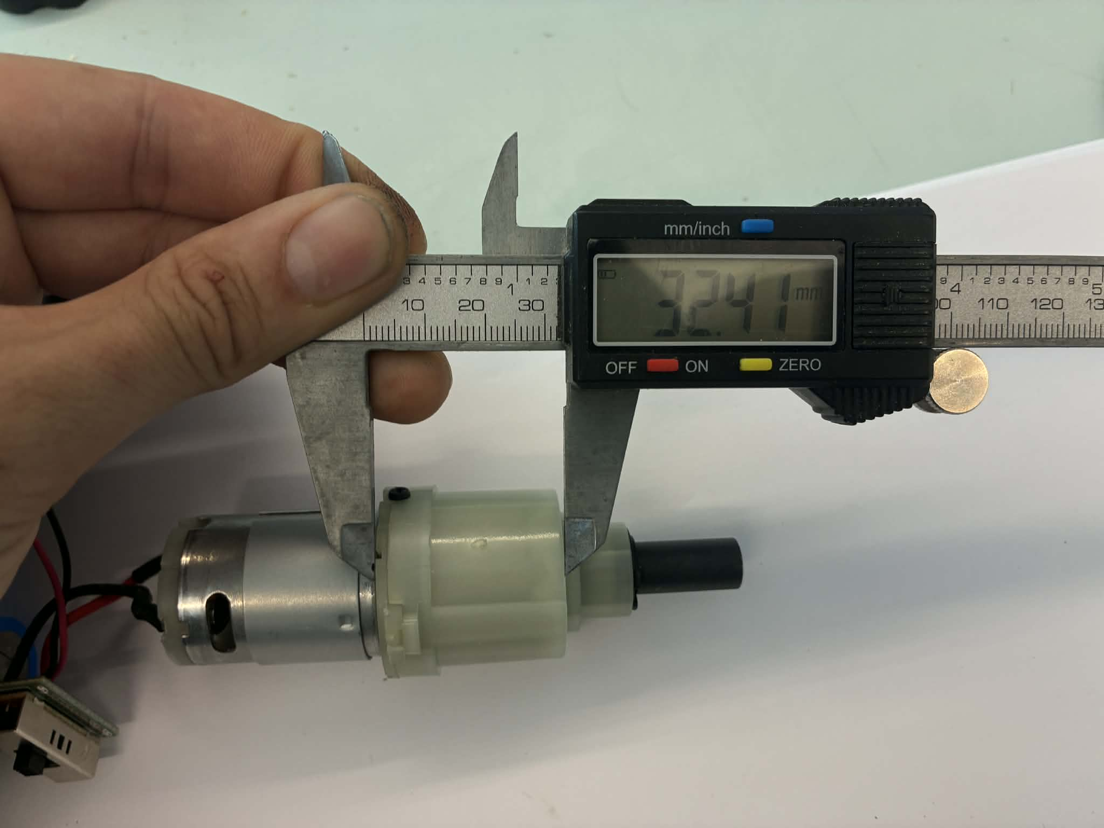
assets/reference/teardown/motor_08.png
