lukketsvane/GK4_TRIXIG/assets/reference/teardown/motor_10.png

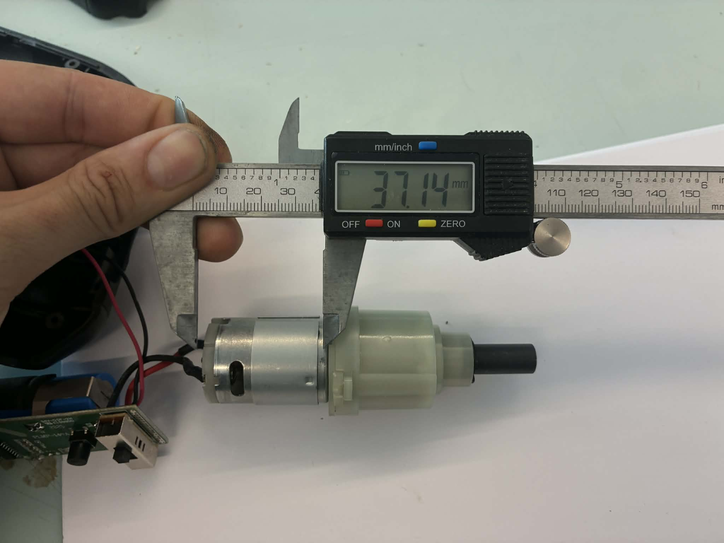
assets/reference/teardown/motor_10.png
