lukketsvane/GK4_TRIXIG/assets/reference/teardown/motor_11.png

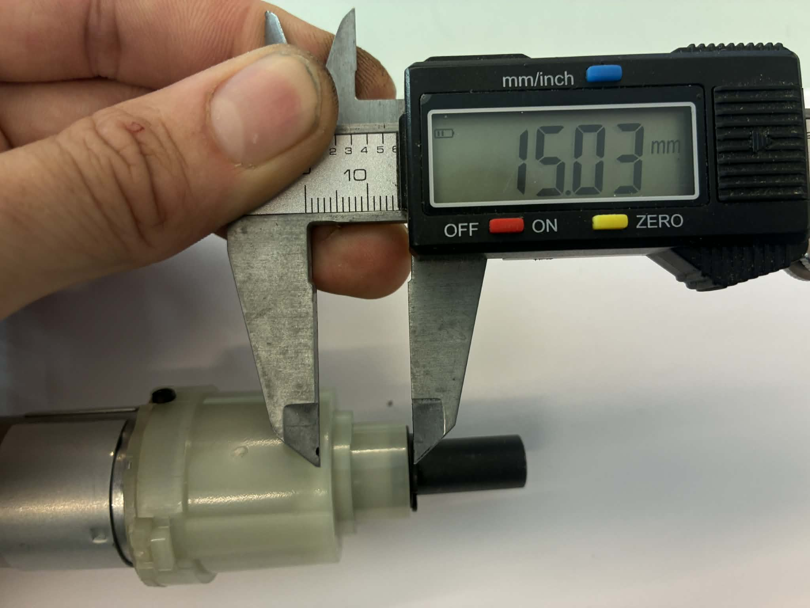
assets/reference/teardown/motor_11.png
