lukketsvane/GK4_TRIXIG/assets/reference/teardown/motor_12.png

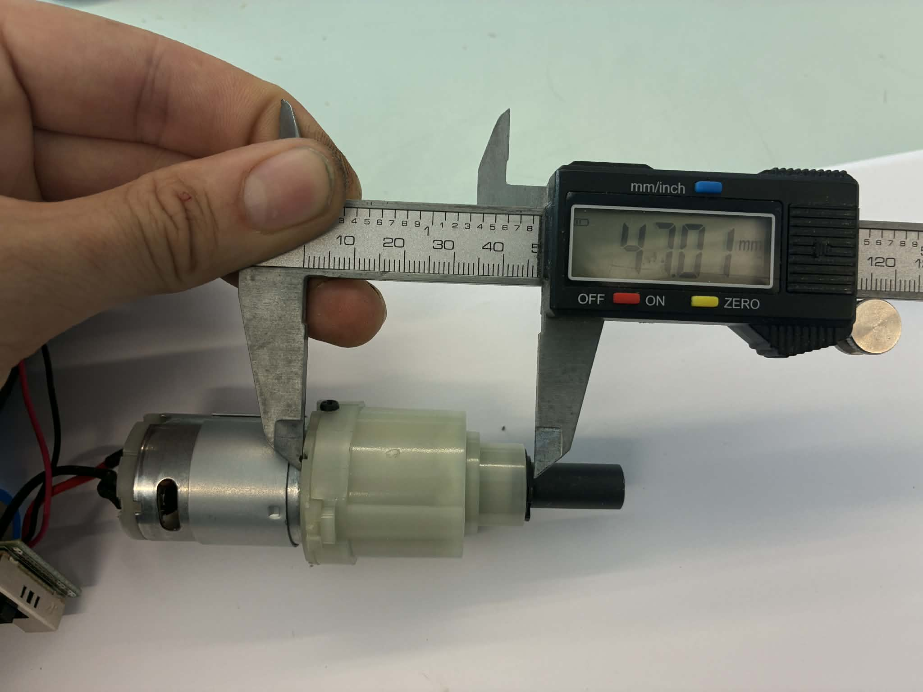
assets/reference/teardown/motor_12.png
