lukketsvane/GK4_TRIXIG/docs/deliverables/08_mai_konseptgjennomgang/konsept_b_tactil.png

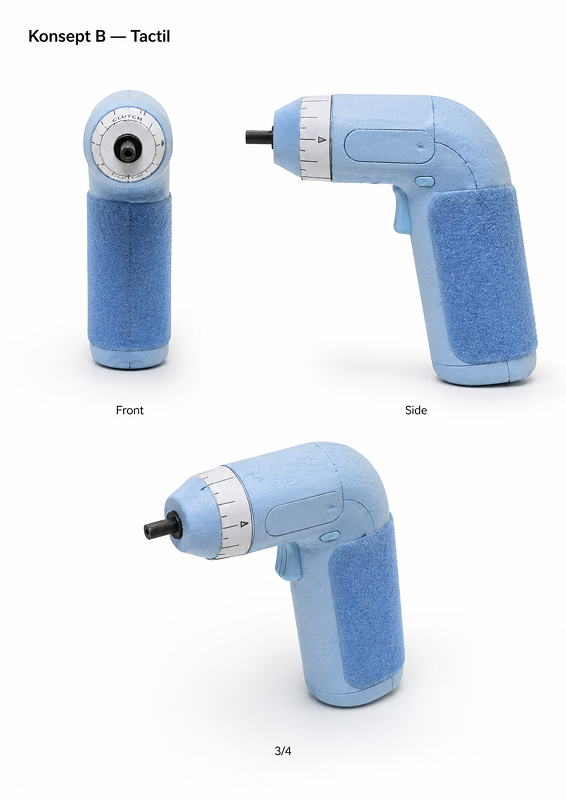
docs/deliverables/08_mai_konseptgjennomgang/konsept_b_tactil.png
