lukketsvane/GK4_TRIXIG/docs/deliverables/11_mai_formforingsplansje/form_before_after_02.png

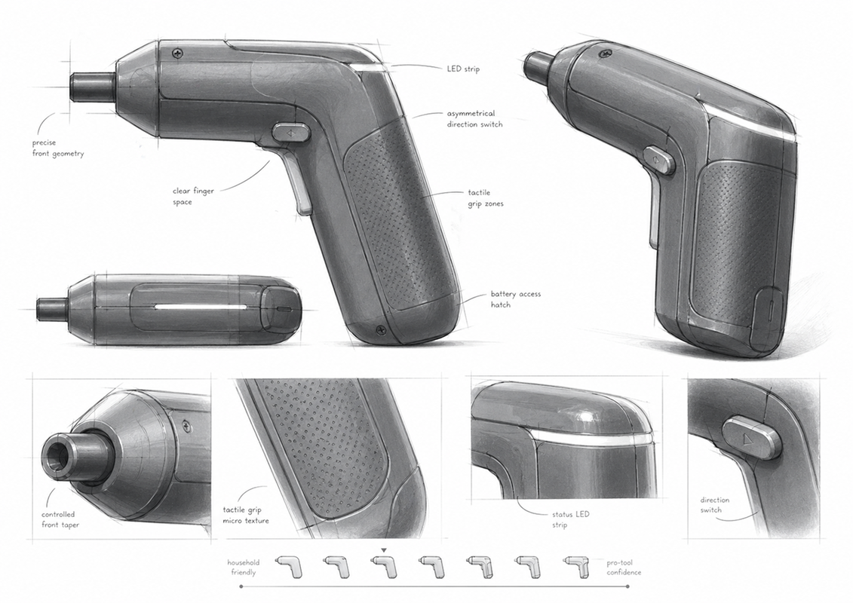
docs/deliverables/11_mai_formforingsplansje/form_before_after_02.png
