lukketsvane/GK4_TRIXIG/docs/deliverables/25_mai_sluttpresentasjon/emballasje_konsept.png

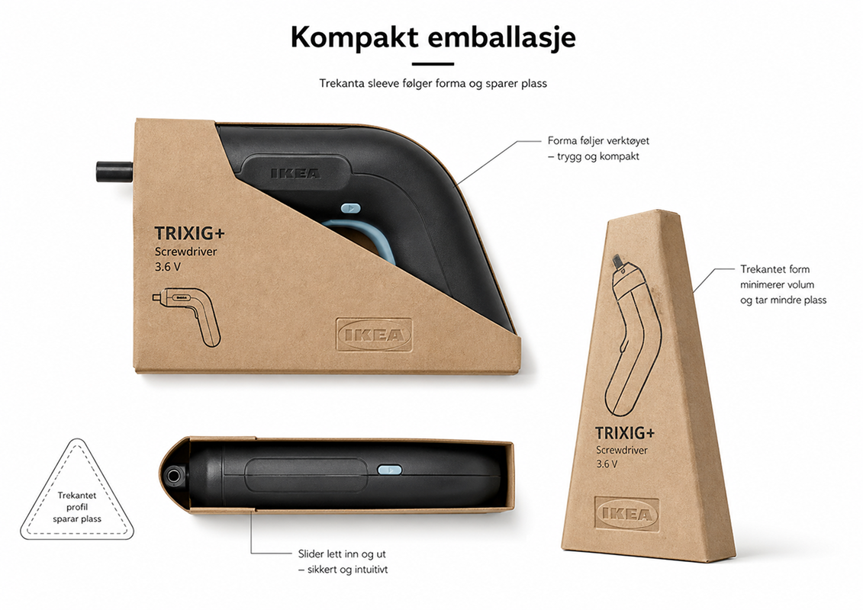
docs/deliverables/25_mai_sluttpresentasjon/emballasje_konsept.png
