lukketsvane/GK4_TRIXIG/docs/deliverables/25_mai_sluttpresentasjon/kompakt_bevis.png

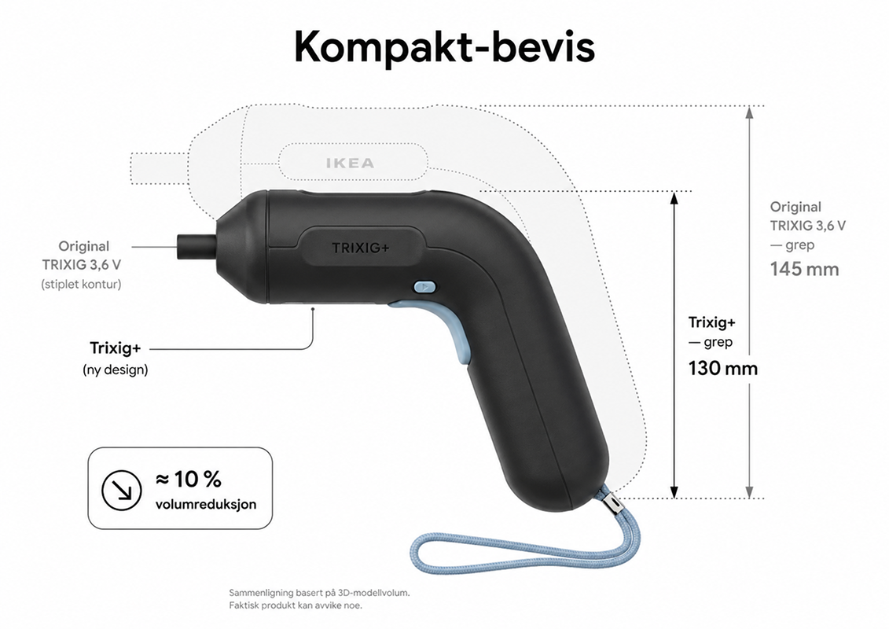
docs/deliverables/25_mai_sluttpresentasjon/kompakt_bevis.png
