lukketsvane/GK4_TRIXIG/methods/tjalve/tjalve_pdfpage_010_02_product_synthesis.png

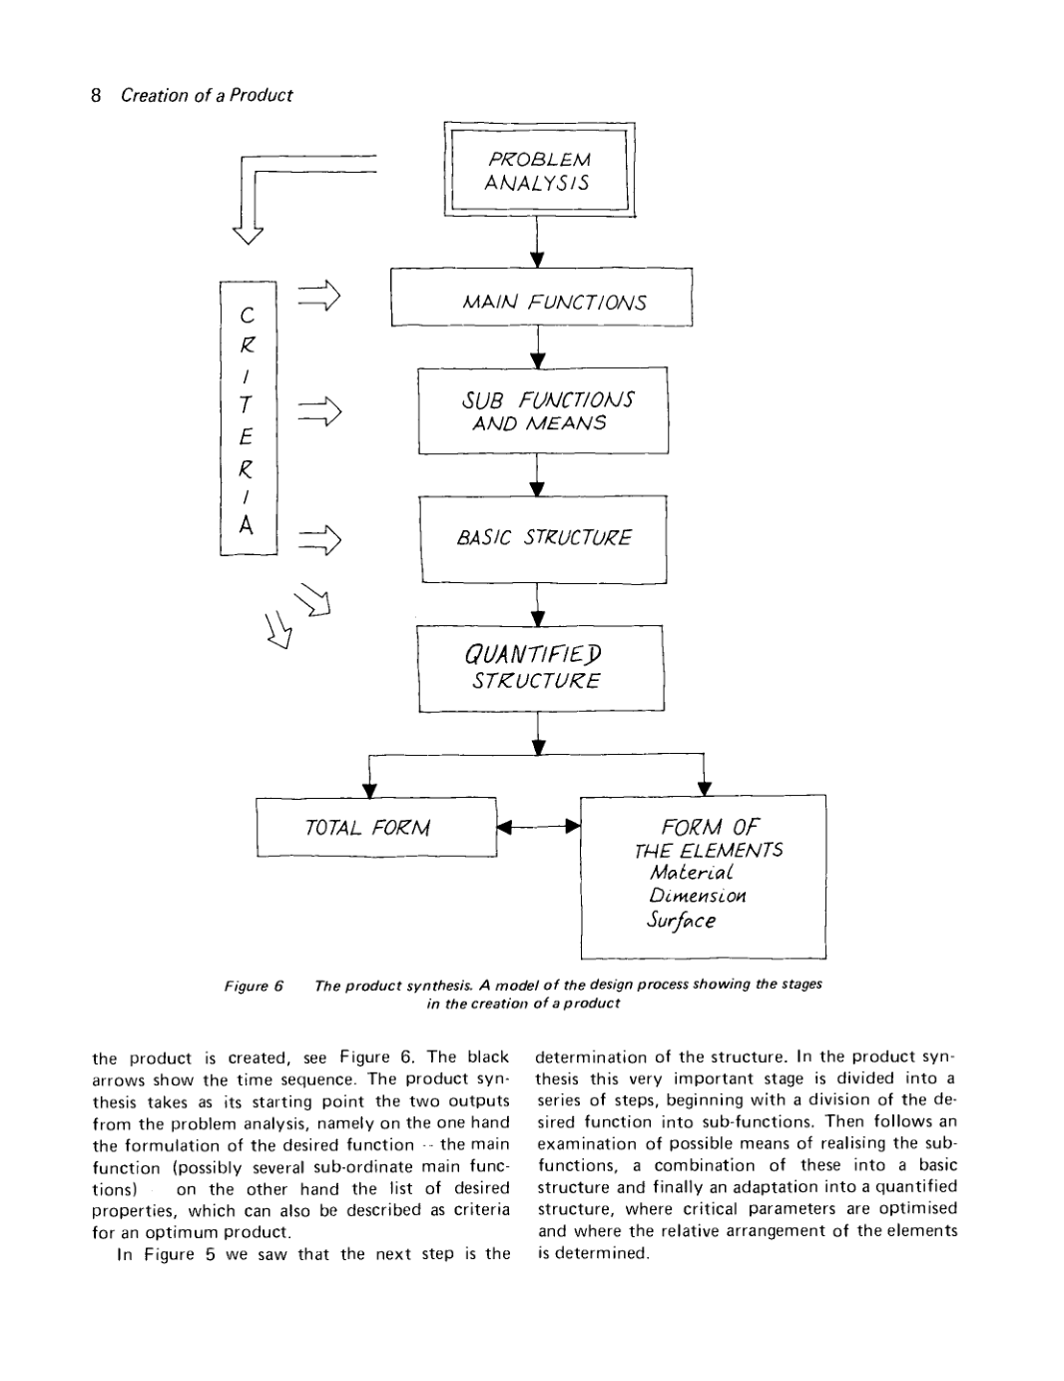
methods/tjalve/tjalve_pdfpage_010_02_product_synthesis.png
