lukketsvane/GK4_TRIXIG/assets/finished_graphics/skisser/alt_fjern_kvitt/component_1.png

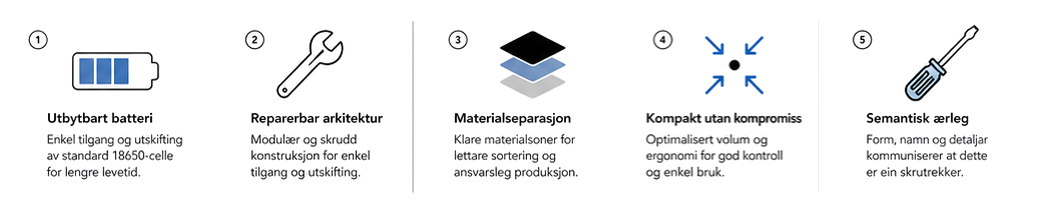
assets/finished_graphics/skisser/alt_fjern_kvitt/component_1.png
