lukketsvane/GK4_TRIXIG/assets/finished_graphics/skisser/alt_isnet_general_use/component_1.png

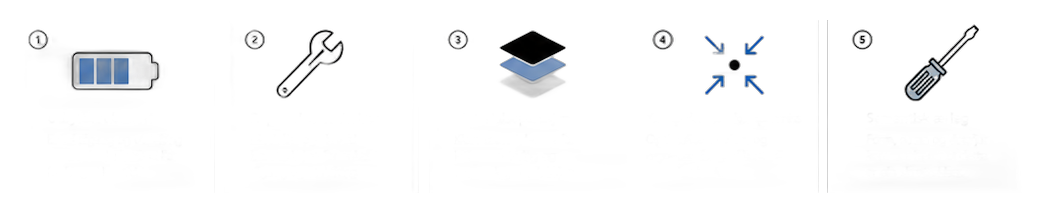
assets/finished_graphics/skisser/alt_isnet_general_use/component_1.png
