lukketsvane/GK4_TRIXIG/assets/generated/gen_26_05/03_process_boards/trixig_260526_u034_component-layouts.png

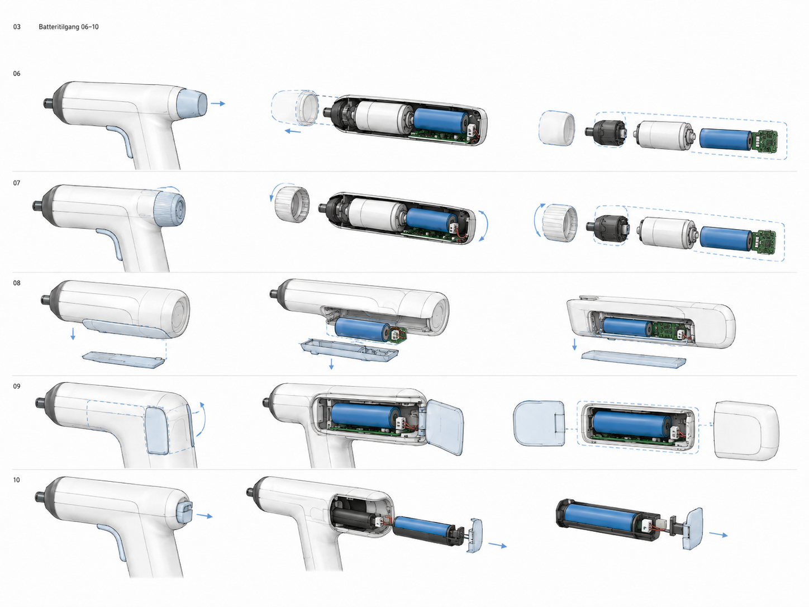
assets/generated/gen_26_05/03_process_boards/trixig_260526_u034_component-layouts.png
