lukketsvane/GK4_TRIXIG/assets/generated/gen_26_05/03_process_boards/trixig_260526_u047_parts-catalog.png

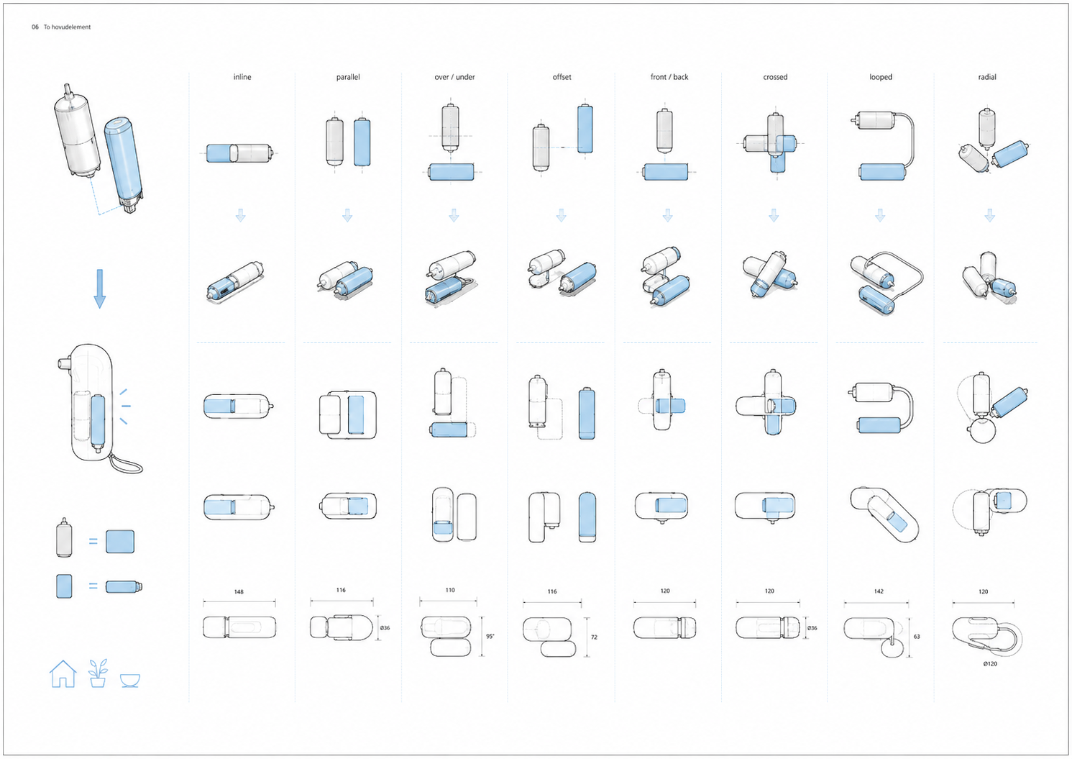
assets/generated/gen_26_05/03_process_boards/trixig_260526_u047_parts-catalog.png
