lukketsvane/GK4_TRIXIG/cad/print/trixig_redesign/for_bambu/motor_gear_module.stl

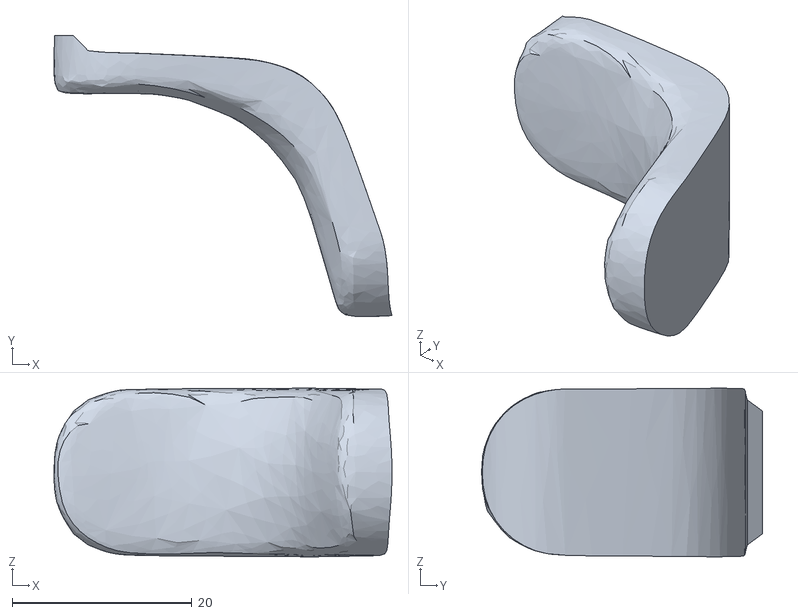
[picture p304: CAD file, 2026-05-26]
cad/print/trixig_redesign/for_bambu/motor_gear_module.stl
37.6 x 31.2 x 18.7
