lukketsvane/GK4_TRIXIG/cad/print/trixig_redesign/for_bambu/rear_end_cap.stl

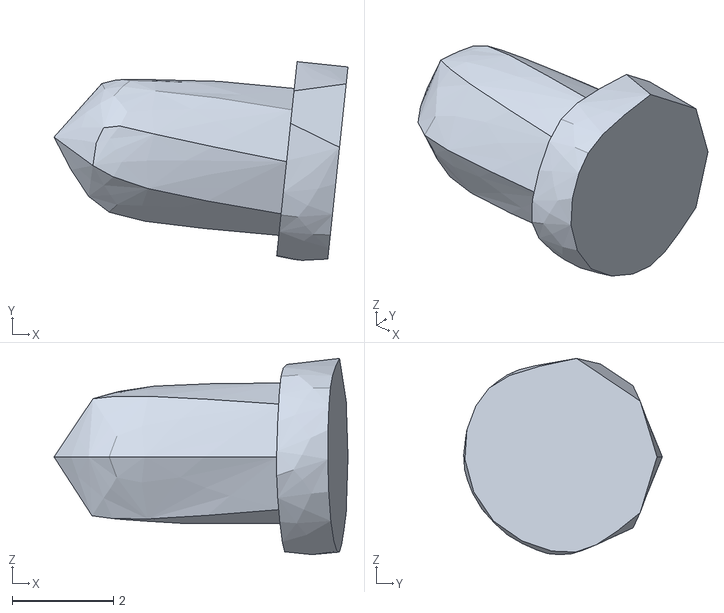
[picture p305: CAD file, 2026-05-26]
cad/print/trixig_redesign/for_bambu/rear_end_cap.stl
5.82 x 3.94 x 3.89
