lukketsvane/GK4_TRIXIG/cad/print/trixig_redesign/trixig_buildplate_stl_7.stl

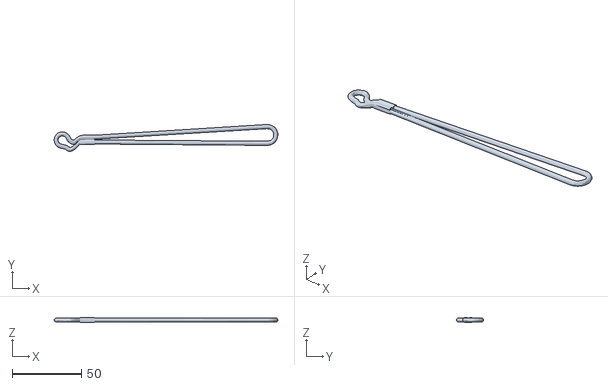
[picture p306: CAD file, 2026-05-26]
cad/print/trixig_redesign/trixig_buildplate_stl_7.stl
162.0 x 19.6 x 3.60
