lukketsvane/GK4_TRIXIG/cad/print/trixig_redesign/trixig_buildplate_stl_16.stl

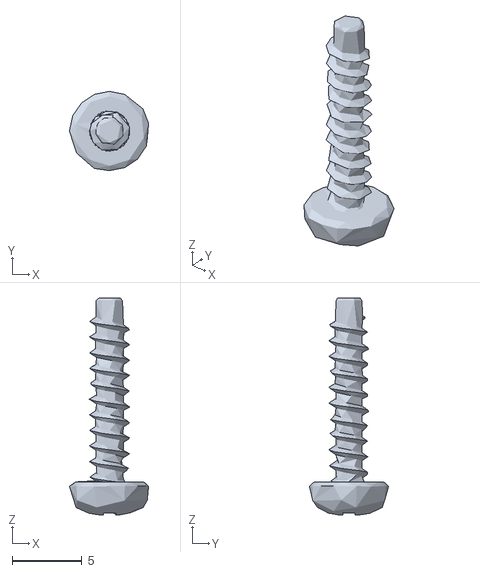
[picture p307: CAD file, 2026-05-26]
cad/print/trixig_redesign/trixig_buildplate_stl_16.stl
5.67 x 5.68 x 15.5
