lukketsvane/GK4_TRIXIG/cad/print/trixig_redesign/for_bambu/trigger_button.stl

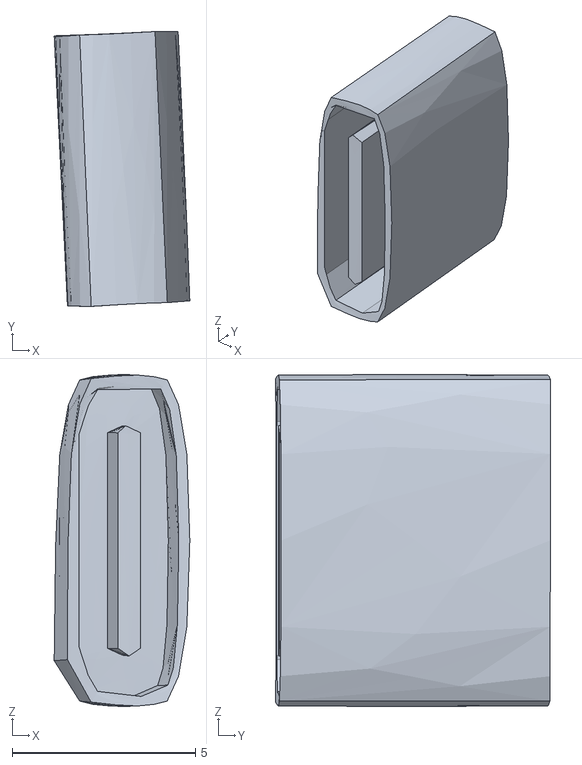
[picture p308: CAD file, 2026-05-26]
cad/print/trixig_redesign/for_bambu/trigger_button.stl
3.70 x 7.50 x 9.06
