lukketsvane/GK4_TRIXIG/cad/print/trixig_redesign/trixig_buildplate_stl_15.stl

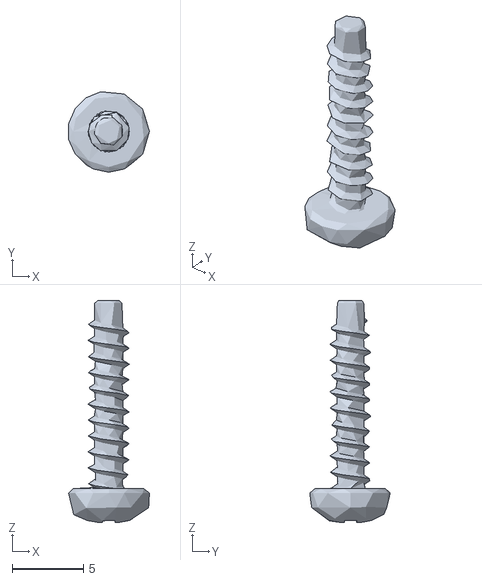
[picture p309: CAD file, 2026-05-26]
cad/print/trixig_redesign/trixig_buildplate_stl_15.stl
5.66 x 5.63 x 15.5
