lukketsvane/GK4_TRIXIG/cad/print/trixig_redesign/trixig_buildplate_stl_3_b.stl

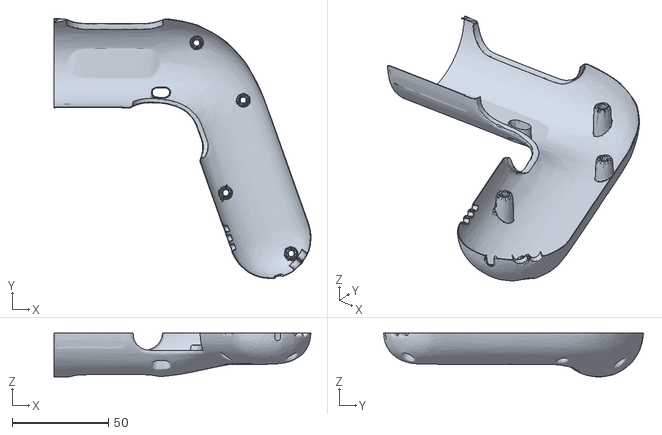
[picture p310: CAD file, 2026-05-26]
cad/print/trixig_redesign/trixig_buildplate_stl_3_b.stl
133.7 x 135.2 x 22.8
