lukketsvane/GK4_TRIXIG/cad/print/trixig_redesign/cap_slim_duplicate.stl

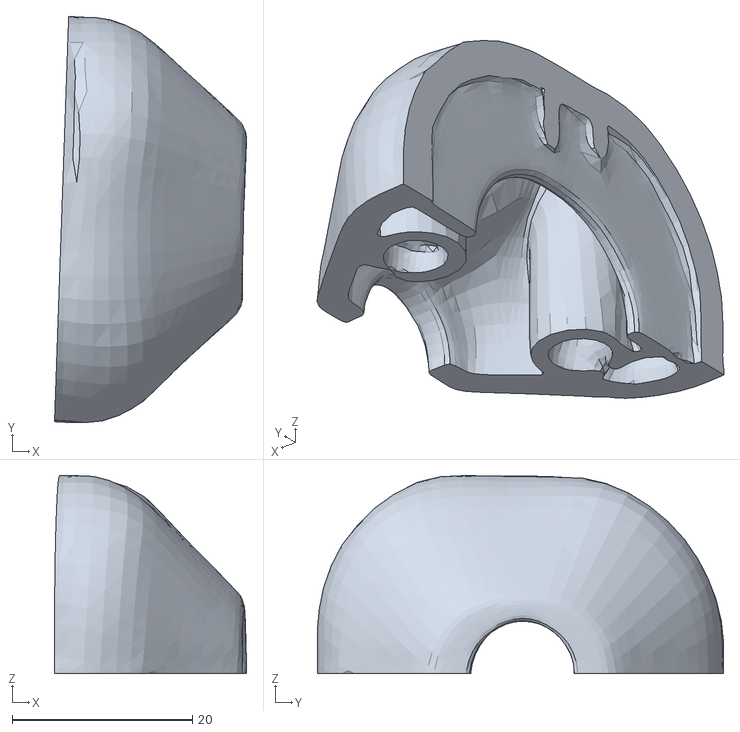
[picture p311: CAD file, 2026-05-26]
cad/print/trixig_redesign/cap_slim_duplicate.stl
21.3 x 45.1 x 22.0
