lukketsvane/GK4_TRIXIG/cad/print/trixig_redesign/for_bambu/housing_bottom_grip.stl

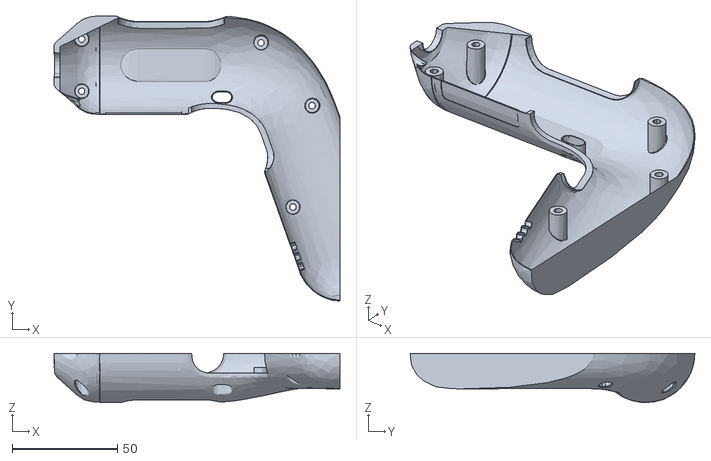
[picture p312: CAD file, 2026-05-26]
cad/print/trixig_redesign/for_bambu/housing_bottom_grip.stl
135.9 x 135.3 x 23.3
