lukketsvane/GK4_TRIXIG/cad/print/trixig_redesign/trixig_buildplate_stl_14.stl

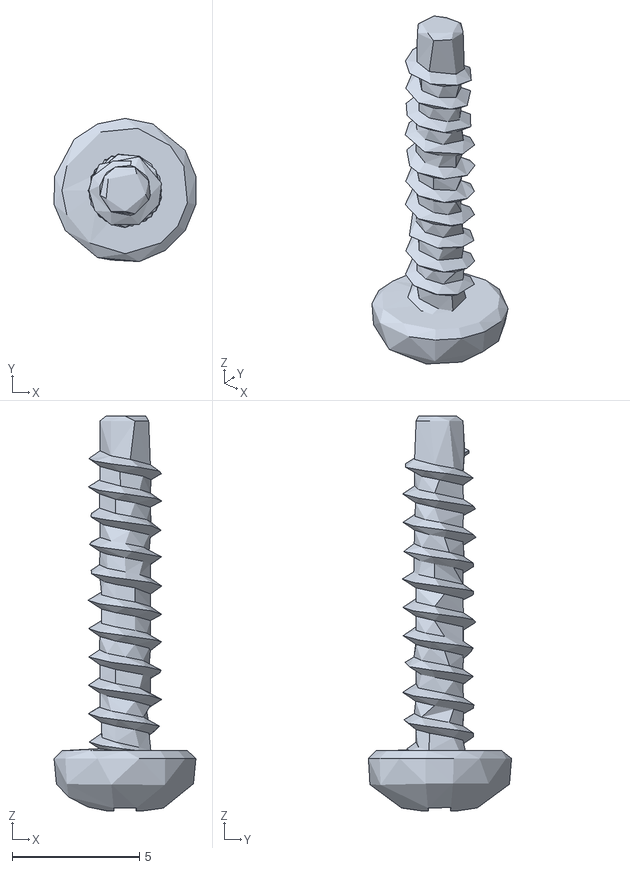
[picture p313: CAD file, 2026-05-26]
cad/print/trixig_redesign/trixig_buildplate_stl_14.stl
5.58 x 5.63 x 15.5
