lukketsvane/GK4_TRIXIG/cad/print/trixig_redesign/for_bambu/2.3mf

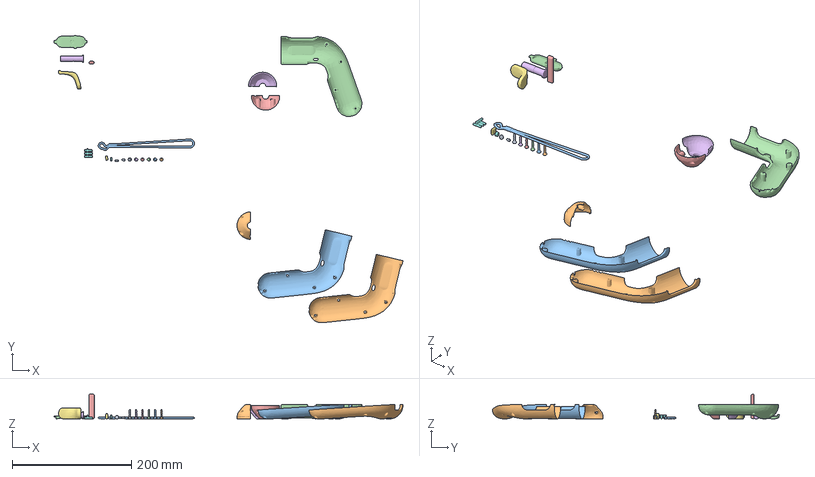
[picture p314: CAD file, 2026-05-26]
cad/print/trixig_redesign/for_bambu/2.3mf
586.3 x 482.9 x 41.8 mm
trixig_buildplate.stl_6
trixig_buildplate.stl_3_B x 2
trixig_buildplate.stl_7
trixig_buildplate.stl_12
trixig_buildplate.stl_13
trixig_buildplate.stl_14
trixig_buildplate.stl_15
trixig_buildplate.stl_16
trixig_buildplate.stl_17
trixig_buildplate.stl_18
trixig_buildplate.stl_19
trixig_buildplate.stl_20
trixig_buildplate.stl_21
trixig_buildplate.stl_3_A
cast.stl_1
cast.stl_2
cast.stl_3
