lukketsvane/GK4_TRIXIG/cad/print/trixig_redesign/trixig_buildplate_stl_3_a.stl

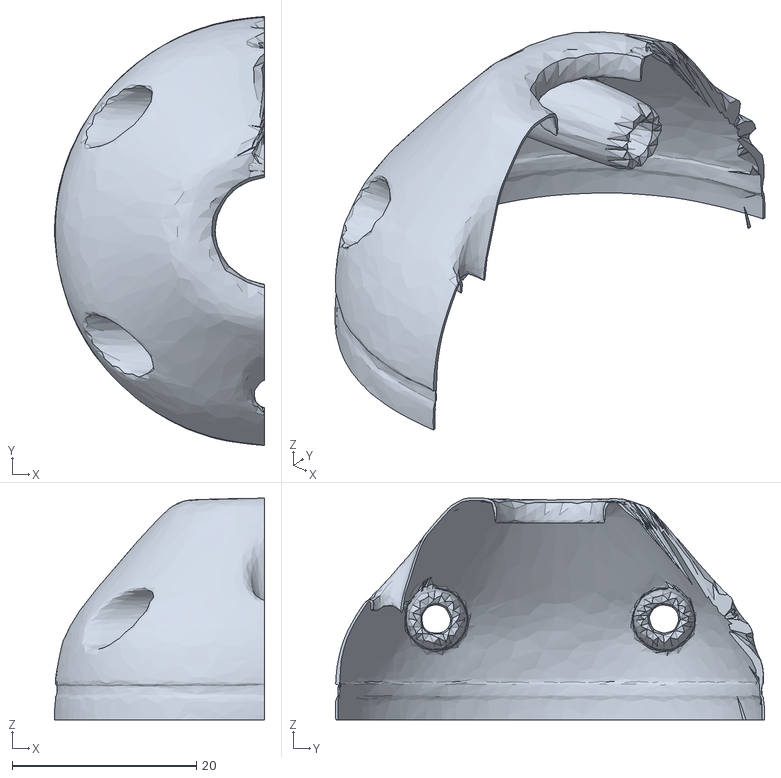
[picture p315: CAD file, 2026-05-26]
cad/print/trixig_redesign/trixig_buildplate_stl_3_a.stl
22.8 x 46.6 x 24.1
