lukketsvane/GK4_TRIXIG/cad/print/trixig_redesign/cap_slim.stl

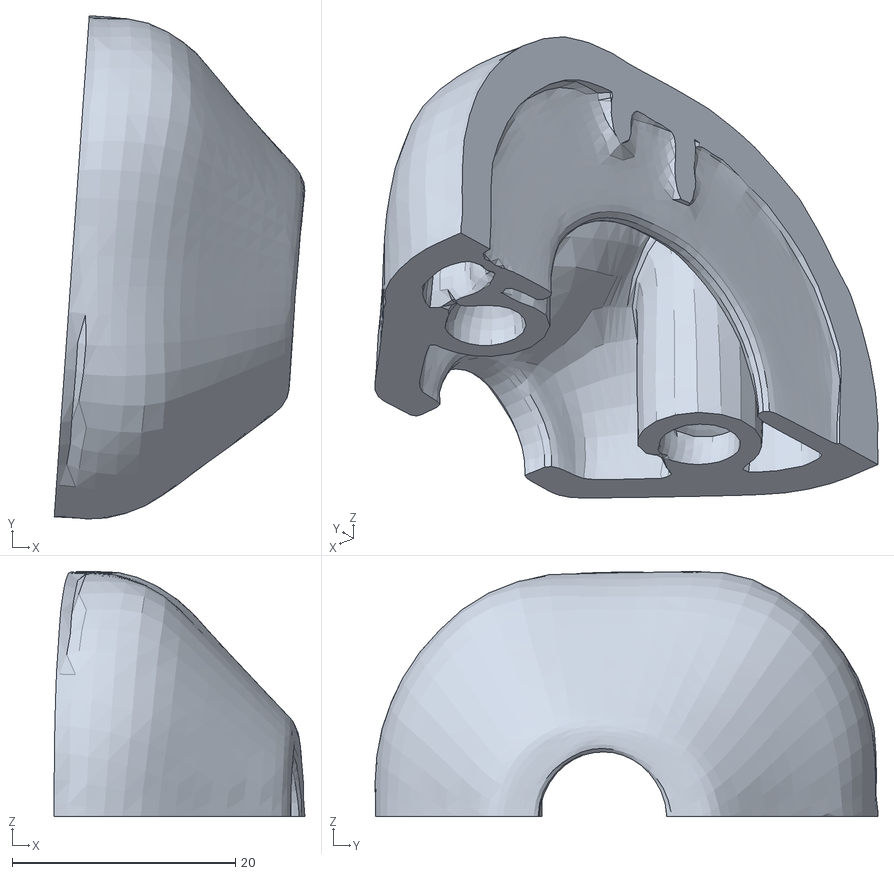
[picture p316: CAD file, 2026-05-26]
cad/print/trixig_redesign/cap_slim.stl
22.4 x 45.0 x 22.0
