lukketsvane/GK4_TRIXIG/cad/print/trixig_redesign/part_small_a.stl

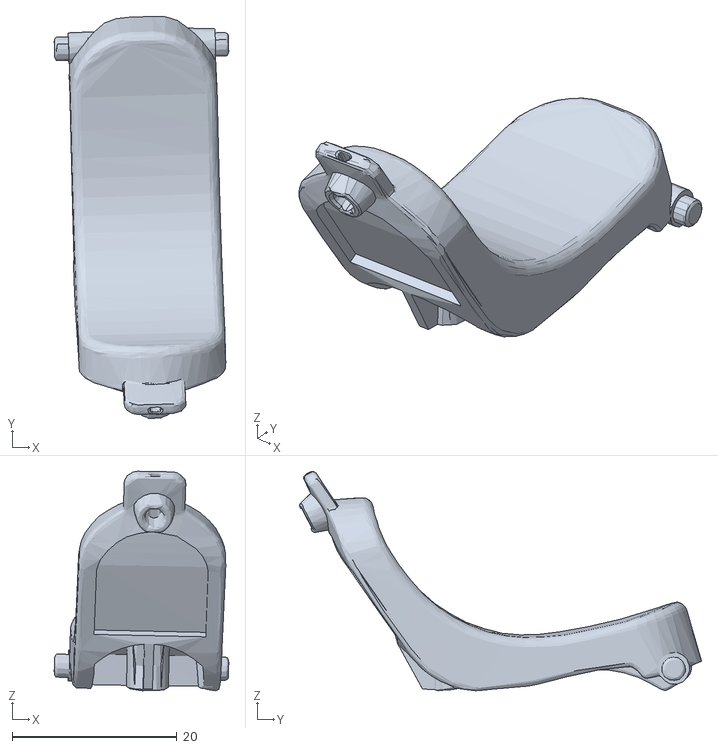
[picture p317: CAD file, 2026-05-26]
cad/print/trixig_redesign/part_small_a.stl
21.2 x 48.7 x 26.6
