lukketsvane/GK4_TRIXIG/cad/print/trixig_redesign/trixig_buildplate_stl_21.stl

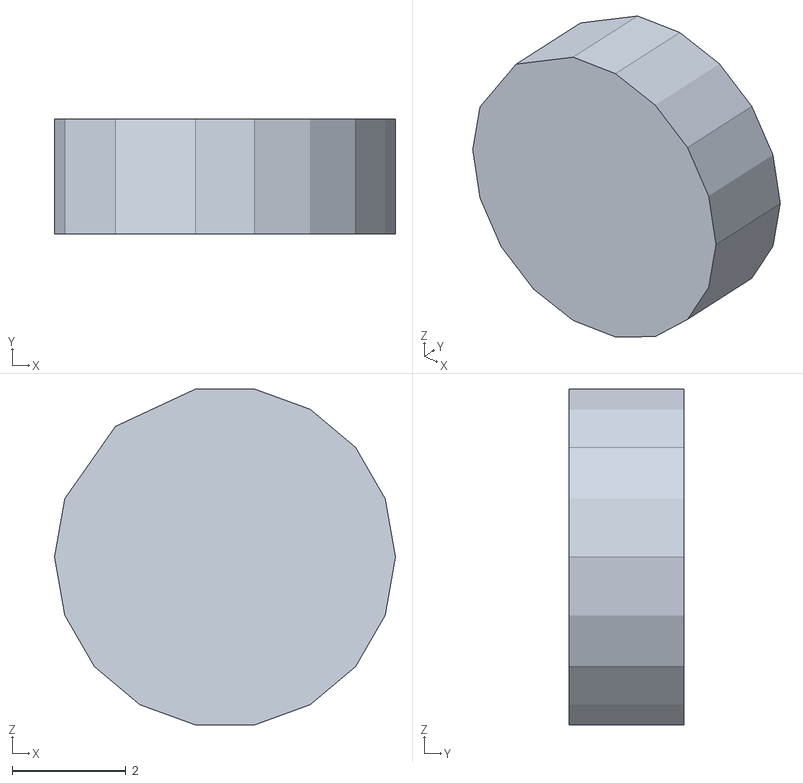
[picture p318: CAD file, 2026-05-26]
cad/print/trixig_redesign/trixig_buildplate_stl_21.stl
5.99 x 2.03 x 5.90
