lukketsvane/GK4_TRIXIG/cad/print/trixig_redesign/cast.stl

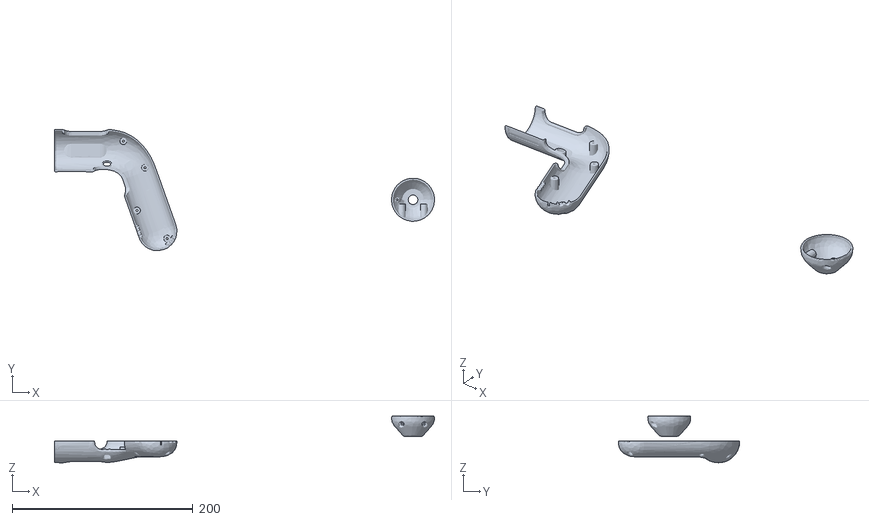
[picture p319: CAD file, 2026-05-26]
cad/print/trixig_redesign/cast.stl
421.0 x 134.2 x 51.6
