lukketsvane/GK4_TRIXIG/cad/print/trixig_redesign/housing_outer.stl

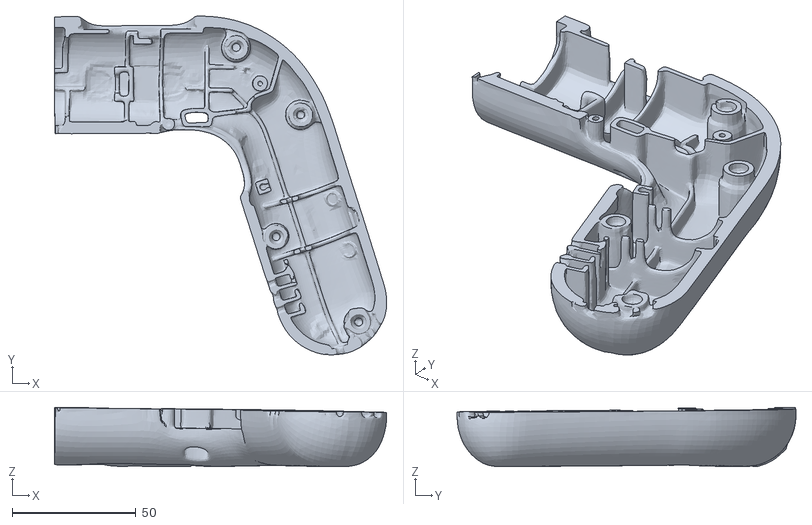
[picture p320: CAD file, 2026-05-26]
cad/print/trixig_redesign/housing_outer.stl
134.1 x 136.7 x 24.0
