lukketsvane/GK4_TRIXIG/cad/print/trixig_redesign/for_bambu/internal_wire.stl

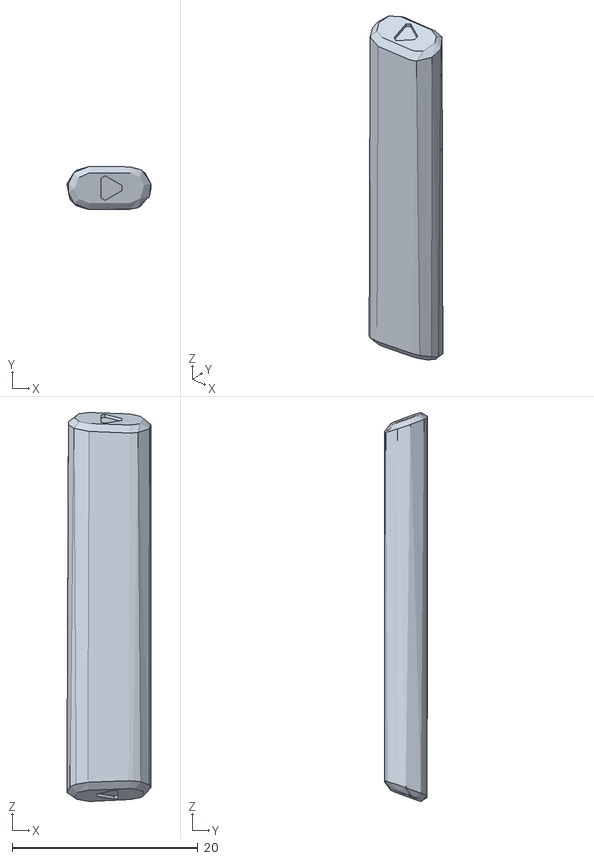
[picture p321: CAD file, 2026-05-26]
cad/print/trixig_redesign/for_bambu/internal_wire.stl
9.06 x 4.61 x 41.8
