lukketsvane/GK4_TRIXIG/cad/print/trixig_redesign/for_bambu/housing_bottom_tip.stl

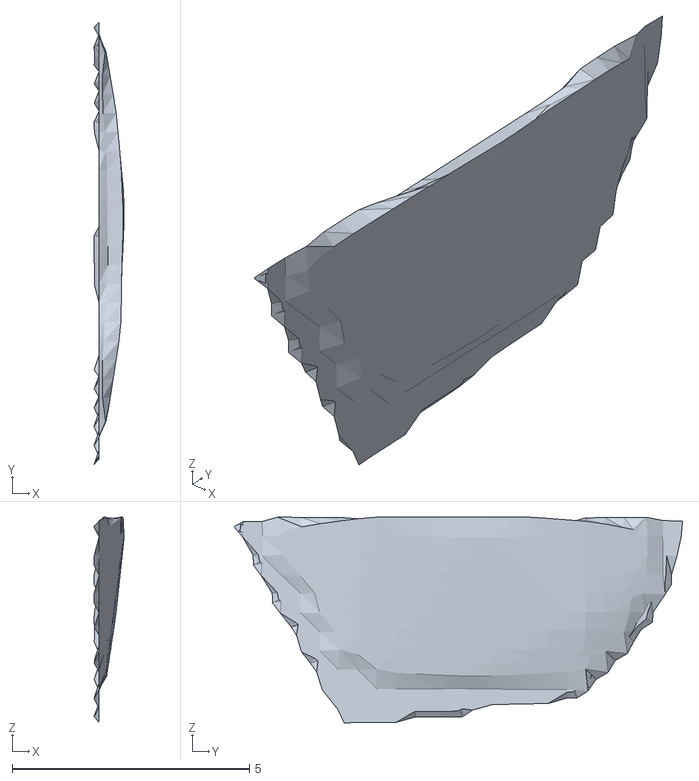
[picture p322: CAD file, 2026-05-26]
cad/print/trixig_redesign/for_bambu/housing_bottom_tip.stl
0.639 x 9.44 x 4.34
