lukketsvane/GK4_TRIXIG/cad/print/trixig_redesign/trixig_orginal.3mf

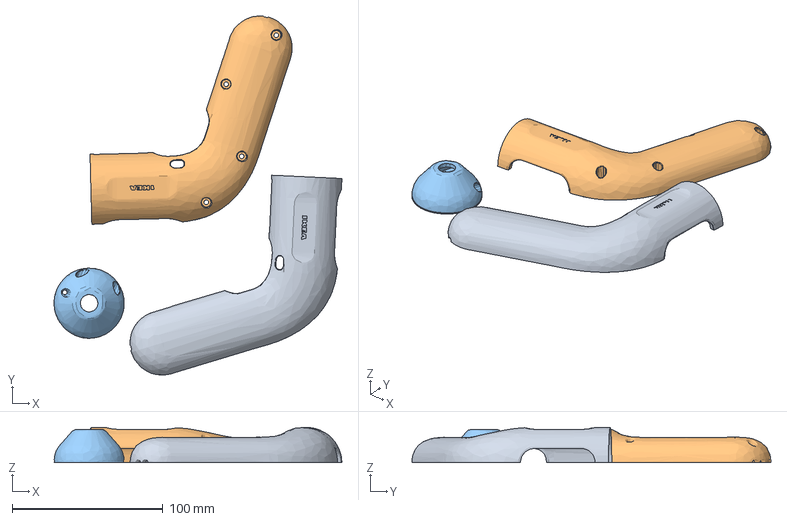
[picture p323: CAD file, 2026-05-26]
cad/print/trixig_redesign/trixig_orginal.3mf
191.0 x 238.2 x 23.3 mm
cast_for_bambu.stl_B_A
cast_for_bambu.stl_B_B
cast_for_bambu.stl_A
