lukketsvane/GK4_TRIXIG/cad/print/trixig_redesign/for_bambu/housing_top_tip.stl

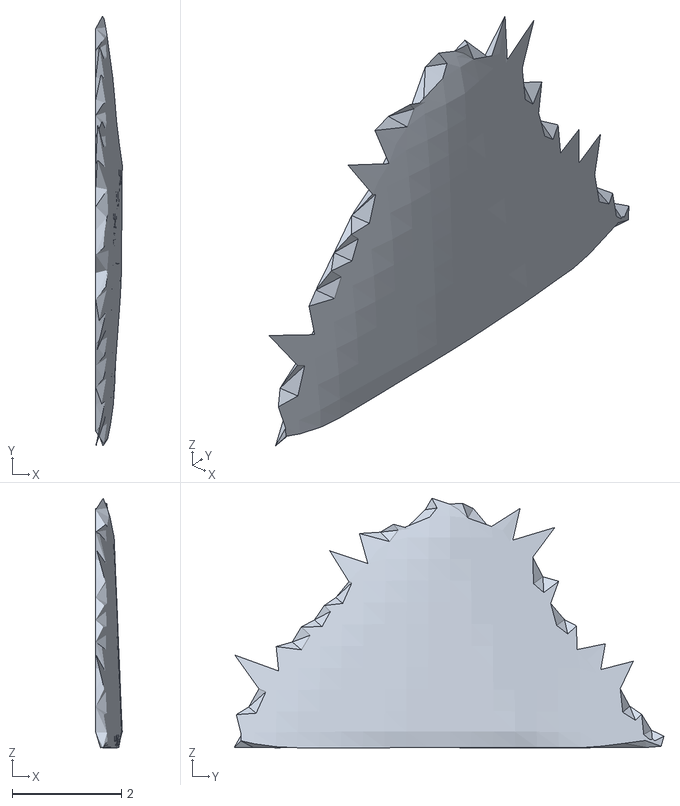
[picture p324: CAD file, 2026-05-26]
cad/print/trixig_redesign/for_bambu/housing_top_tip.stl
0.488 x 7.89 x 4.58
