lukketsvane/GK4_TRIXIG/cad/print/trixig_redesign/cast_for_bambu.stl

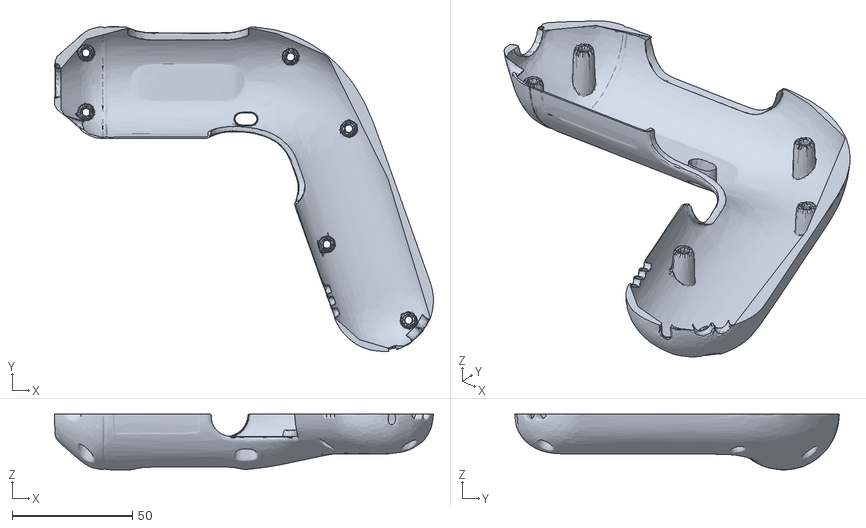
[picture p325: CAD file, 2026-05-26]
cad/print/trixig_redesign/cast_for_bambu.stl
157.9 x 135.3 x 23.3
