lukketsvane/GK4_TRIXIG/cad/print/trixig_redesign/housing_inner_half.stl

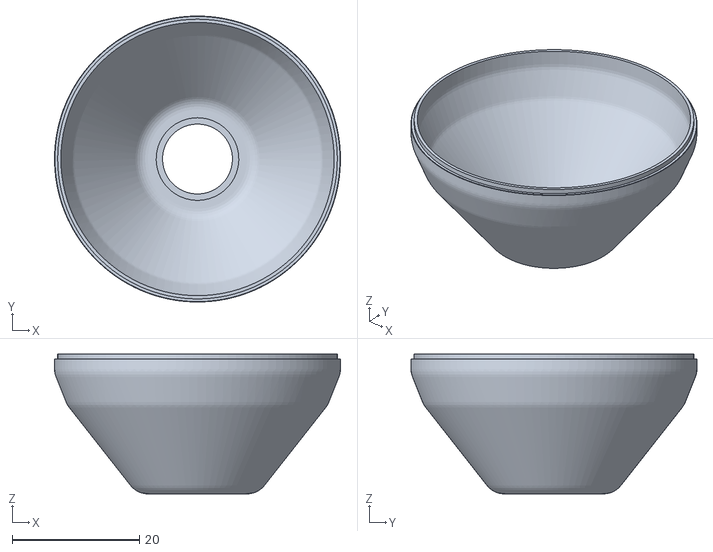
[picture p326: CAD file, 2026-05-26]
cad/print/trixig_redesign/housing_inner_half.stl
45.0 x 45.0 x 22.0
