lukketsvane/GK4_TRIXIG/cad/print/trixig_redesign/knob_oval.stl

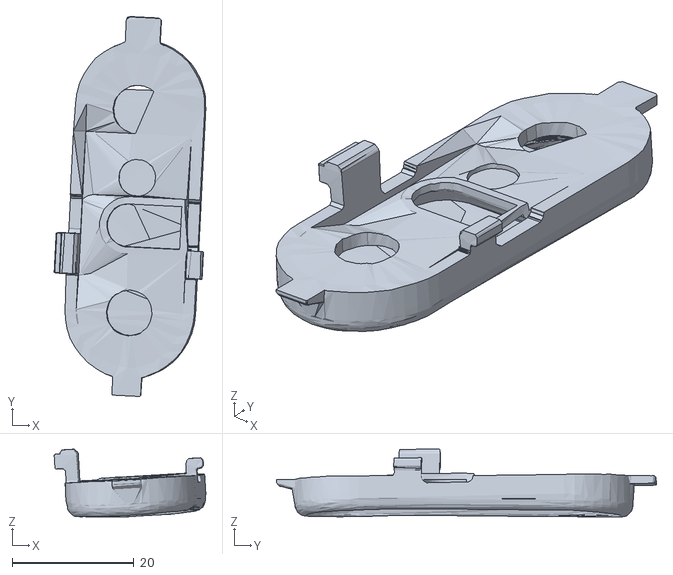
[picture p327: CAD file, 2026-05-26]
cad/print/trixig_redesign/knob_oval.stl
24.9 x 62.4 x 11.1
