lukketsvane/GK4_TRIXIG/methods/tjalve/tjalve_pdfpage_114_14_assembly_suboperations.png

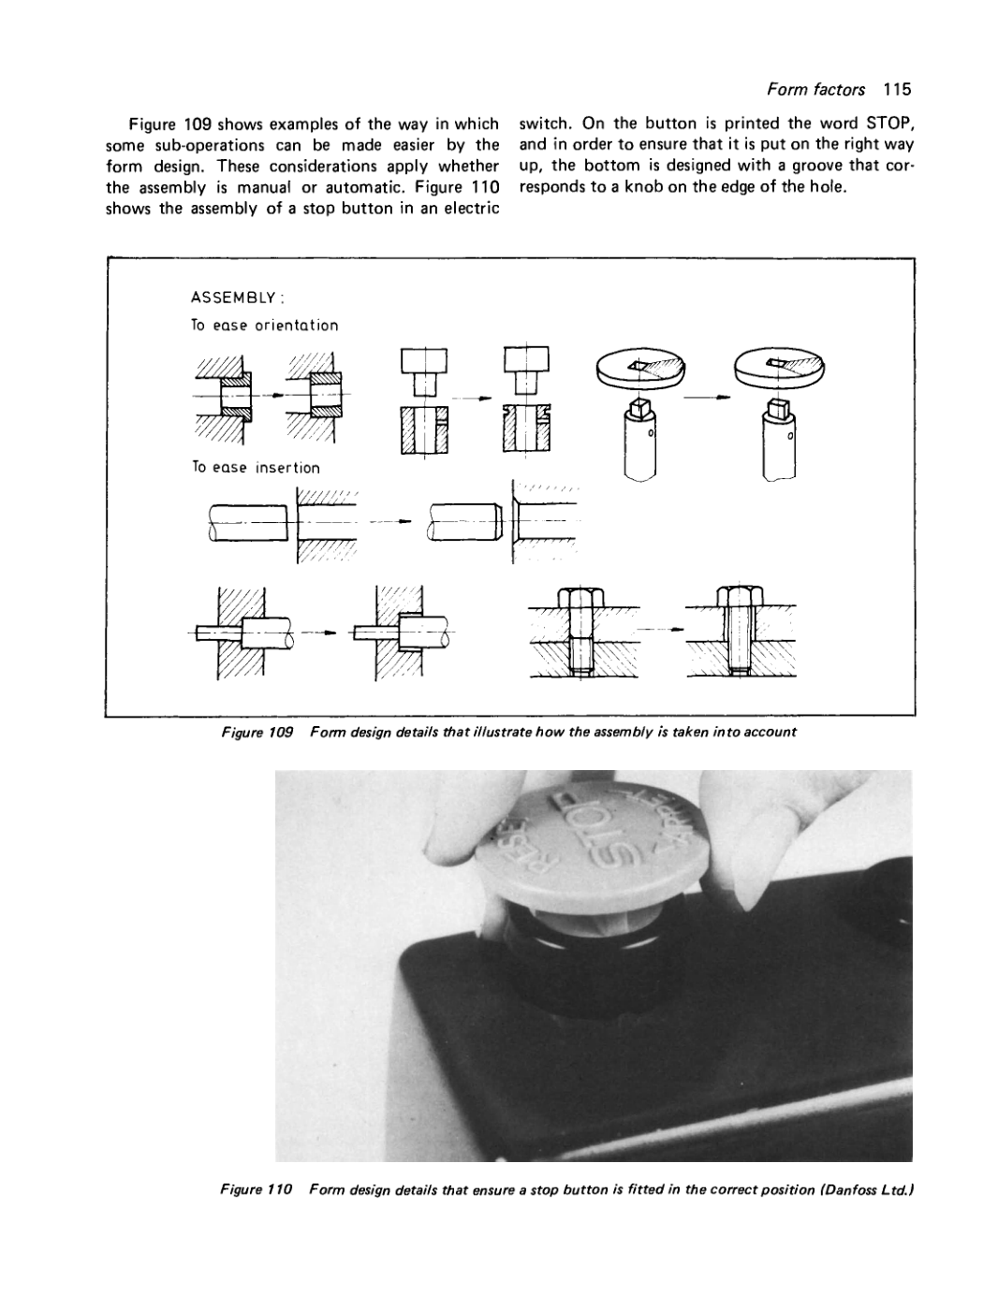
methods/tjalve/tjalve_pdfpage_114_14_assembly_suboperations.png
