lukketsvane/GK4_TRIXIG/methods/tjalve/tjalve_pdfpage_134_16_occasional_operations_repair.png

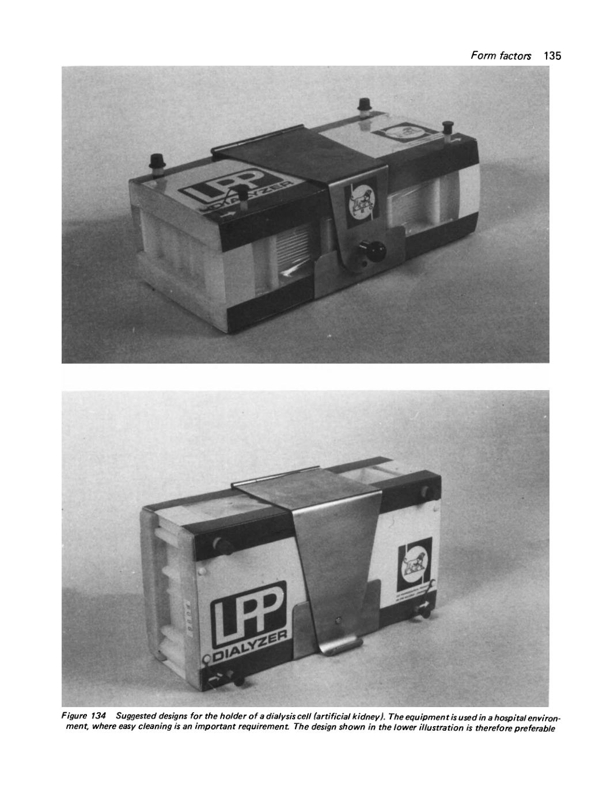
methods/tjalve/tjalve_pdfpage_134_16_occasional_operations_repair.png
