lukketsvane/GK4_TRIXIG/methods/tjalve/tjalve_pdfpage_017_03_search_examine_evaluate.png

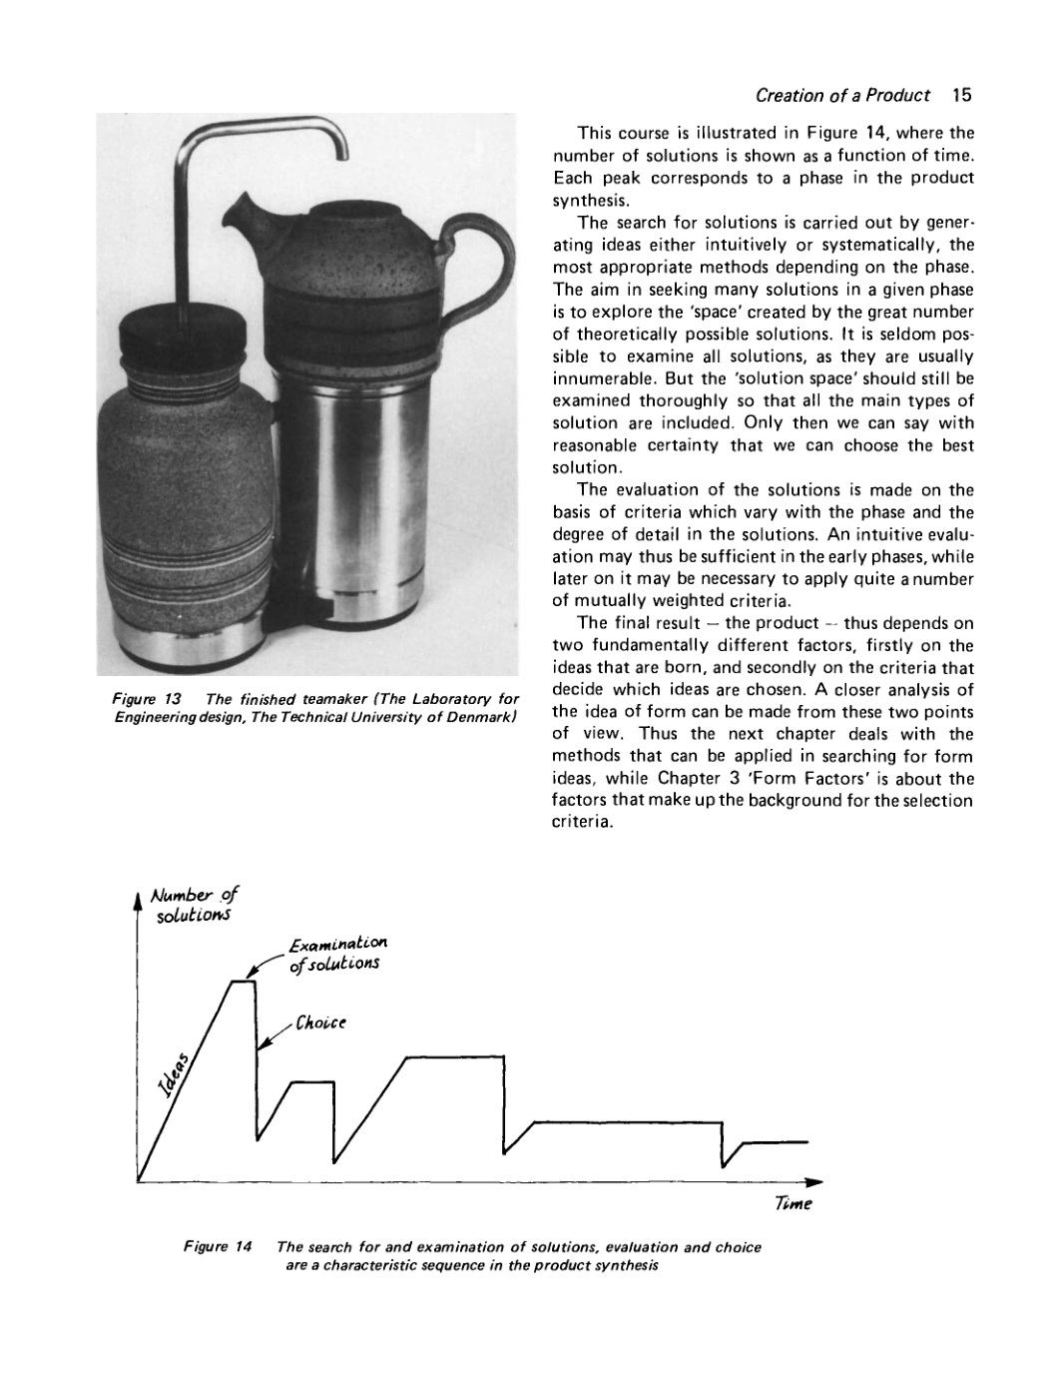
methods/tjalve/tjalve_pdfpage_017_03_search_examine_evaluate.png
