lukketsvane/GK4_TRIXIG/methods/tjalve/tjalve_pdfpage_139_17_destruction_evaluation.png

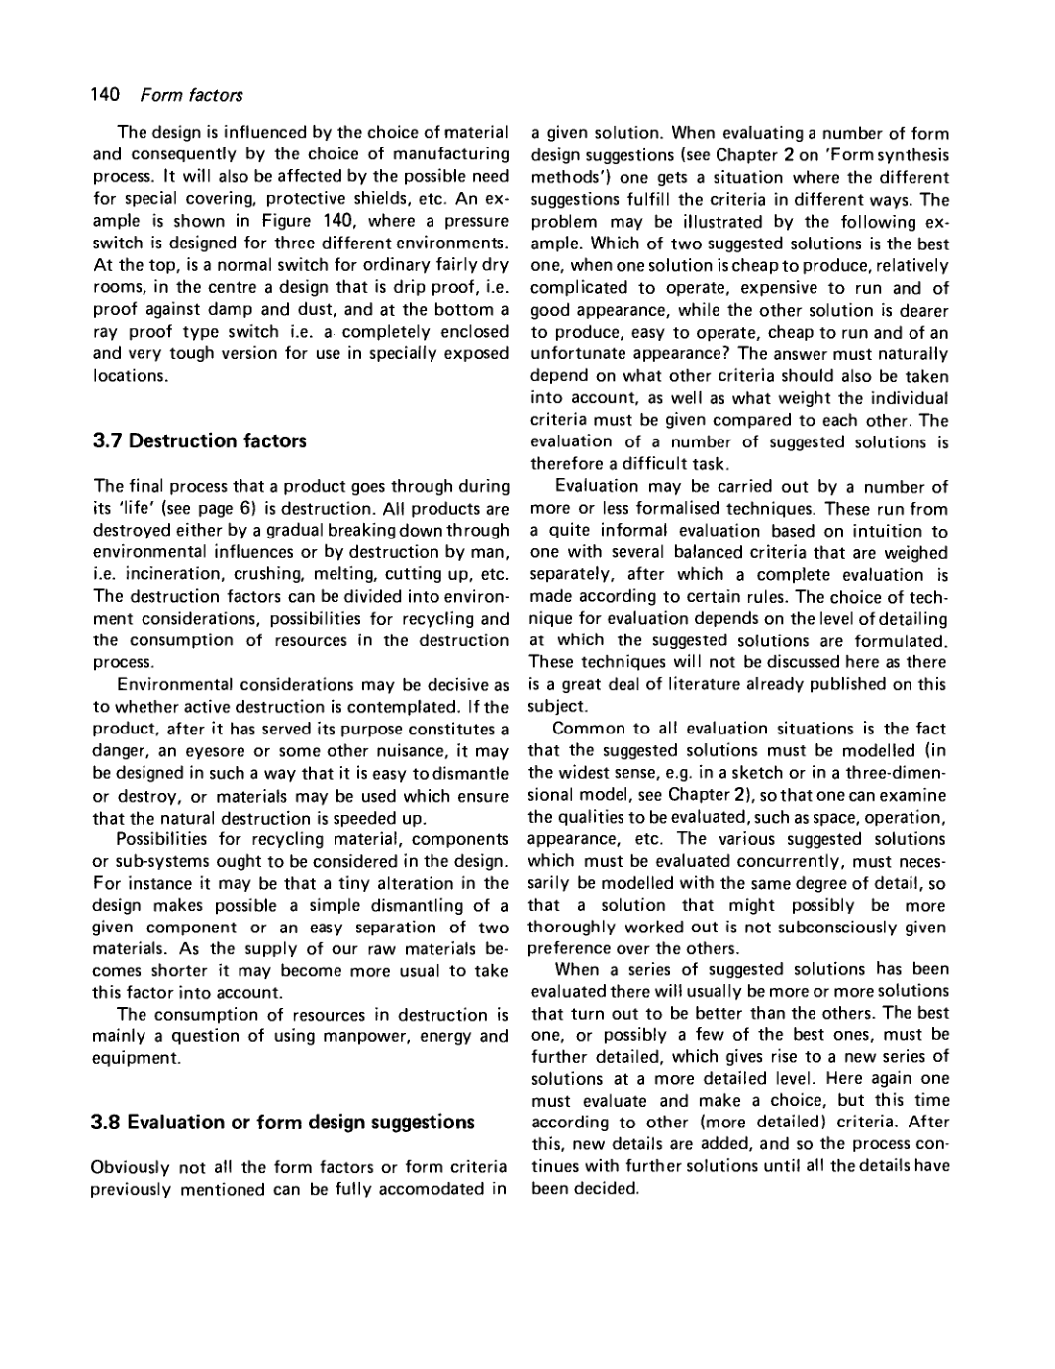
methods/tjalve/tjalve_pdfpage_139_17_destruction_evaluation.png
